atharveeee-netizen/beevil-knievel/LIMITATIONS.md

# ⚠️ BEEVIL KNIEVEL - Engineering Limitations & Scientific Disclosures
**Formal Scientific Constraints, Operational Boundaries, and Validity Scope**  
*Standard: IEEE-HART Peer Review Defense Standard*

---

## 1. DATASET LIMITATIONS & GENERALIZABILITY

### 1.1 Acoustic Training & Benchmark Datasets
- **Geographical & Subspecies Scope**: The real-world acoustic field validation in this repository uses annotated beehive recordings from Zenodo Record [1321278](https://doi.org/10.5281/zenodo.1321278) (NU-Hive and Open Source Beehive projects). These recordings represent European honeybee subspecies (*Apis mellifera carnica* and *Apis mellifera ligustica*) managed in temperate European climates (United Kingdom and Italy).
- **Subspecies Variance**: Subspecies indigenous to tropical or desert climates (e.g., *Apis cerana*, *Apis mellifera scutellata*, or *Apis dorsata*) exhibit differing baseline wingbeat frequencies and fanning dynamics that may require localized retuning of the 4 spectral sub-band filters.
- **Microphone Placement Sensitivity**: Spectral energy amplitudes depend on physical proximity to the active brood cluster. Placement of the INMP441 sensor outside the central comb gap results in acoustic attenuation of up to $6\text{ dB}$, which could delay queenless agitation detection if thresholds are not calibrated to the specific hive geometry.

---

## 2. SYNTHETIC DATA & MODEL PROVENANCE

### 2.1 Cloud Pathology Model (`CloudAdvisorModel`)
- **Parametric Empirical Distributions**: The 1500-sample training dataset (`Synthetic_Hive_Parametric_Dataset.csv`) used to train the Scikit-Learn Random Forest model is **synthetic data** generated from parametric Gaussian distributions.
- **Grounding in Literature**: Distribution parameters ($\mu, \sigma$) are derived directly from empirical ranges published in scientific apiculture literature:
  - Brood thermoregulation dynamics: Southwick & Heldmaier (1987).
  - Colony acoustic spectral shifts: Ferrari et al. (2008), Bencsik et al. (2011).
  - Respiration and metabolic $\text{CO}_2$ spikes: Sensirion Apiculture Application Notes.
- **Operational Reality**: While the model achieves 100% classification accuracy on holdout test splits drawn from these parametric distributions, real-world apiaries experience complex multi-variable interactions (e.g., simultaneous pesticide exposure and starvation) that require continued multi-season empirical calibration.

---

## 3. ON-NODE ALGORITHM BOUNDARIES

### 3.1 CUSUM Thermal Change-Point Detection
- **Progressive Cooling Lead Time**: The claim that CUSUM provides up to a **72-hour early warning** is validated against modeled progressive thermal degradation scenarios where colony thermoregulation fails gradually. In events involving catastrophic physical box destruction or sudden chemical poisoning, cluster collapse occurs faster than the 72-hour window.
- **Diurnal Sensitivity**: The slack parameter $K = 0.15^\circ\text{C}$ successfully rejects normal diurnal oscillations in standard double-walled Langstroth hives. However, single-walled hives deployed in extreme desert climates ($> 45^\circ\text{C}$ day, $< 10^\circ\text{C}$ night) may require dynamic temperature-dependent slack adjustments.

### 3.2 Environmental Acoustic Noise Rejection
- **Heavy Rain Clatter**: High-velocity raindrops striking thin metallic hive roofs produce acoustic energy in the $200 - 600\text{ Hz}$ band that closely mimics pre-swarm worker piping.
- **Cross-Modal Suppression**: To prevent false swarm alarms, the platform mandates cross-modal verification: acoustic swarm alerts are suppressed unless accompanied by a corresponding $\text{CO}_2$ respiration spike ($> 2000\text{ ppm}$) and diurnal solar lux ($> 10,000\text{ Lux}$).

---

## 4. HARDWARE & SENSOR CONSTRAINTS

### 4.1 BME688 MOX Gas Sensor Baseline Drift
- Metal-oxide (MOX) gas sensors undergo baseline resistance drift over 6 to 12 months due to humidity cycling and sensor poisoning by atmospheric siloxanes. A baseline calibration cycle must be executed at the beginning of each apiculture season.

### 4.2 LIS3DH Accelerometer Orientation
- The knockdown tamper alarm requires the node to be rigidly fastened to the hive brood box. Loose mounting introduces structural vibration artifacts from heavy wind gusts that could trip false tamper alerts.

### 4.3 Solar Energy Harvesting in Extended Winter Overcast
- The 3000 mAh LiPo battery provides 90 days of autonomous operation under standard 5-minute transmission duty cycles without any solar input. However, in high-latitude winter regions experiencing $> 100$ consecutive days of heavy cloud cover and temperatures $< -10^\circ\text{C}$, internal battery self-discharge and electrolyte freezing reduce effective capacity by up to 35%.

---

## 5. SIMULATION VS PHYSICAL MEASUREMENT BOUNDARIES

| Engineering Domain | Simulated Metric | Real-World Physical Measurement Boundary |
|---|---|---|
| **ANSYS HFSS RF** | $S_{11} = -24.75\text{ dB}$, Range $= 5.11\text{ km}$ | Range is an analytical Friis link budget derived from simulated far-field gain; field range is subject to non-line-of-sight foliage clutter and Fresnel zone obstruction ($3.2 - 4.5\text{ km}$ typical). |
| **ANSYS Icepak Thermal** | Junction $T_j = 64.45^\circ\text{C}$ @ $45^\circ\text{C}$ amb | Simulated under quiescent ambient air. Forced air convection from natural wind ($1 - 3\text{ m/s}$) reduces physical junction temperatures by $5 - 12^\circ\text{C}$. |
| **ANSYS Maxwell EMI** | Shielding $\text{SE} = 288.5\text{ dB}$ | 288.5 dB is a theoretical analytical result for an unbroken shield. Practical RF testing in an anechoic chamber is bounded by the $100 - 110\text{ dB}$ dynamic range of lab spectrum analyzers. |
