atharveeee-netizen/beevil-knievel/docs/resources/OPEN_SOURCE_REFERENCES.md

# Beevil Knievel - Public Datasets & Industry Standards Index

---

## 📊 Public Audio Datasets for AI Model Training

1. **Zenodo Public Bee Audio Dataset**
   * **Resource**: Public Audio Benchmark for Beehive Swarming & Health Classification
   * **Usage**: Benchmark dataset for training our 200 Hz - 400 Hz acoustic swarming and queenlessness detection models.

2. **Utah State University Bee Audio Dataset**
   * **Resource**: Public Hive Sound Audio Dataset
   * **Usage**: Multi-season continuous acoustic hive recordings used to train noise-suppression algorithms.

---

## ⚡ Open-Source Firmware & Protocol Libraries

1. **RadioLib Sub-GHz LoRa C++ Protocol Library**
   * **Usage**: Hardware abstraction driver for SX126x / nRF52840WL sub-GHz radios.

2. **DallasTemperature 1-Wire C++ Library**
   * **Usage**: Reading multi-drop digital temperature sensors on a single GPIO bus.
