atharveeee-netizen/beevil-knievel/simulations/Beehive_Monitoring_ANSYS_Simulations_Presentation.pptx

## Simulations on Ansys for Beehive Monitoring Device

## Simulation 1: 868 MHz Antenna & Wireless Link Simulation

We are testing Electromagnetics (EM) & Far-Field Wave Propagation. We want to check that our 868 MHz wire antenna connected to the STM32WLE5 (Wio-E5) transfers RF power cleanly through its trace without internal reflections and broadcasts a 3D signal capable of spanning 4km.
For this, we’ll require a Software Module: Ansys HFSS (High-Frequency Structure Simulator) inside Ansys Electronics Desktop (AEDT). We want to evaluate the radiation efficiency and impedance matching of our 868/915 MHz 86mm quarter-wave wire antenna connected to the STM32WLE5 (Wio-E5) microcontroller before manufacturing.
This directly addresses the IEEE HART Coverage Range and Temperature Accuracy KPI by proving that our node can successfully transmit telemetry through a wooden hive structure across long distances(specifically, pass the 4km Line-Of-Sight).

## STEPS of EXECUTION

To execute this, we will
1. Import our 2-layer PCB layout (.ODB++)
2. Construct the 86mm copper wire antenna geometry on the SMA pad and
3. Assign material properties for the FR4 substrate, copper traces, and surrounding wooden hive box.
We will then establish a 3D Air Box with a radiation boundary at λ/4 distance, assign a 50 Ω Lumped Port source at the RF output pin, and execute an interpolating frequency sweep from 700 MHz to 1 GHz. From this setup, we expect to generate an S11 Return Loss plot displaying a sharp resonance dip below -10 dB at 868 MHz, alongside a 3D Far-Field Radiation Pattern showing an omnidirectional gain distribution (> 2 dBi). The design significance of this outcome is that it proves RF energy actually radiates into space rather than reflecting back into the STM32 chip, preventing power loss and validating our long-range claim.

## Simulation 2: Power Integrity & Transient Voltage Droop

This simulation relies on Ansys SIwave and Ansys Electronics Desktop (Nexxim Circuit) to conduct transient Power Distribution Network (PDN) and AC/DC impedance testing.
Our goal is to verify that the 3.3V power rail remains stable during high-current radio transmission bursts, which directly addresses the Energy Consumption KPI and overall system reliability.
By confirming that our ultra-low-power TPS7A02 LDO regulator and decoupling capacitor network handle peak currents smoothly, we ensure the MCU will not experience brownout resets.

The execution steps involve importing the board layout stackup with defined 3.3V and GND planes into SIwave, assigning the regulator VRM output, and modeling the 100 nF and 10 µF decoupling capacitors with their equivalent series resistance. We then apply a transient current load at the STM32 power pin that jumps from a 0.3 µA sleep state to a 120 mA transmit burst for 60 ms, running a time-domain co-simulation over 100 ms. We expect to extract a transient voltage waveform showing that the 3.3V rail droops no lower than ~3.22V during transmission, as well as a PDN impedance curve confirming resistance stays below 1.375 Ω across frequencies up to 100 MHz. The significance of this simulation is that it mathematically guarantees node runtime stability under battery power, proving optimal energy efficiency.

## Simulation 3: Battery & Enclosure Thermal Isolation

This simulation uses Ansys Icepak to evaluate conjugate heat transfer, covering both thermal conduction and natural air convection.
We are performing this analysis to ensure that internal heat generated by the 1000mAh LiPo battery during solar charging or by the MCU during active computing does not conduct into our ambient temperature sensor.
This supports the Temperature Accuracy KPI of IEEE HART by confirming that device self-heating will not introduce artificial offsets into our ambient sensor readings.

## STEPS OF EXECUTION

To set up the simulation, we will import the 3D CAD assembly of our 60 × 50 mm enclosure (.STEP) and PCB into Icepak, assigning a heat dissipation load of 0.15 W to the LiPo battery and 0.05 W to the MCU. We will then set the surrounding air domain to 35°C to match internal hive conditions and run the fluid-thermal solver to compute copper plane conduction and natural airflow.
The expected outcomes are a 3D thermal heat map showing localized heat at the battery (~38°C) while the surrounding board remains cool, along with a thermal cross-section cut plane verifying that the ambient DS18B20 sensor footprint maintains an elevation of <0.1°C relative to internal hive air. The significance of this result is that it proves our board layout thermally isolates critical sensing components, preserving the ±0.5°C temperature accuracy required to evaluate bee colony health accurately.
