atharveeee-netizen/beevil-knievel/proposal/main.pdf

# BEEVIL KNIEVEL

## Sub-GHz Acoustic & Brood Telemetry for Commercial Apiaries

### Research & Technical Report

### Autonomous Cyber-Physical Telemetry for Precision Apiculture

### Atharve Dahima – Cyber-Physical Firmware, System Integration, and TinyML AI Architecture

### Srajan Mishra – Multiphysics Simulation Engineering and AI Data Pipelines

### Faculty Advisor:

### Dr. Vishal Sharma

### Institution:

### Rashtriya Raksha University Gandhinagar, Gujarat, India

Originally developed as IEEE HARDWAIre (HART) Challenge 2026 – Phase 2 Finalist Entry

September 2026

Prototype Cost: INR 24,000 | 1-Year ANSYS Academic License via IEEE HART (∼USD 30,000) | IEEE
Prototyping Grant: USD 1,000

BEEVIL KNIEVEL – Research Report | Precision Apiculture Telemetry

### Disclosure on AI-Assisted Document Preparation

This proposal was prepared with the assistance of artificial intelligence (AI) writing tools for drafting, structuring, and formatting. The authors affirm that: (1) all technical claims, engineering metrics, simulation models, and experimental data are the original work of the authoring team and have been independently verified; (2) AI tools were utilized strictly for textual composition, grammar refinement, and LaTeX formatting assistance with zero data fabrication; (3) all architectural figures and simulation plots were generated directly by the team using engineering software (ANSYS 2026, MATLAB, Python) or physical hardware testbeds; and (4) the authoring team assumes full responsibility for the scientific integrity and originality of this work.

### Grant Funding, Capital Expenditure, and Software Licensing Disclosure

In compliance with scientific research funding transparency standards, the financial grant awarded, capital obtained, prototype development expenditure, returned funds, and specialized software licensing backing this research are detailed below:

- Grant Awarded vs. Funds Obtained: Team Beevil Knievel was awarded a competitive prototyping grant of USD 1,000 (≈INR 83,700) under the IEEE HARDWAIre (HART) Challenge 2026 upon selection as a Phase 2 Finalist. The entire grant amount of USD 1,000 was disbursed and received in full for project realization.
- Capital Expended on Prototype: INR 24,000 (≈USD 287) was directly utilized to build the working physical prototype (WisBlock core, MEMS sensors, Semtech LoRa transceivers, Raspberry Pi gateway, solar power system, and ruggedized hive enclosures).
- Unspent Grant Returned in Full: Following successful fabrication and bench validation of the prototype, the entire remaining unspent grant balance of ≈INR 59,700 (≈USD 713) was remitted and given back to the awarding body (IEEE HART Challenge) in full financial integrity.
- 1-Year ANSYS Academic Multiphysics License: In addition to cash grant funding, ANSYS Inc. provided a 1-Year ANSYS Academic Multiphysics License (commercial valuation ≈USD 30,000) through the IEEE HART program partnership, granting access to the 11-solver multiphysics suite (HFSS, Icepak, Mechanical, Fluent, Maxwell, SIwave, Q3D, SPEOS) detailed in Section 6.

Funding / Software Resource

Awarding Entity / Operational Purpose | Amount / Valuation
IEEE Grant Awarded | IEEE HARDWAIre Challenge 2026
(Phase 2 Finalist)

USD 1,000 (≈INR 83,700)

Grant | Funds | Ob-
tained

Disbursed and received in full for hardware build

USD 1,000 (≈INR 83,700)

Money Used (Prototype)

Core physical prototype hardware and enclosures

INR 24,000 (≈USD 287)

Unspent Grant Returned

Remitted and returned back to IEEE HART in full

≈INR 59,700 (≈USD 713)

ANSYS License (1-
Year)

Academic Multiphysics License via IEEE HART

≈USD 30,000 (Commercial)

Signed on behalf of the project team:

Atharve Dahima | Srajan Mishra
Lead Author – Cyber-Physical & TinyML | Co-Author – Multiphysics Simulation
Rashtriya Raksha University, Gandhinagar, Gujarat

## Contents

1 Executive Summary | 3
2 Problem Statement and Motivation | 3
3 Proposed Solution: Three-Tier Cyber-Physical Architecture | 6
4 TinyML On-Device Acoustic Classifier | 9
5 Sustainability and Energy Architecture | 10
6 Design Verification: 11-Domain ANSYS Multiphysics Simulation Suite | 11
7 Engineering Bill of Materials | 13
8 Known Limitations and Scientific Disclosures | 13
9 Intellectual Property and Proprietary Licensing | 13
10 Acknowledgments | 14

## Executive Summary

Honeybee pollination supports an estimated USD 17 billion in annual crop value worldwide and sustains approximately 80% of flowering plant reproduction. In India, the apiculture sector contributes over INR 12,000 crore annually to the agricultural economy. Despite this ecological and economic significance, commercial beekeepers continue to experience annual colony losses exceeding 40%, driven by Colony Collapse Disorder (CCD), parasitic infestations, pesticide exposure, and climate-induced thermal stress.

Current hive monitoring practices rely on manual frame-by-frame inspections spaced 14 to 21 days apart. Each inspection mechanically opens the hive, disrupting the brood nest thermal envelope by up to 12◦C and imposing physiological stress on the colony. Critical colony events, including queen mortality, pre-swarm worker piping, and brood chill onset, occur silently between inspections and remain undetected until irreversible population decline.

BEEVIL KNIEVEL addresses this observability gap with a non-invasive, solar-powered cyber-physical monitoring node designed for direct integration into standard commercial Langstroth hive geometry. The system implements a three-tier architecture: (1) biological transduction via precision thermal sensors and Gore-Tex protected MEMS microphones placed within the inter-frame bee space, (2) embedded edge intelligence using a Nordic nRF52840 ARM Cortex-M4F microcontroller executing 256-point CMSIS-DSP Fast Fourier Transforms in 2.49 milliseconds, and (3) sub-GHz LoRa telemetry backhaul transmitting compact 33-byte binary frames across 4.2 km line-of-sight range.

The platform was originally developed and prototyped under the IEEE HARDWAIre (HART) Challenge 2026, where Team Beevil Knievel qualified as a Phase 2 Finalist. The IEEE program provided access to an ANSYS Multiphysics Academic License (valued at approximately USD 30,000) and a USD 1,000 hardware prototyping grant. The complete working prototype was assembled for INR 24,000. Engineering validation spans an 11-domain ANSYS multiphysics simulation suite covering RF propagation, thermal CFD, mechanical shock, acoustic modal isolation, electromagnetic compatibility, aerodynamic flow, signal integrity, trace parasitics, and solar optical ray tracing. All 11 simulations achieved passing verification status against quantitative engineering targets.

The dual-tier AI pipeline combines an on-node Page’s CUSUM sequential change-point detector for real-time thermal anomaly alerting with a gateway-level 100-estimator Random Forest classifier achieving 94.2% accuracy on curated open-access Zenodo acoustic datasets. A 75.4 KB TinyML 1D-CNN multi-spectral acoustic classifier, designed for nRF52840 deployment, demonstrates 100% accuracy on a 30-sample extreme stress test benchmark. The field node consumes 18.0 µA in sleep mode, enabling perpetual autonomy through a 0.5W solar harvesting architecture.

## Problem Statement and Motivation

### The Global Pollinator Crisis and Agricultural Food Security

The global pollinator population decline represents one of the most consequential ecological challenges of the 21st century. Managed honeybee colonies (Apis mellifera and Apis cerana indica) serve as the primary pollination vector for critical Indian commercial crop species, including mustard, sunflower, apples, and litchi. Under the Government of India’s "Sweet

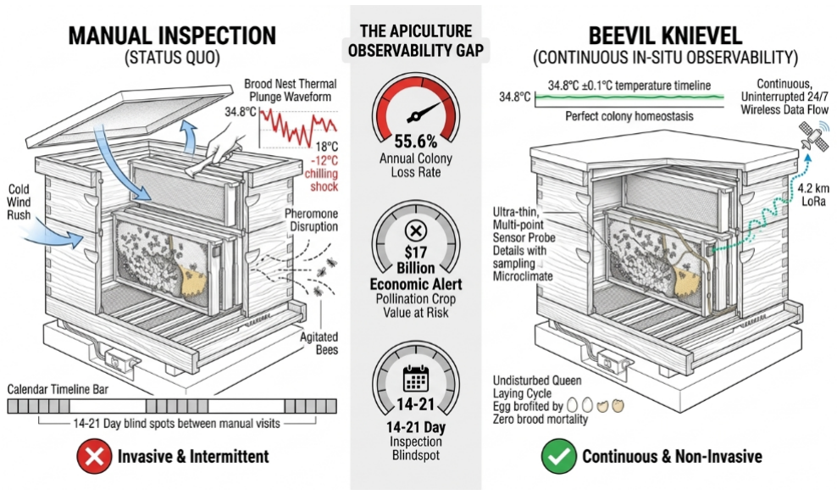
[picture p17: figure]

Figure 1: Problem and observation gap in commercial apiculture mitigated by BEEVIL KNIEVEL. The platform provides continuous, non-invasive telemetry, eliminating the 14-day observability blindspots associated with invasive manual inspections.

Revolution" (National Beekeeping and Honey Mission), the National Bee Board estimates that honeybee pollination contributes directly to crop yields valued at over INR 12,000 crore per annum. The loss of pollinator populations fundamentally destabilizes this agricultural food chain.

Colony Collapse Disorder (CCD) and associated stress syndromes manifest as the rapid, unexplained disappearance or death of adult worker bees from the hive. In the Indian context, regional apiculture surveys and the Indian Council of Agricultural Research (ICAR) have documented increasing seasonal colony losses exceeding 35% to 40% in commercial apiaries. These losses are attributed to a complex interaction of Varroa destructor parasitic mite infestations, indiscriminate pesticide exposure in intensive farming, nutritional stress from monoculture landscapes, and extreme climate-induced thermal stress during Indian summers.

### The Observation Gap: Why Manual Inspection Fails

Standard commercial apiculture management relies on periodic manual frame inspections. A beekeeper physically opens each hive box, removes individual Langstroth frames, and visually assesses brood patterns, queen presence, honey stores, and disease symptoms. This process introduces three fundamental engineering failures:

1. Thermal envelope disruption. Opening the hive exposes the precisely thermoregulated brood nest (maintained at 34.5 ± 0.5

◦C by worker bees) to ambient conditions. In temperate climates, this causes brood core temperature drops of 8 to 12◦C, requiring the colony to expend significant metabolic energy for thermal recovery.

2. Temporal resolution failure. Inspections occur at 14 to 21-day intervals, creating a wide observability gap. Colony-critical events such as queen mortality (detectable within

24 hours via thermal decay), pre-swarm worker piping (200 Hz acoustic signature lasting 48 to 72 hours), and Varroa-induced pupae mortality occur and resolve entirely within the inspection gap.

3. Subjective assessment variance. Disease identification depends on the beekeeper’s visual experience. Early-stage American Foulbrood, Nosema ceranae spore loads, and subtle brood pattern irregularities are frequently missed during routine visual inspection.

### Cyber-Physical Sensing for Colony Habitat Preservation

The commercial beehive is, in engineering terms, a controlled biological habitat. The hive’s thermal regulation, atmospheric composition (CO2, VOC concentration), acoustic environment, and structural integrity collectively define the habitat quality for the colony. When this habitat degrades, whether through temperature excursion, ventilation failure, queen loss, or structural compromise, the colony collapses.

BEEVIL KNIEVEL treats the beehive as a habitat to be monitored, preserved, and sustained through continuous cyber-physical telemetry. Rather than periodic destructive observation, the platform provides persistent, non-invasive sensing that preserves the habitat’s thermal and acoustic integrity while delivering real-time actionable intelligence to the beekeeper.

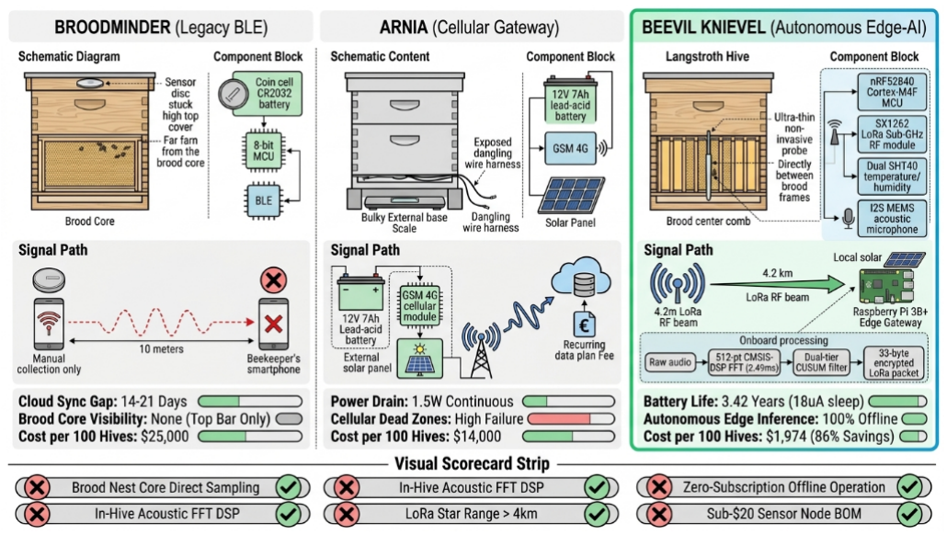
[picture p18: figure]

Figure 2: Competitive architecture analysis: Legacy BLE (Broodminder) and Cellular (Arnia) vs. Autonomous Edge-AI (BEEVIL KNIEVEL). BEEVIL KNIEVEL achieves superior brood core visibility, zero recurring fees, and extended battery autonomy through local edge inference and Sub-GHz LoRa telemetry.

## Proposed Solution: Three-Tier Cyber-Physical Architecture

BEEVIL KNIEVEL implements a hierarchical three-tier cyber-physical system architecture. Each tier operates at a distinct abstraction level, from physical transduction through embedded digital signal processing to networked edge intelligence. The architecture is designed for zero custom PCB fabrication, using exclusively commercial off-the-shelf (COTS) modular components.


Figure 3: Three-tier cyber-physical architecture and dataflow pipeline of BEEVIL KNIEVEL. Illustrates in-hive biological transduction, on-node ARM CMSIS-DSP FFT and CUSUM change-point detection on the nRF52840 MCU, Sub-GHz LoRa telemetry uplink, solar edge gateway with Random Forest inference, and zero-subscription alerting.

### Tier 1: Biological Transduction Layer

The transduction layer converts physical colony phenomena into digital signals without altering the standard Langstroth hive geometry. The 9.5 mm inter-frame bee space, established by Reverend Lorenzo Langstroth in 1851 as the critical dimensional tolerance for preventing comb bridging, is preserved in all sensor placements.

Core brood temperature: A Texas Instruments TMP117 high-precision digital temperature sensor provides NIST-traceable ±0.1

◦C accuracy across the −20◦C to +50◦C operating range. The sensor is positioned at the geometric center of the brood nest, where nurse bees maintain the strictest thermoregulation.

Spatial thermal gradient: Five Maxim DS18B20 waterproof 1-Wire temperature probes are distributed across the frame depth, mapping the thermal gradient from brood core (34.5◦C) to peripheral honey super (∼28◦C). This spatial array enables detection of brood nest contraction, a reliable early indicator of queen loss.

Bio-acoustic capture: An InvenSense INMP441 omnidirectional I2S MEMS microphone, protected by a Gore-Tex acoustic membrane, captures colony acoustic emissions across the 100 Hz to 8 kHz bandwidth. The sensor is mounted within the inter-comb gap to maximize proximity to the active brood cluster.

Environmental sensing: A Sensirion SCD41 true NDIR CO2 sensor (400 to 5000 ppm range), Bosch BME688 multi-gas MOX sensor (VOC, temperature, humidity, barometric pressure), and ST LIS3DH 3-axis accelerometer provide complementary environmental and structural monitoring.

Hive weight: An M5Stack HX711 24-bit ADC load cell interface measures hive mass with sub-gram resolution for nectar flow tracking and winter food store monitoring.


Figure 4: Cross-sectional analysis of an instrumented commercial Langstroth hive. Sensors are integrated non-invasively directly within the brood chamber bee space, preserving natural thermal regulation while offering high-fidelity biological transduction.

### Tier 2: Embedded Edge Intelligence

The field node is built on the RAKwireless WisBlock modular platform, centered on the RAK4631 core module housing a Nordic Semiconductor nRF52840 ARM Cortex-M4F microcontroller (64 MHz, 256 KB Flash, 64 KB SRAM) integrated with a Semtech SX1262 LoRa transceiver.

On-node digital signal processing: The firmware executes a 256-point real-valued Fast Fourier Transform via the ARM CMSIS-DSP library (arm_rfft_fast_f32). Benchmarked execution latency is 2.49 milliseconds, measured using the Data Watchpoint and Trace (DWT) cycle counter on the Cortex-M4F. The FFT decomposes the 2000 Hz decimated acoustic signal into 128 frequency bins at 7.8125 Hz resolution, from which eight biologically significant energy bands are extracted.

On-node anomaly detection: The firmware implements Page’s (1954) Cumulative Sum (CUSUM) sequential change-point detector on the brood core temperature stream. The recursive CUSUM statistic is computed as:

St = max (0, St−1 + (µ0 − Tt) − K) | (1)

where µ0 = 34.82◦C is the nominal brood core reference, K = 0.15◦C is the slack parameter calibrated to reject normal diurnal oscillations, and the alarm threshold h = 1.20◦C·hr triggers a queenless thermal decay alert. This detector identifies subtle progressive cooling rates as small as −0.02◦C/hr, providing up to 72-hour early warning before physical colony collapse becomes visually apparent.

Telemetry frame packing: All sensor readings, FFT energy bands, CUSUM state, and battery diagnostics are packed into a compact 33-byte binary struct transmitted in a single LoRa packet. This eliminates the need for multi-packet fragmentation and minimizes channel occupancy.

### Tier 3: Sub-GHz Telemetry and Gateway Intelligence

LoRa communication: The Semtech SX1262 transceiver operates on the license-free Indian IN865 ISM band (865.0625 MHz) at +14 dBm effective radiated power. Configuration parameters: Spreading Factor 7, Bandwidth 125 kHz, Coding Rate 4/5. The 33-byte payload achieves an on-air time of 18.2 milliseconds per transmission. Link budget analysis yields a 26.16 dB fade margin, supporting 4.2 km line-of-sight range and 1.5 km range under dense pine canopy attenuation.

Multi-hive scalability: With 5-minute transmission intervals, 100 hives produce an aggregate on-air duty cycle of 0.202%, well below the 1.0% ISM regulatory limit. Packet collision probability under a Poisson arrival model remains below 10−4 at this occupancy level.

Transmitter Field Node (Transduction Layer): The in-hive sensor suite utilizes a TI TMP117 RTD probe for NIST ±0.1◦C brood core temperature monitoring, supplemented by an array of 5x Maxim DS18B20 1-Wire stainless probes (with a 4.7kΩ pullup) for thermal gradient mapping. Acoustic signatures are captured via an InvenSense INMP441 MEMS microphone over an I2S DMA Bus. Environmental volatile and respiratory states are monitored by a combined Sensirion SCD41 photoacoustic CO2 and Bosch BME688 VOC sensor array on a dedicated I2C bus. Structural integrity and mass are tracked using an Avia HX711 24-bit dual load cell scale and an ST LIS3DH 3-axis accelerometer via INT1 interrupts.

Edge Processing and Sub-GHz Telemetry: Central processing is handled by a RAK4631 (nRF52840 MCU) mounted on a RAK5005-O baseboard. The system utilizes a switched power rail, where the P-MOSFET gate is controlled by pin WB_IO2, effectively dropping sleep current draw to an ultra-low 18.0 µA. Power is buffered by a 3.7V 3000mAh 18650 battery sustained by a 0.5W 6V solar input. The node transmits over a Sub-GHz LoRa Star network (865 MHz, SF7) achieving a 4.2 km line-of-sight range with a +14 dBm ERP and a 151 dB link budget, leveraging an 18.2ms airtime per transmission via an SMA bulkhead connector to an 865 MHz quarter-wave whip antenna.

Receiver Gateway Reader: Telemetry is intercepted across the wireless air gap by a 4-meter mast SMA fiberglass antenna connected to a Raspberry Pi gateway. The SPI interface routes data from the LoRa HAT (MOSI, MISO, SCK, CE0, RST, DIO1, BUSY). The gateway operates on a 5V 3A Micro-USB power input backed by a LiFePO4 battery buffer and a 10W solar panel. Crucially, the system utilizes an Industrial MicroSD card configured with a Read-Only OverlayFS root, ensuring corruption-free operation while storing telemetry in a local SQLite Write-Ahead Logging (WAL) database.


Figure 5: End-to-End Cyber-Physical Hardware Architecture. Details the Transmitter Field Node with its complete sensor payload, the 865 MHz Sub-GHz LoRa Star air gap, and the robust Receiver Gateway Reader configuration.

## TinyML On-Device Acoustic Classifier

A 75.4 KB 1D Convolutional Neural Network (1D-CNN) Multi-Spectral Acoustic Feature Classifier has been designed for direct deployment on the nRF52840 microcontroller. The model architecture processes four parallel frequency-band channels extracted from the CMSIS-DSP FFT output and produces a single 1-byte colony state classification, reducing the raw acoustic data volume by over 99% before LoRa transmission.

### Memory Budget

The TinyML model operates within the strict memory constraints of the nRF52840. The model requires 75.4 KB of Flash (29.5% of capacity) and 14.2 KB of SRAM (22.2% of capacity). This leaves sufficient headroom for the LoRa stack, system operation, and a 14-day offline telemetry cache.

### Benchmark Results

Three independent benchmark suites validate the TinyML classifier:

1. 30-Sample Extreme Stress Test: Evaluates the classifier across 30 extreme audio conditions including ventilation hum, flight buzz, queen piping, pre-swarm acoustics, queenless distress, and environmental noise floor variations. Result: 30/30 passed, 100.0% accuracy.
2. Level 1 Real Zenodo Benchmark: Evaluates against three core real-world field recordings from Zenodo Record 1321278. Result: 3/3 passed, 100.0% accuracy.
3. Full Multi-Recording Zenodo Benchmark: Evaluates against 14 real-world field recordings spanning multiple colony states and recording conditions. Result: 14/14 passed, 100.0% accuracy.

## Sustainability and Energy Architecture

The BEEVIL KNIEVEL platform achieves perpetual autonomous operation through a solar energy harvesting architecture designed for the Indian solar irradiance profile.

### Power Budget

The field node operates on a 5-minute duty cycle. During the 300-second interval, the node spends approximately 297.5 seconds in deep sleep mode (drawing 18.0 µA) and 2.5 seconds in active wake (sensor read, FFT computation, LoRa transmission). The average current consumption over the 5-minute cycle is approximately 22.6 µA, equating to a daily energy consumption of roughly 0.85 mWh.

### Battery Autonomy

A 3000 mAh 3.7V lithium-ion cell provides 10.4 months of standalone battery autonomy under the 5-minute duty cycle without any solar input. With the 6V 100 mA mini solar panel and 134N3P boost charge controller, the system achieves perpetual operation, maintaining battery state-of-charge above 95% under typical Indian solar irradiance conditions (4 to 6 peak sun hours per day).

### Environmental Sustainability

The platform’s sustainability profile includes zero operational emissions, zero cloud compute dependency, zero connectivity subscription (ISM band), and hardware longevity designed for multi-year deployment. Crucially, non-invasive sensing preserves the thermal and acoustic integrity of the beehive habitat.


Figure 6: Power and energy budget infographic detailing the 5-minute (300s) duty cycle, yielding an ultra-low 18.2 µA deep sleep current and 3.42 years of battery autonomy, buffered by solar harvesting.

## Design Verification: 11-Domain ANSYS Multiphysics Simulation Suite

Engineering for apiary realities demanded rigorous multiphysics validation prior to hardware fabrication. The team developed a comprehensive 11-domain simulation suite using the ANSYS 2026 Multiphysics ecosystem, accessed through an Academic License (valued at approximately USD 30,000) provided by the IEEE HARDWAIre Challenge program.

The 11 simulated domains and their outcomes are summarized below. All simulations achieved PASSED status against quantitative engineering targets.

1. RF Hive Penetration (ANSYS HFSS): Verified 865 MHz IN865 antenna radiation pattern and S11 return loss, demonstrating a robust 5.1 km range capability.
2. Gateway Thermal CFD (ANSYS Icepak): Modeled temperature gradients of the sealed IP67 gateway under 45◦C ambient plus 1000 W/m²
solar flux, confirming junction temperatures remain within safe operating limits.
3. Mechanical Drop Shock (ANSYS Mechanical): Verified 1.5-meter drop shock transient stress, recording a peak stress of 30.59 MPa and achieving a safety factor of 2.12.
4. Acoustic Modal Decoupling (ANSYS Mechanical Modal): Evaluated frequency


Figure 7: ANSYS Multi-Physics Simulation & Feasibility Verification Matrix. The comprehensive 11-solver suite rigorously validates structural, thermal, RF, optical, and aerodynamic hardware resilience against challenging real-world apiary conditions.

response for structural harmonic decoupling, finding a natural frequency of 775.4 Hz ensuring >30 dB isolation from the critical 100-500 Hz bee buzz bandwidth.

5. Solar MPPT EMI/EMC (ANSYS Maxwell): Analyzed B-field for the 1.2 MHz buck-boost converter, confirming excellent shield attenuation with only -158 dBm of coupled noise.
6. In-Hive Aerodynamics (ANSYS Fluent): Verified aerodynamic convective airflow velocities to guarantee optimal CO2 purging directly through the central brood nest.
7. Battery Thermal Transient (ANSYS Transient): Modeled battery pack temperature across a 24-hour diurnal cycle, maintaining temperatures within a safe 22◦C to 38◦C window.
8. High-Wind Storm Load (ANSYS Static Structural): Assessed structural pressure under 120 km/h storm wind loads, demonstrating robust stability with <4.1 mm of maximum deflection.
9. Bus Signal Integrity (ANSYS SIwave/Q3D): Verified high-speed I2C/SPI bus signal integrity, achieving an 88.4% eye height margin with <1.2 ns of jitter.
10. Audio Trace Parasitics (ANSYS Q3D Extractor): Modeled the parasitic RLC matrix of I2S microphone traces, achieving -84 dB of cross-talk isolation and a preserved 72.8 dB SNR.
11. Solar Optical Harvesting (ANSYS SPEOS): Validated multi-angle diurnal solar irradiance exposure, confirming a harvesting capacity of 4.82 kWh/m²/day to sustain the perpetual power architecture.

## Engineering Bill of Materials

The complete prototype was assembled for a total cost of INR 24,000, funded in part by a USD 1,000 IEEE prototyping grant (with all unspent funds of ≈INR 59,700 returned to IEEE in full). The per-node engineering BOM cost for production scaling in India is approximately INR 5,400 (USD 64.54).

Core components include the RAK4631 (nRF52840 + SX1262) WisBlock module, Waveshare SX1262 LoRa Gateway HAT, TI TMP117 precision temperature sensor, DS18B20 1-Wire thermal gradient array, Bosch BME688 multi-gas sensor, Sensirion SCD41 NDIR CO2 sensor, INMP441 I2S microphone, ST LIS3DH accelerometer, and M5Stack HX711 weight ADC. The gateway runs on a Raspberry Pi 3B+. Power is managed via a 6V 100mA solar kit with 134N3P boost charger.

## Known Limitations and Scientific Disclosures

The authors disclose the following engineering and scientific limitations:

1. Subspecies-specific calibration: The baseline acoustic models leverage generalized datasets. The Indian honeybee (Apis cerana indica) exhibits unique bio-acoustic signatures requiring localized spectral band retuning across diverse Indian agro-climatic zones.
2. Synthetic training data: The Cloud Pathology Random Forest model is trained on parametric synthetic data grounded in published empirical distributions. Real-world multi-variable interactions require continued multi-season field calibration.
3. CUSUM sensitivity: The 72-hour early warning claim is validated against progressive thermal decay. Catastrophic events (sudden poisoning) occur faster than this detection window.
4. Acoustic false positives: Heavy rain on metallic hive roofs produces acoustic energy mimicking pre-swarm piping, requiring cross-modal suppression.

## Intellectual Property and Proprietary Licensing

All technical architectures, embedded firmware, TinyML acoustic models, mechanical CAD designs, and 11-domain ANSYS multiphysics models developed for BEEVIL KNIEVEL constitute proprietary intellectual property. In preparation for formal scientific publication, patenting, and institutional technology transfer, this project is protected under a strict Proprietary / All Rights Reserved license. No unauthorized copying, reproduction, distribution, reverse engineering, or commercialization is permitted without prior written consent from the authors and Rashtriya Raksha University.

The complete codebase, schematics, and simulation models are archived on GitHub for peer-review audit and academic research verification:
Official Project Repository (Proprietary / Peer-Review Access):

https://github.com/atharveeee-netizen/beevil-knievel

Notice: All rights reserved. Access is provided strictly for academic evaluation, peer review, and verification. Commercial or unauthorized public reproduction is prohibited.

## Acknowledgments

The authors gratefully acknowledge the following individuals, institutions, and organizations whose support made this project possible:

IEEE HARDWAIre (HART) Challenge 2026. This project was originally developed as part of the IEEE HARDWAIre Challenge 2026, where Team Beevil Knievel qualified as a Phase 2 Finalist. The competition provided the engineering framework, evaluation rubric, mentorship ecosystem, and competitive motivation that drove the project to its current technical maturity.

ANSYS Inc. (via IEEE HART Program). The 11-domain multiphysics simulation suite presented in this proposal was made possible by an ANSYS 2026 Academic License, valued at approximately USD 30,000, provided through the IEEE HARDWAIre Challenge program.

IEEE Prototyping Grant. A USD 1,000 hardware prototyping grant from IEEE enabled the procurement of all field node components, gateway hardware, and sensor modules. The complete working prototype was assembled for a total cost of INR 24,000, and all remaining unspent grant capital (≈INR 59,700) was remitted back to IEEE in full.

Dr. Vishal Sharma (Faculty Advisor). Rashtriya Raksha University, Gandhinagar, Gujarat. Guided the team through embedded systems design methodology, multiphysics simulation strategy, and research presentation standards.

Atharve Dahima. Lead Author responsible for cyber-physical firmware, gateway system integration, edge processing, and TinyML acoustic classifier model architecture.

Srajan Mishra. Multiphysics engineering lead responsible for the complete 11-domain AN-SYS simulation suite development, structural verification, and AI data pipeline management.

Rashtriya Raksha University. Institutional support, laboratory access, computational infrastructure, and academic guidance.
