atharveeee-netizen/beevil-knievel/assets/video_sources/SHOT_CONTACT_SHEET.pdf

# BEEVIL KNIEVEL — VIDEO SHOT CONTACT SHEET

Master Source Extraction & Ethical Provenance Audit | Scene 01: Real-World Problem Context
Thumbnail | Shot Identifier & Purpose | Source & Legal Provenance | Timing & Codec Verification

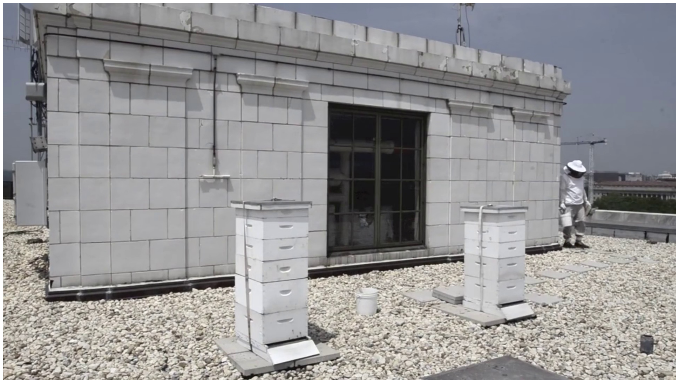
[picture p23: figure]

| SHOT-001: SHOT-001_apiary_establishing.mp4 Purpose: apiary wide shot Description: Establishing wide panoramic view of dual Langstroth multi-super beehives situated on gravel rooftop apiary at USDA headq... Story Role: Establishes commercial apiary physical setting and outdoor operational environment prior to hive int... | Source: People's Garden Apiary and Pollinator Ga... Creator: USDA Natural Resources Conservation Service / Wayne Bogovich & Lance Cheung License: Public Domain (17 U.S.C. § 105) Status: APPROVED BEEVIL Truth: External Context Only | Start: 00:01:23.000 | End: 00:01:26.500 Duration: 3.5s (83 frames) Format: 1920x1080 @ 24.0 fps (H.264 / AAC) SHA256: 7488ff0ca1dc5716a56a2b1ca5b6...

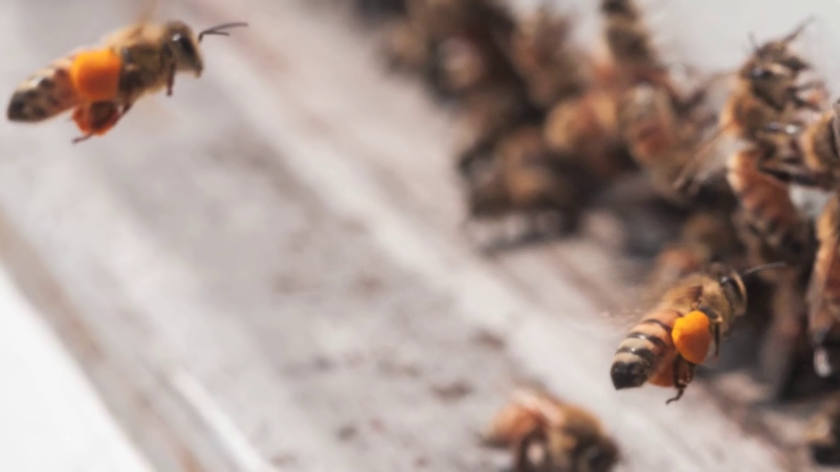
[picture p24: figure]

| SHOT-002: SHOT-002_beekeeper_approach.mp4 Purpose: beekeeper approaching hive Description: Beekeeper in full white protective bee suit, helmet veil, and leather gloves carries smoker and hive tool across the gra... Story Role: Demonstrates human physical presence and the manual overhead involved in conventional apiary monitor... | Source: People's Garden Apiary and Pollinator Ga... Creator: USDA Natural Resources Conservation Service / Wayne Bogovich & Lance Cheung License: Public Domain (17 U.S.C. § 105) Status: APPROVED BEEVIL Truth: External Context Only | Start: 00:01:26.500 | End: 00:01:30.500 Duration: 4.0s (95 frames) Format: 1920x1080 @ 24.0 fps (H.264 / AAC) SHA256: 09651dd369fda0314a68eeeed718...

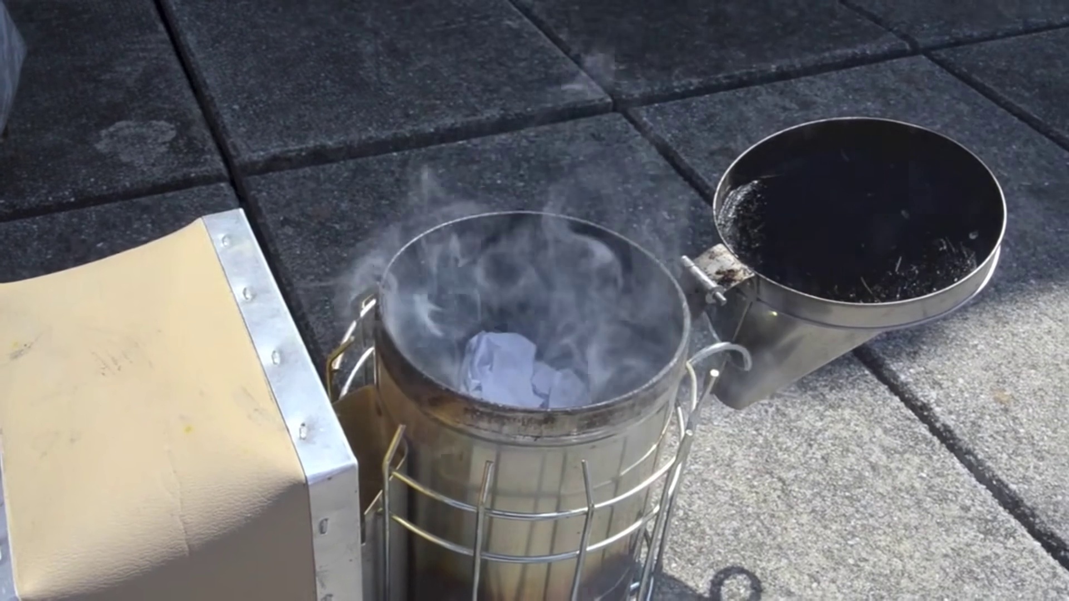
[picture p25: figure]

| SHOT-003: SHOT-003_smoker.mp4 Purpose: smoker / hive preparation Description: Close-up macro of beekeeper loading dry pine needles into the combustion chamber of the stainless-steel bee smoker, pump... Story Role: Illustrates traditional smoke pacification procedure used by apiarists to suppress alarm pheromones ... | Source: People's Garden Apiary and Pollinator Ga... Creator: USDA Natural Resources Conservation Service / Wayne Bogovich & Lance Cheung License: Public Domain (17 U.S.C. § 105) Status: APPROVED BEEVIL Truth: External Context Only | Start: 00:01:10.500 | End: 00:01:14.000 Duration: 3.5s (83 frames) Format: 1920x1080 @ 24.0 fps (H.264 / AAC) SHA256: 21a4a78e823ca413c8db03b45bcc...

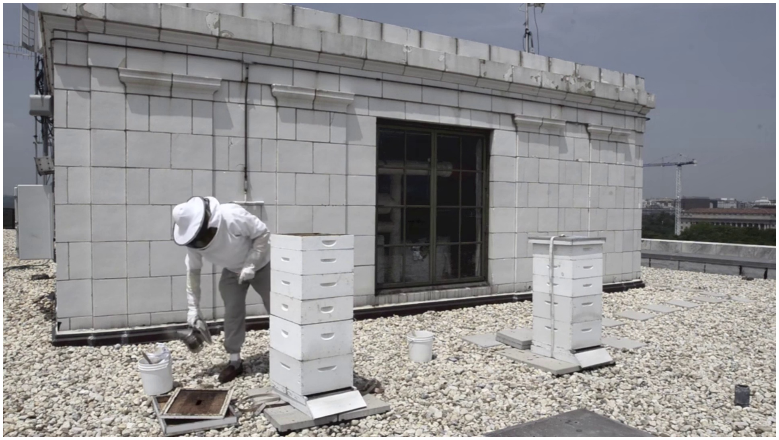
[picture p26: figure]

| SHOT-004: SHOT-004_hive_opening.mp4 Purpose: opening hive Description: Beekeeper unseals inner cover of the upper Langstroth box with a hive tool, puffing tranquilizing smoke into the seam to... Story Role: Documents the physical disturbance caused to hive microclimate and colony stress during manual inspe... | Source: People's Garden Apiary and Pollinator Ga... Creator: USDA Natural Resources Conservation Service / Wayne Bogovich & Lance Cheung License: Public Domain (17 U.S.C. § 105) Status: APPROVED BEEVIL Truth: External Context Only | Start: 00:01:44.000 | End: 00:01:47.500 Duration: 3.5s (83 frames) Format: 1920x1080 @ 24.0 fps (H.264 / AAC) SHA256: 09864365fc941db6f35be723b174...

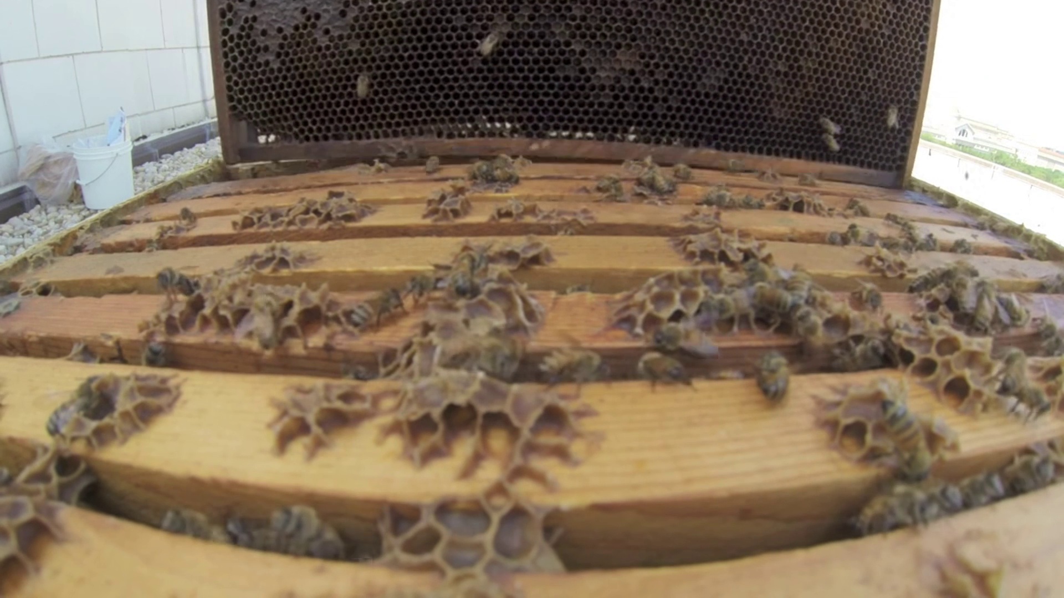
[picture p27: figure]

SHOT-005: SHOT-005_frame_removal.mp4 Purpose: removing frame Description: Direct overhead POV into the open Langstroth hive body as beekeeper pries propolis seal and lifts deep wooden brood fram... Story Role: Visually communicates manual frame extraction required to evaluate internal colony health under stat... | Source: People's Garden Apiary and Pollinator Ga... Creator: USDA Natural Resources Conservation Service / Wayne Bogovich & Lance Cheung License: Public Domain (17 U.S.C. § 105) Status: APPROVED BEEVIL Truth: External Context Only | Start: 00:02:04.500 | End: 00:02:08.500 Duration: 4.0s (95 frames) Format: 1920x1080 @ 24.0 fps (H.264 / AAC) SHA256: e41bb5938748b9e74ca7bc164079...

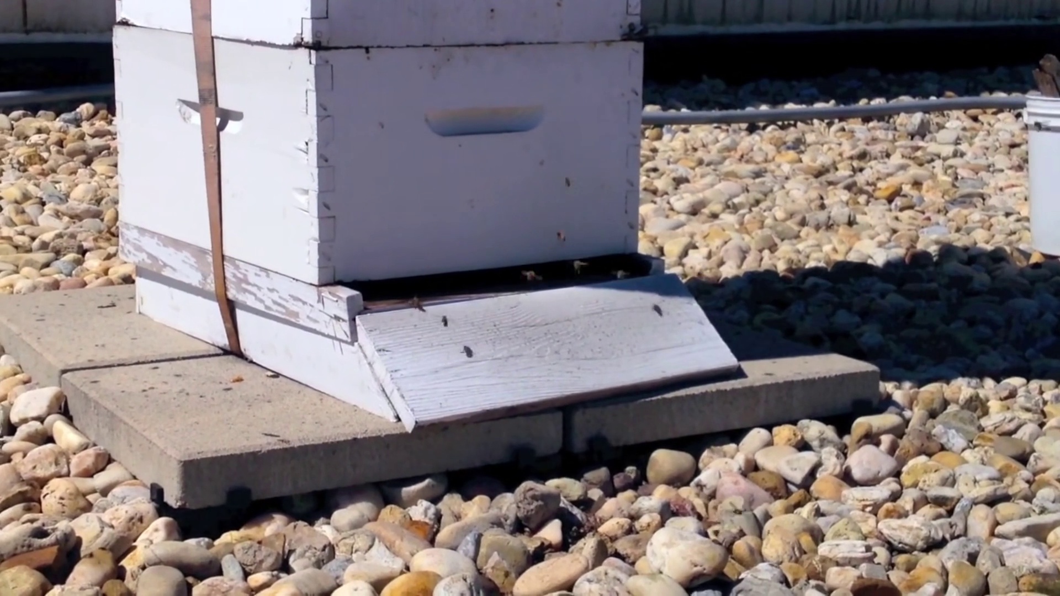
[picture p28: figure]

SHOT-006: SHOT-006_frame_inspection.mp4 Purpose: close-up inspection Description: 1080p close-up of active Italian honeybees arriving at the hive bottom entrance board, exhibiting heavy traffic and poll... Story Role: Contrasts external activity observation against the hidden internal state of brood health and colony... | Source: People's Garden Apiary and Pollinator Ga... Creator: USDA Natural Resources Conservation Service / Lance Cheung License: Public Domain (17 U.S.C. § 105) Status: APPROVED BEEVIL Truth: External Context Only | Start: 00:00:08.000 | End: 00:00:12.000 Duration: 4.0s (95 frames) Format: 1920x1080 @ 24.0 fps (H.264 / AAC) SHA256: cad92b94ee2116e87bb7135dc20f...

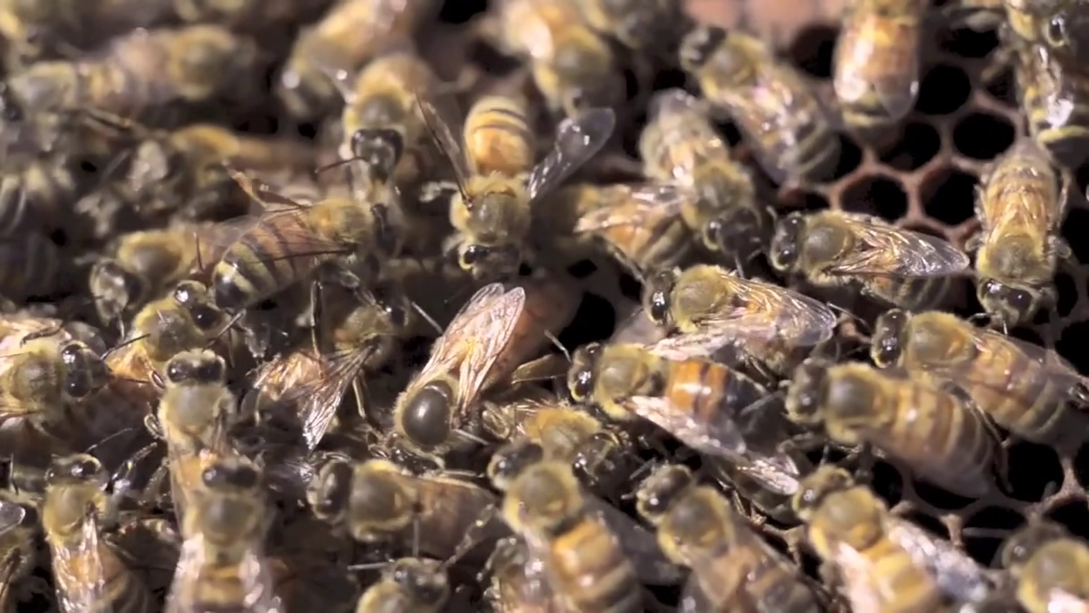
[picture p29: figure]

SHOT-007: SHOT-007_brood_closeup.mp4 Purpose: brood / bees / frame Description: High-definition macro video of nurse and worker honeybees crawling over capped brood cells, actively fanning wings and a... Story Role: Provides visual proof of the biological target: the brood nest cluster whose acoustic signals and 35... | Source: People's Garden Apiary and Pollinator Ga... Creator: USDA Natural Resources Conservation Service / Wayne Bogovich & Lance Cheung License: Public Domain (17 U.S.C. § 105) Status: APPROVED BEEVIL Truth: External Context Only | Start: 00:02:35.000 | End: 00:02:39.000 Duration: 4.0s (95 frames) Format: 1920x1080 @ 24.0 fps (H.264 / AAC) SHA256: 60f32d57b796d272b2967dd2c759...
