atharveeee-netizen/beevil-knievel/assets/video_sources/proxy/SHOT-001_first.jpg

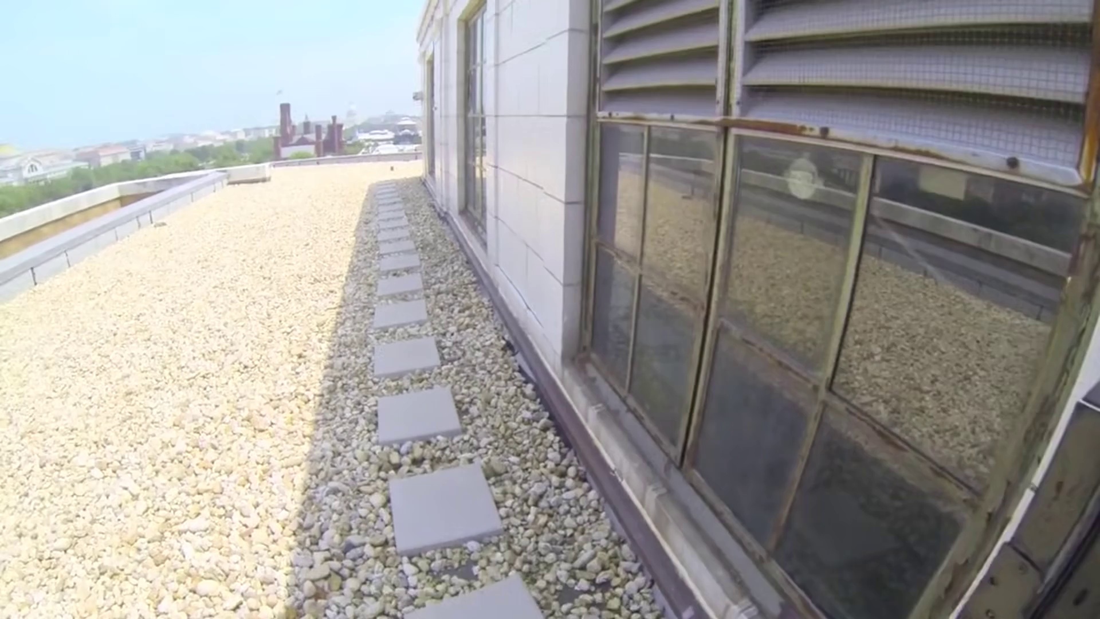
assets/video_sources/proxy/SHOT-001_first.jpg
