atharveeee-netizen/beevil-knievel/assets/video_sources/proxy/SHOT-001_last.jpg

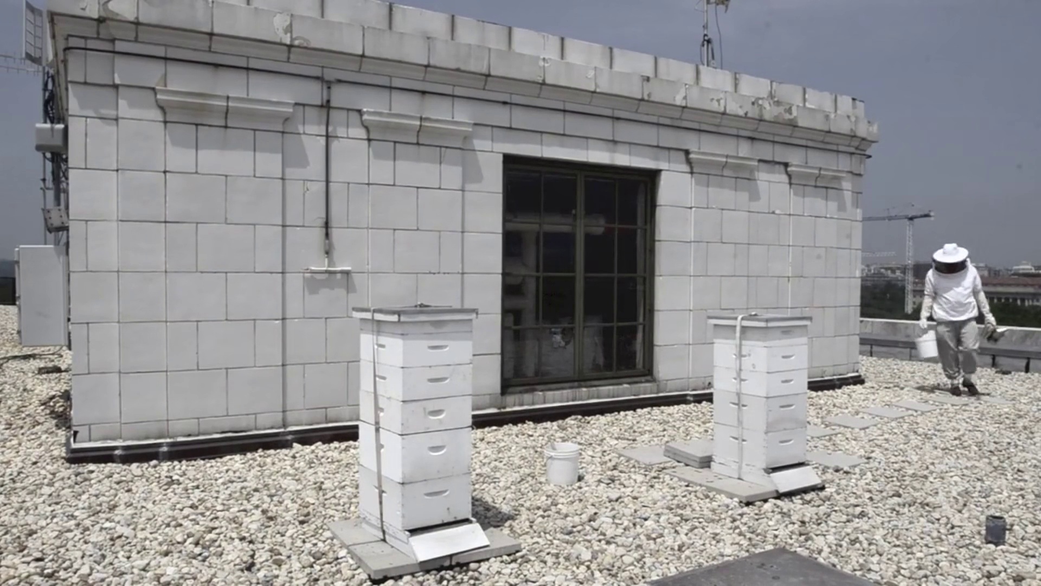
assets/video_sources/proxy/SHOT-001_last.jpg
