atharveeee-netizen/beevil-knievel/assets/video_sources/proxy/SHOT-002_last.jpg

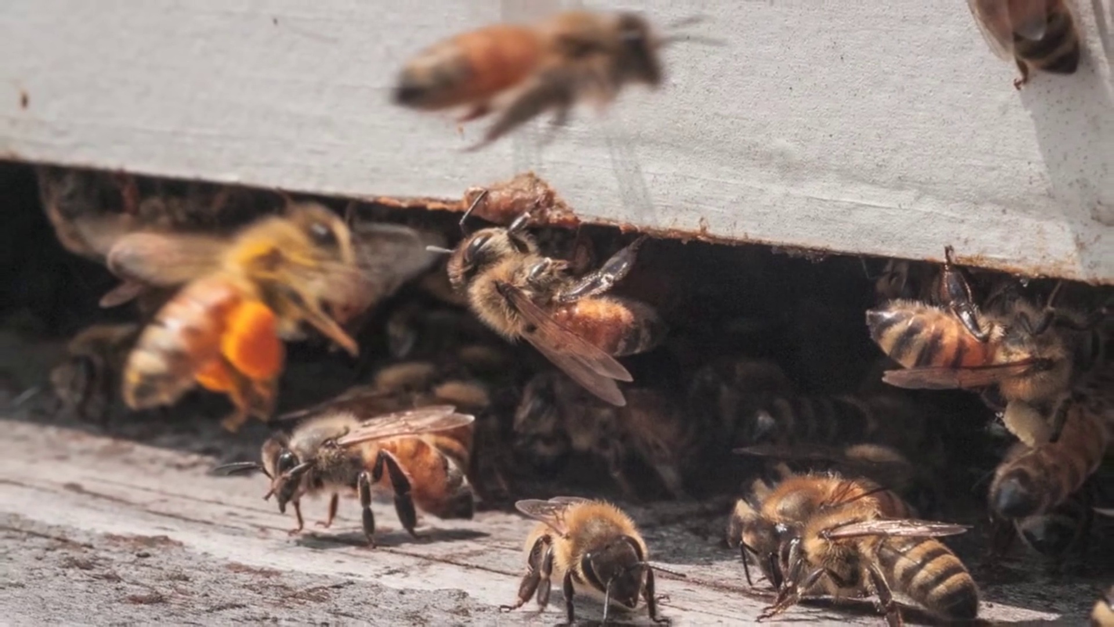
assets/video_sources/proxy/SHOT-002_last.jpg
