atharveeee-netizen/beevil-knievel/assets/video_sources/proxy/SHOT-003_first.jpg

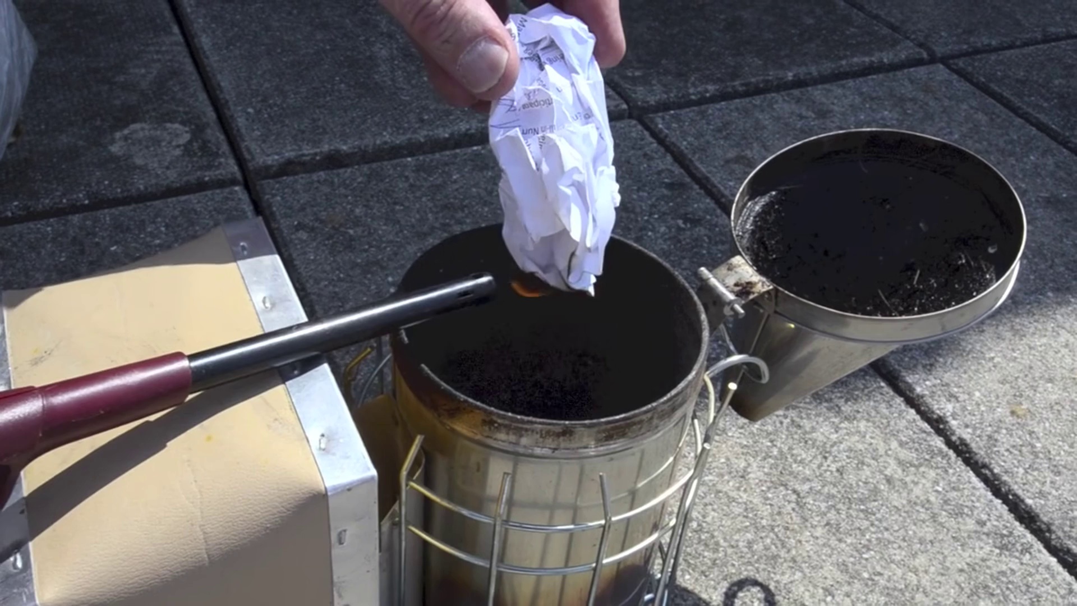
assets/video_sources/proxy/SHOT-003_first.jpg
