atharveeee-netizen/beevil-knievel/assets/video_sources/proxy/SHOT-003_last.jpg

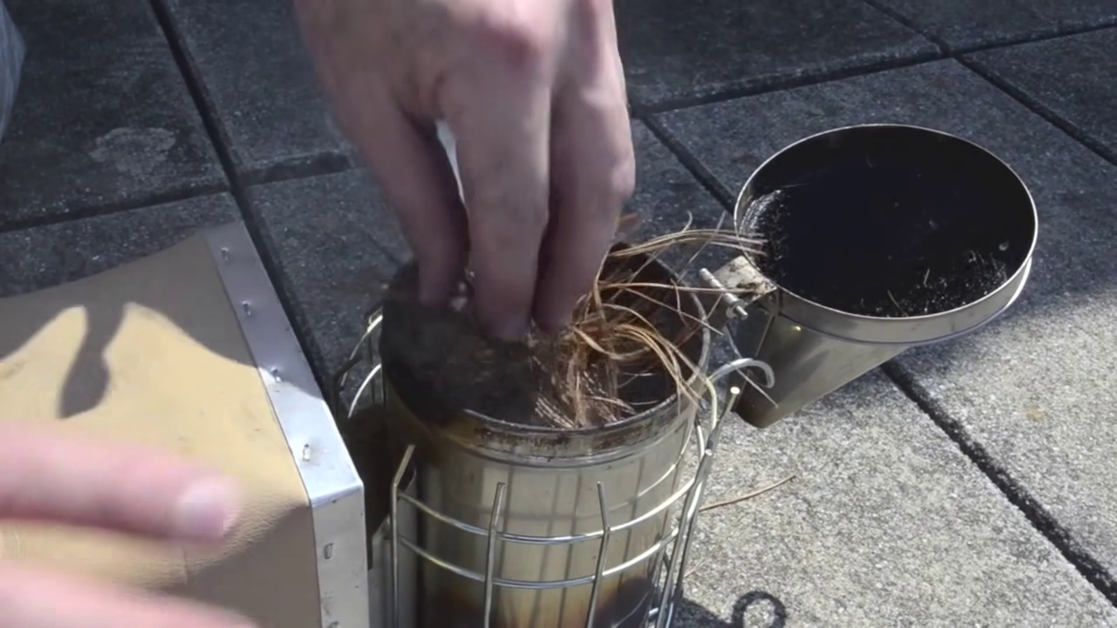
assets/video_sources/proxy/SHOT-003_last.jpg
