atharveeee-netizen/beevil-knievel/assets/video_sources/proxy/SHOT-004_first.jpg

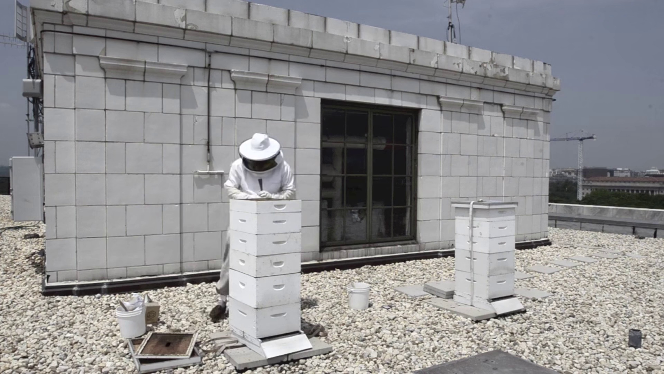
assets/video_sources/proxy/SHOT-004_first.jpg
