atharveeee-netizen/beevil-knievel/assets/video_sources/proxy/SHOT-004_last.jpg

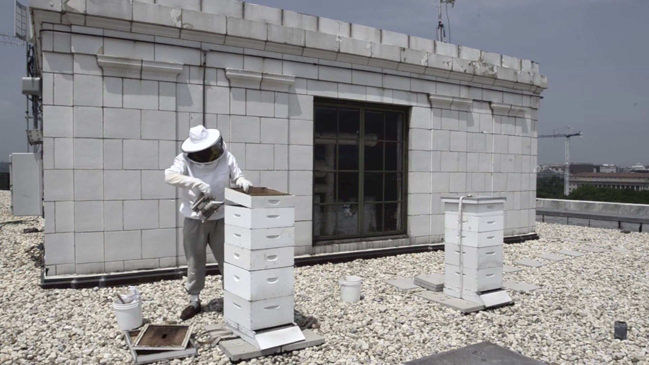
assets/video_sources/proxy/SHOT-004_last.jpg
