atharveeee-netizen/beevil-knievel/assets/video_sources/proxy/SHOT-005_first.jpg

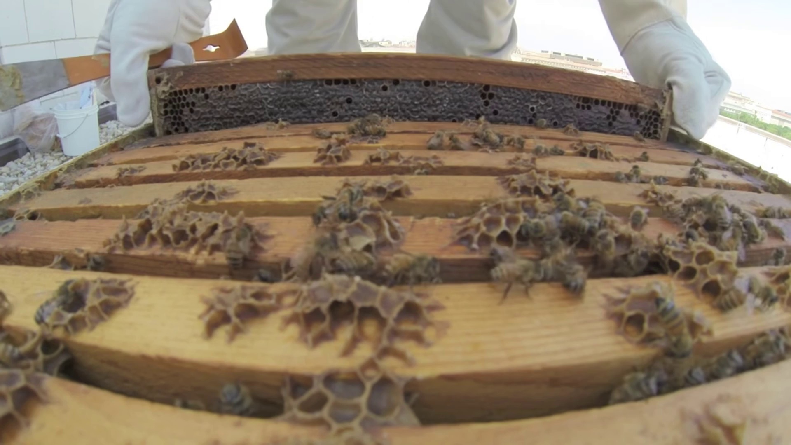
assets/video_sources/proxy/SHOT-005_first.jpg
