atharveeee-netizen/beevil-knievel/assets/video_sources/proxy/SHOT-005_last.jpg

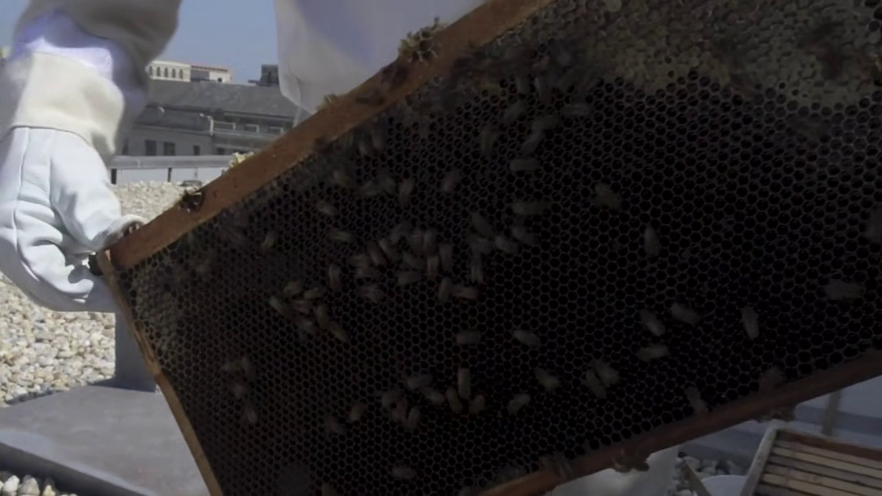
assets/video_sources/proxy/SHOT-005_last.jpg
