atharveeee-netizen/beevil-knievel/assets/video_sources/proxy/SHOT-006_first.jpg

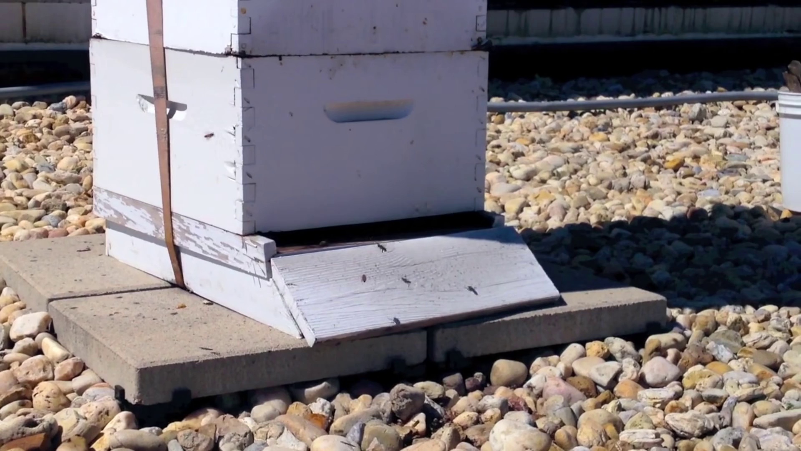
assets/video_sources/proxy/SHOT-006_first.jpg
