atharveeee-netizen/beevil-knievel/assets/video_sources/proxy/SHOT-006_last.jpg

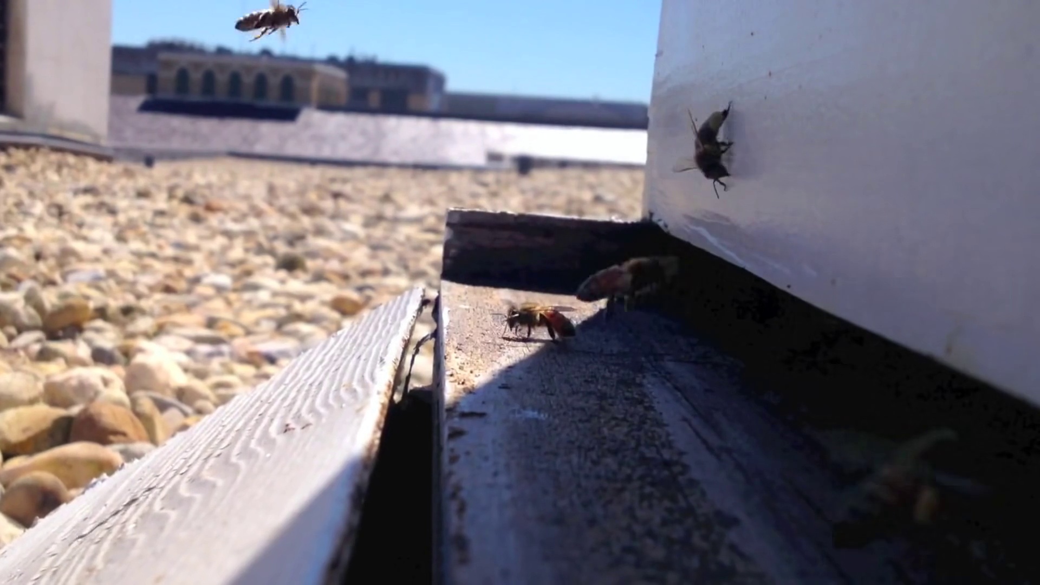
assets/video_sources/proxy/SHOT-006_last.jpg
