atharveeee-netizen/beevil-knievel/assets/video_sources/proxy/SHOT-007_first.jpg

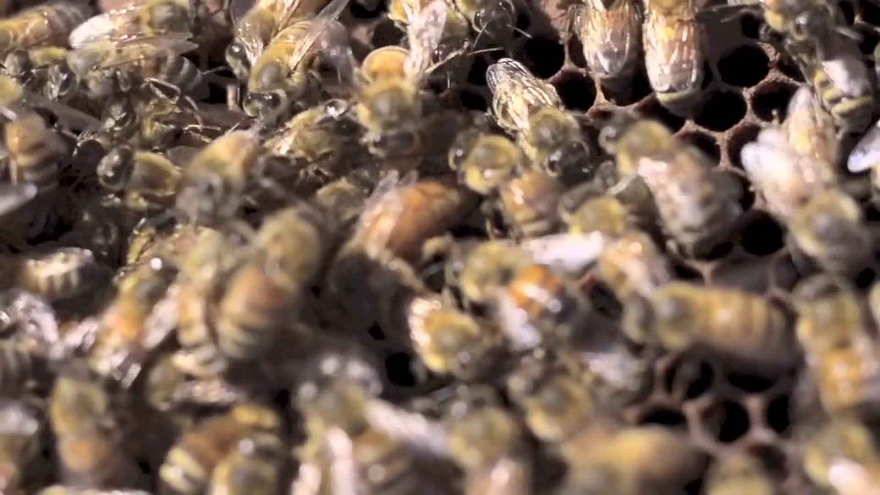
assets/video_sources/proxy/SHOT-007_first.jpg
