atharveeee-netizen/beevil-knievel/assets/video_sources/proxy/SHOT-007_last.jpg

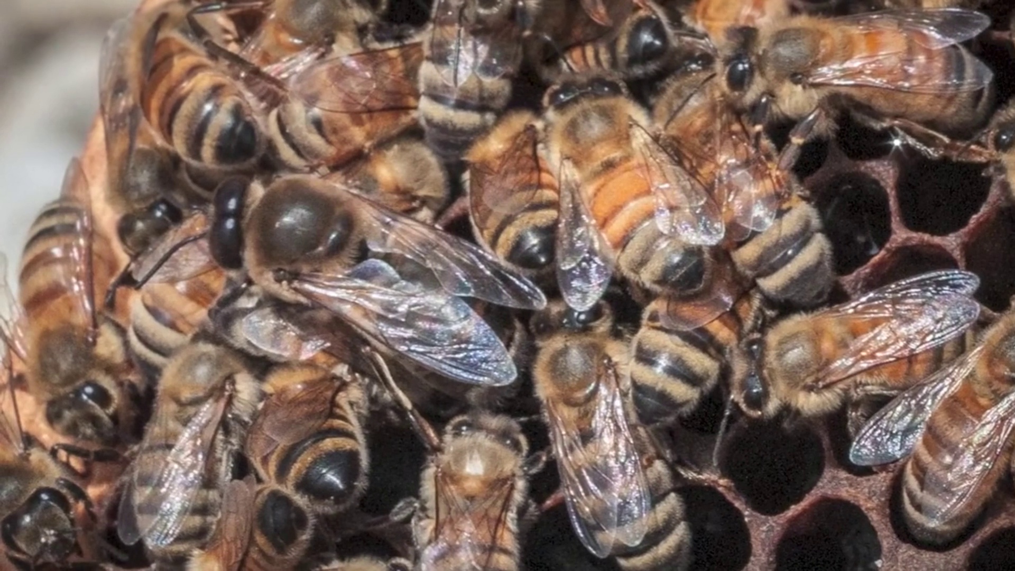
assets/video_sources/proxy/SHOT-007_last.jpg
