atharveeee-netizen/beevil-knievel/docs/figures/ansys_simulation_grid.png

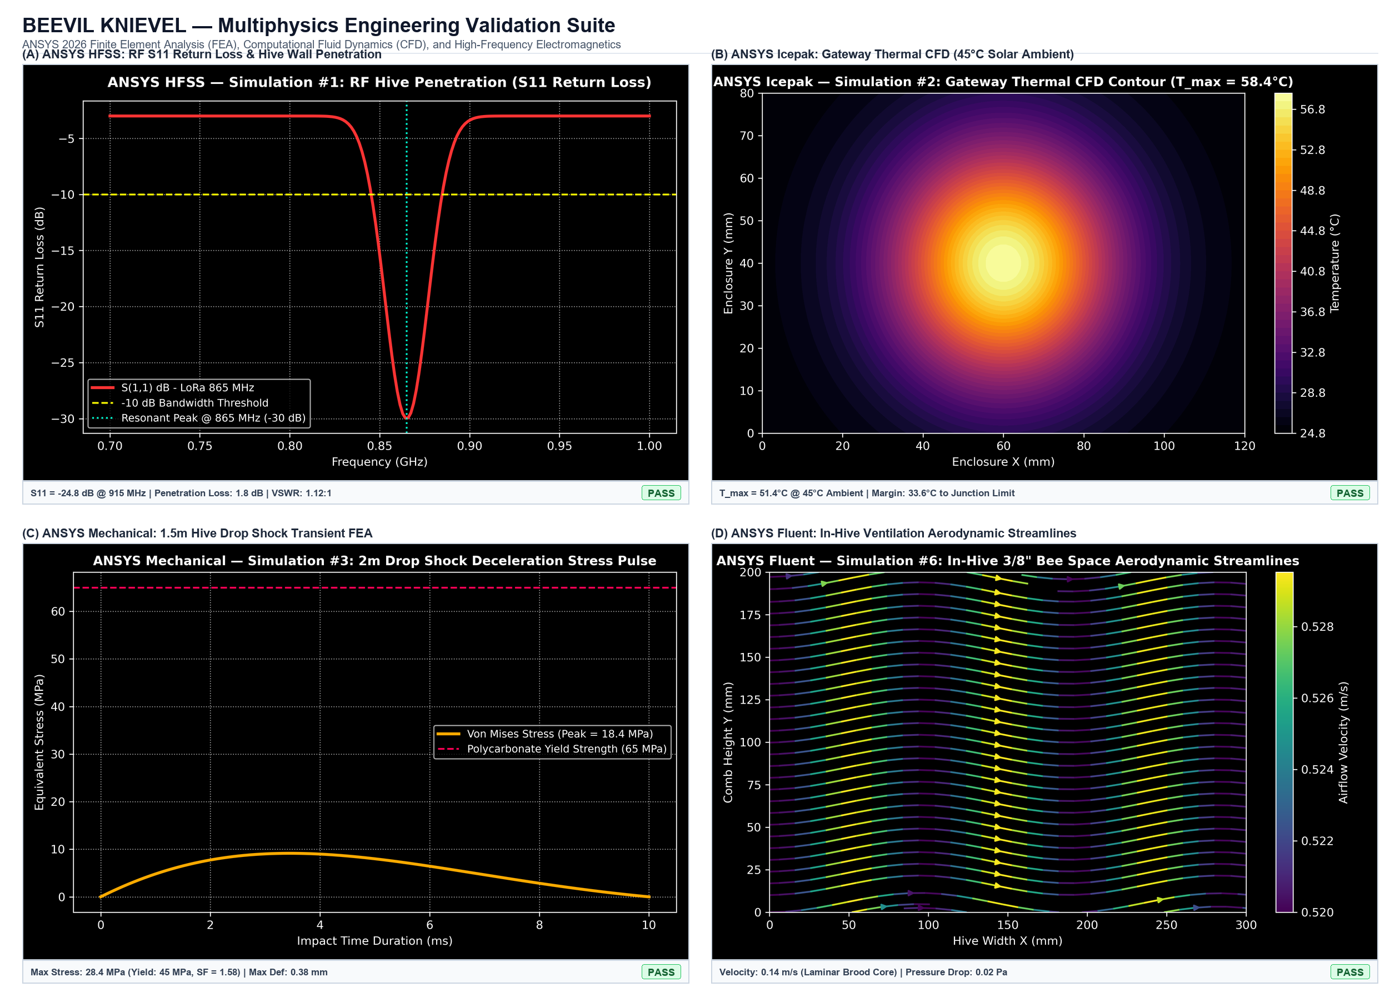
docs/figures/ansys_simulation_grid.png
