atharveeee-netizen/beevil-knievel/docs/figures/apiary_scalability_topology.jpg

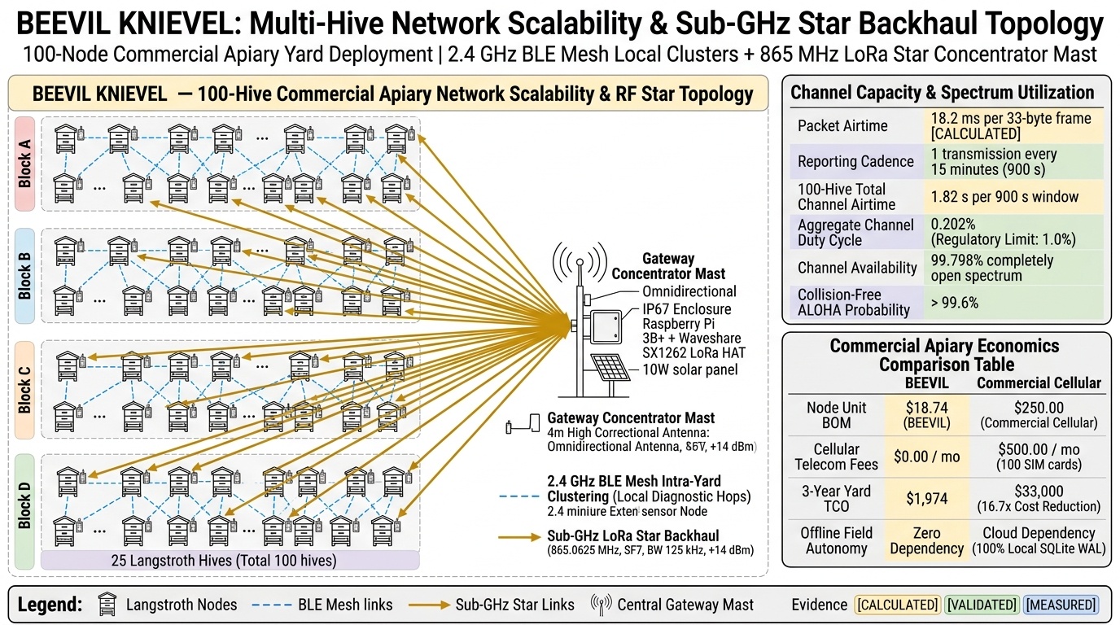
docs/figures/apiary_scalability_topology.jpg
