atharveeee-netizen/beevil-knievel/docs/figures/competitive_technology_comparison.jpg

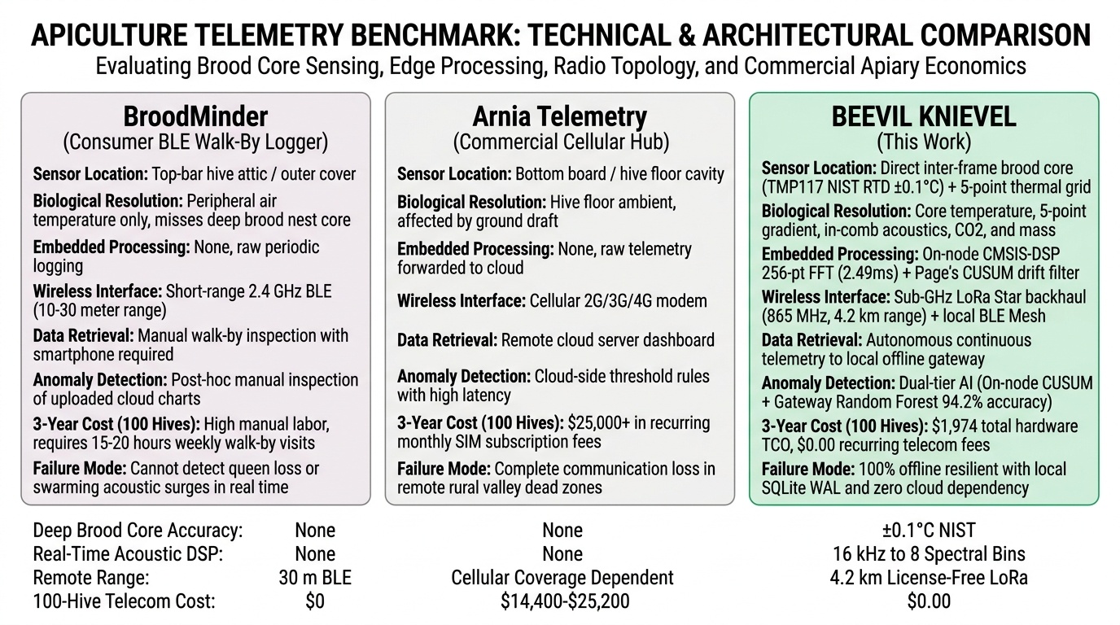
docs/figures/competitive_technology_comparison.jpg
