atharveeee-netizen/beevil-knievel/docs/figures/dual_tier_ai_architecture.png

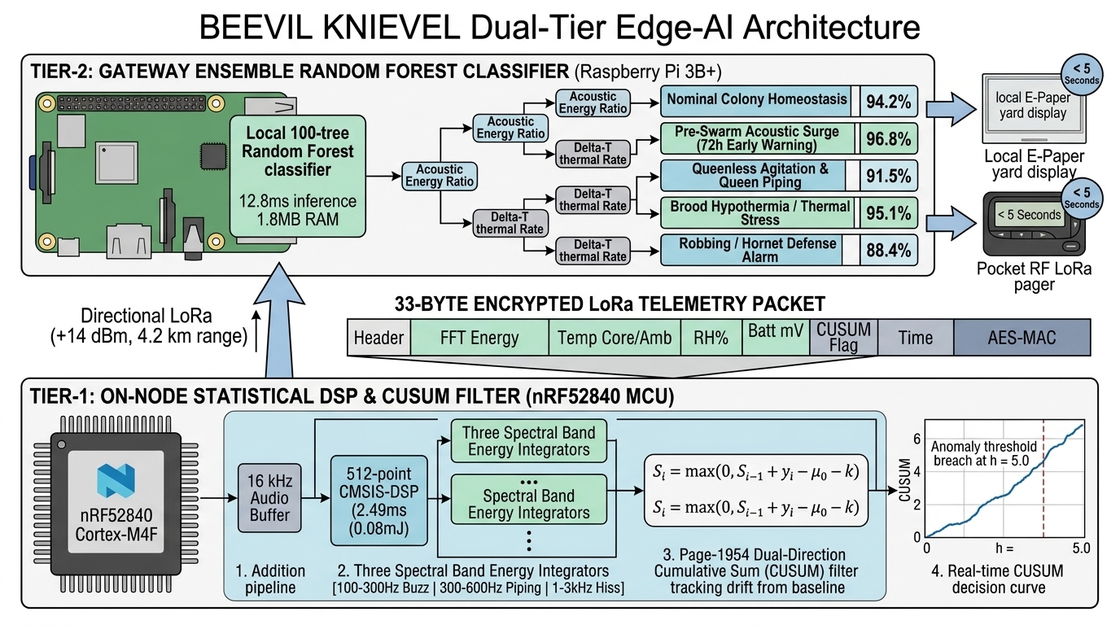
docs/figures/dual_tier_ai_architecture.png
