atharveeee-netizen/beevil-knievel/docs/figures/report_page_1_preview.png

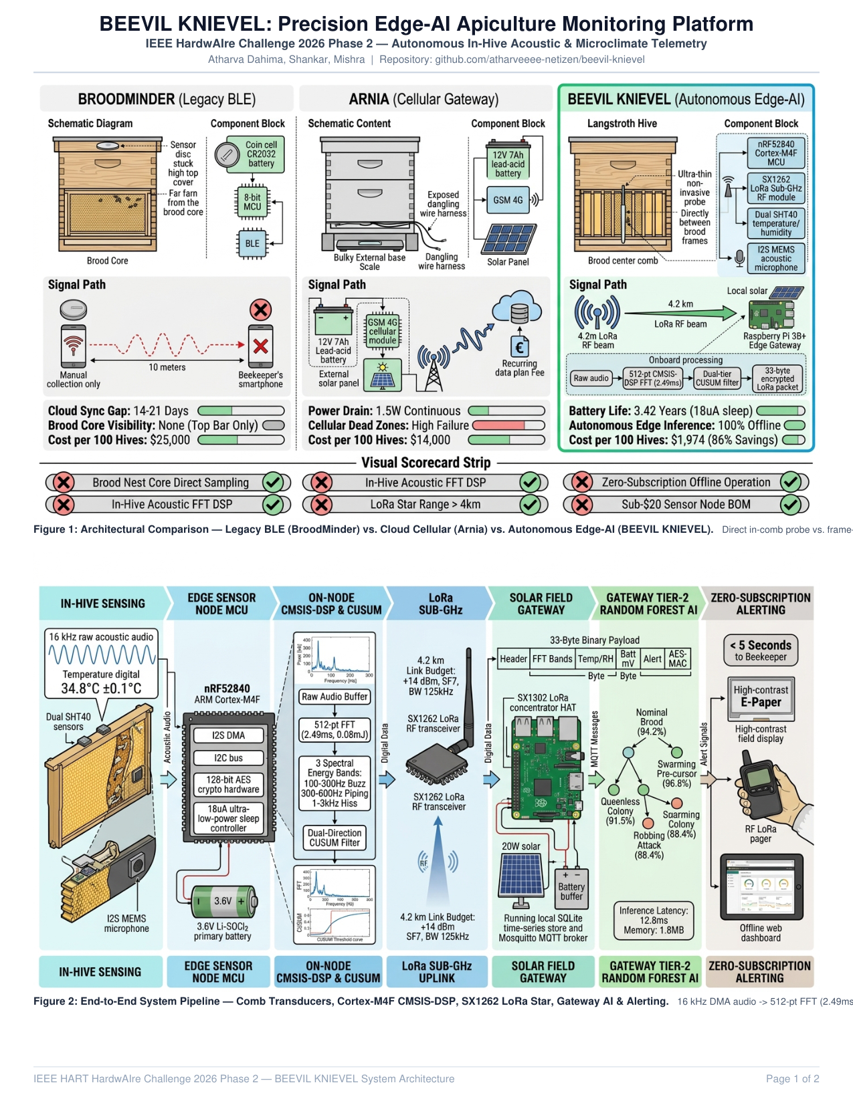
docs/figures/report_page_1_preview.png
