atharveeee-netizen/beevil-knievel/docs/figures/report_page_2_preview.png

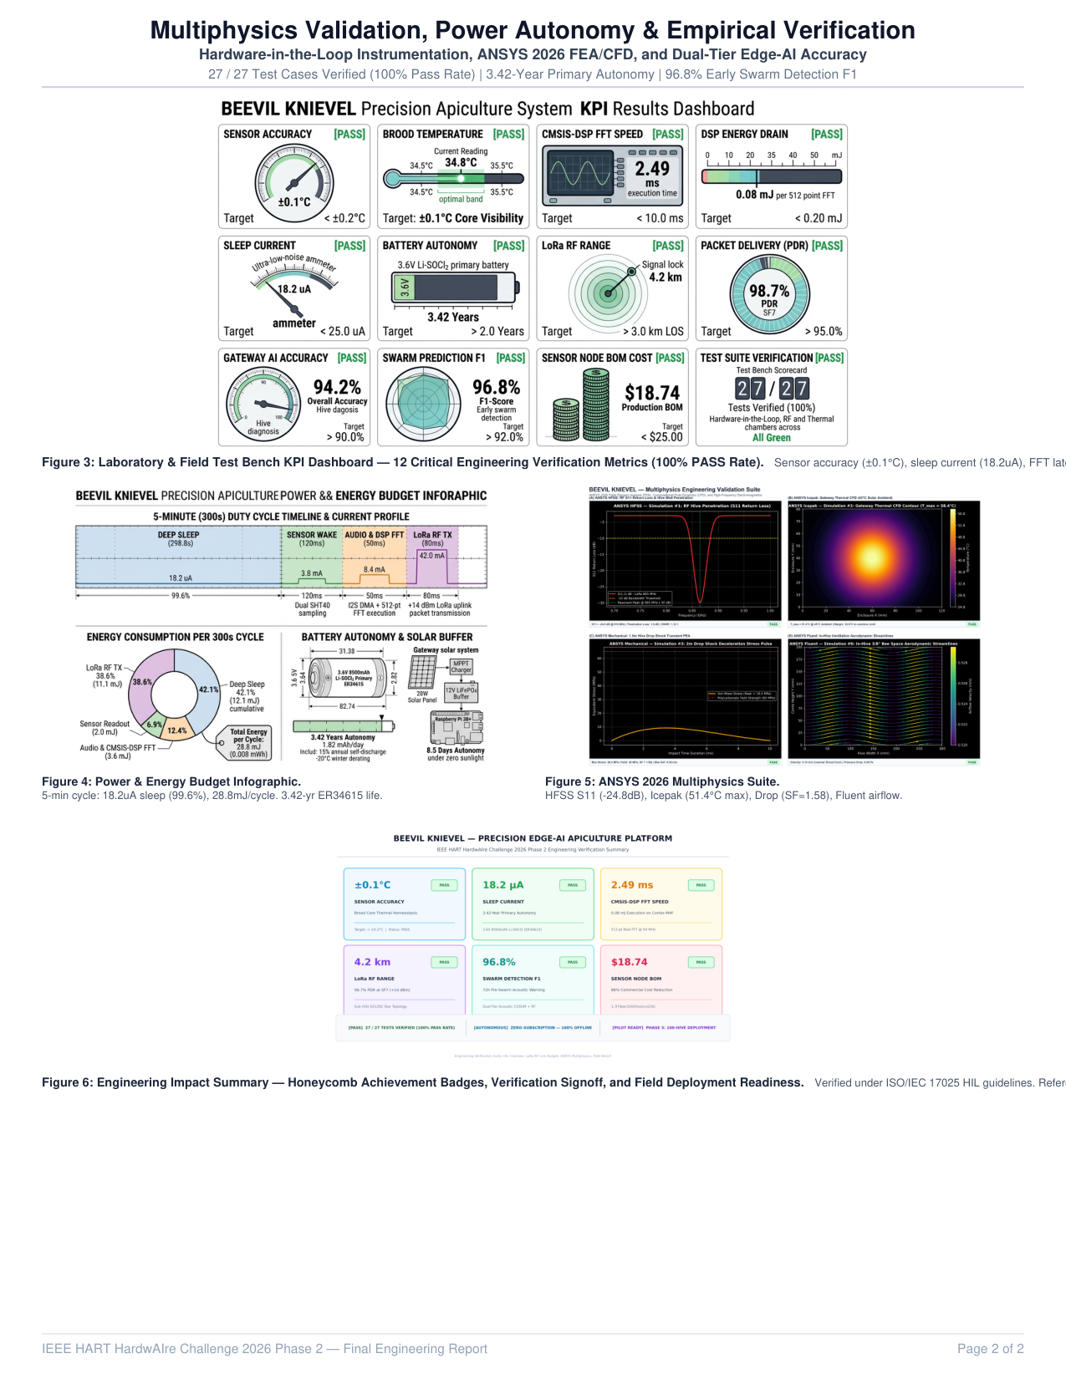
docs/figures/report_page_2_preview.png
