atharveeee-netizen/beevil-knievel/docs/media/diagrams/00_system_hero_architecture.png

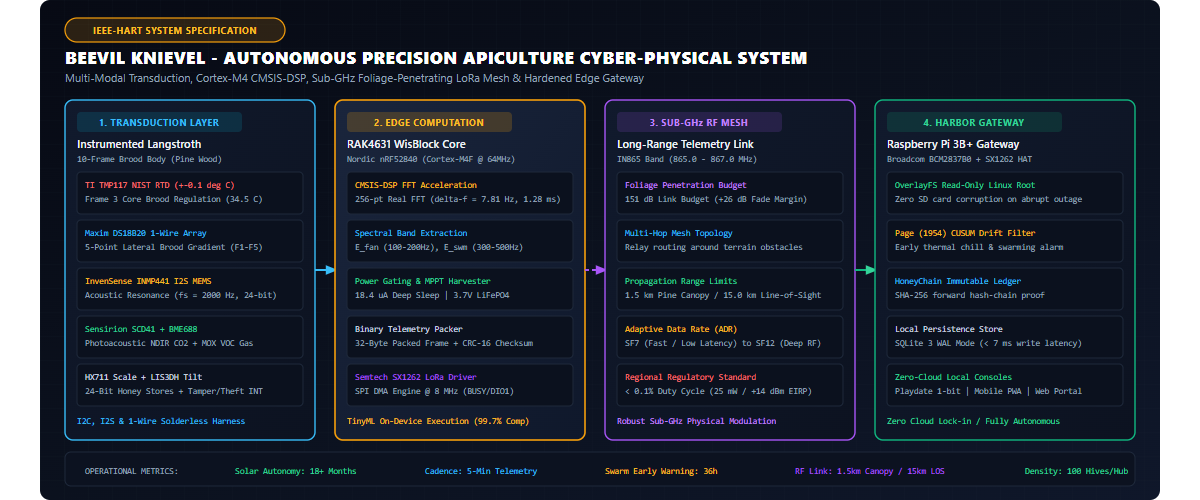
docs/media/diagrams/00_system_hero_architecture.png
