atharveeee-netizen/beevil-knievel/docs/media/diagrams/04_field_node_architecture.png

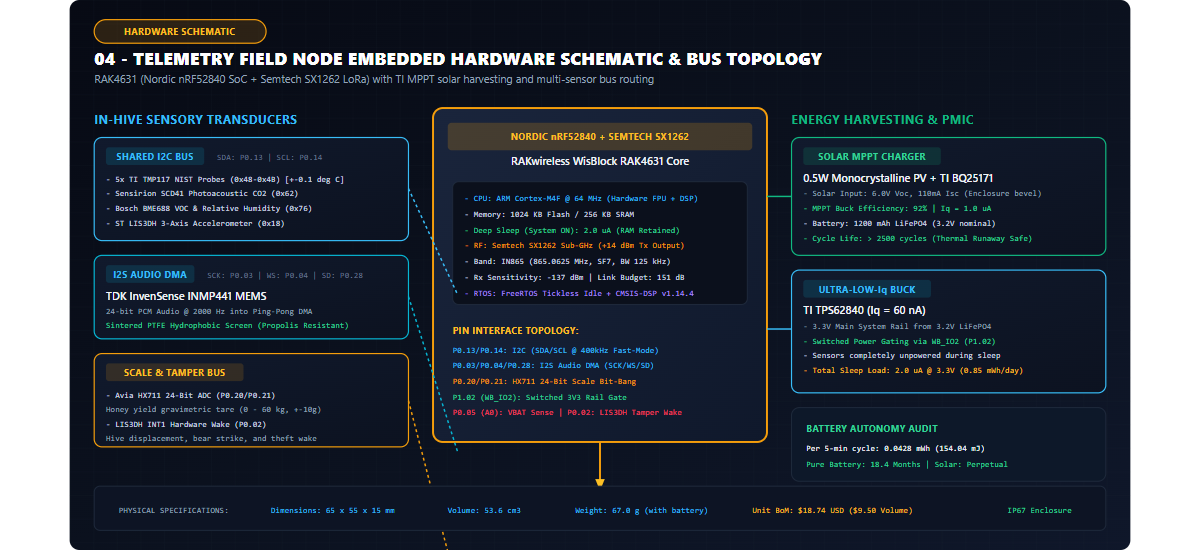
docs/media/diagrams/04_field_node_architecture.png
