atharveeee-netizen/beevil-knievel/docs/media/research/brood/real_capped_worker_brood.jpg

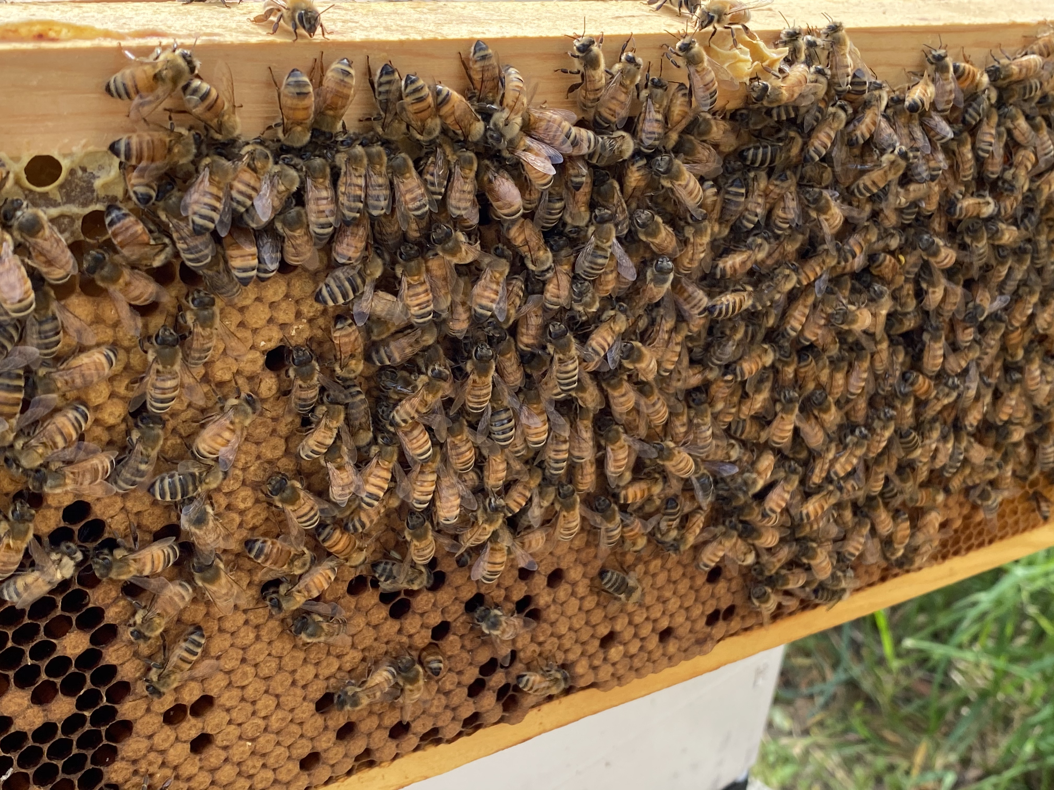
docs/media/research/brood/real_capped_worker_brood.jpg
