atharveeee-netizen/beevil-knievel/docs/media/research/hive/real_langstroth_hive_inspection.jpg

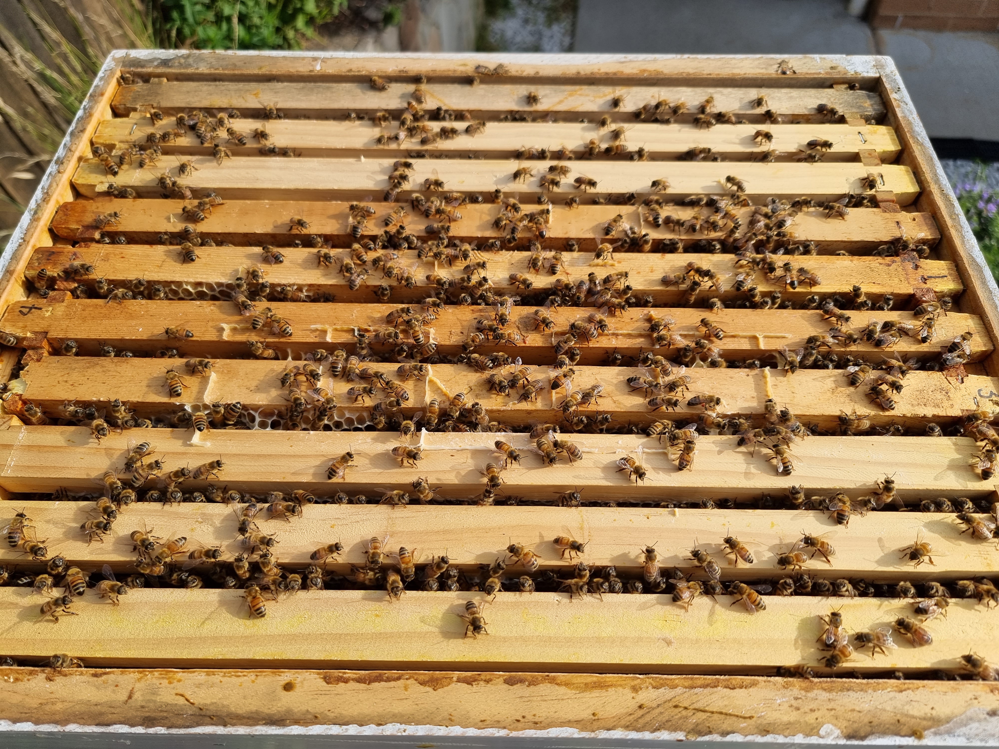
docs/media/research/hive/real_langstroth_hive_inspection.jpg
