atharveeee-netizen/beevil-knievel/docs/media/research/screenshots/nordic_nrf52840_datasheet_reference.png

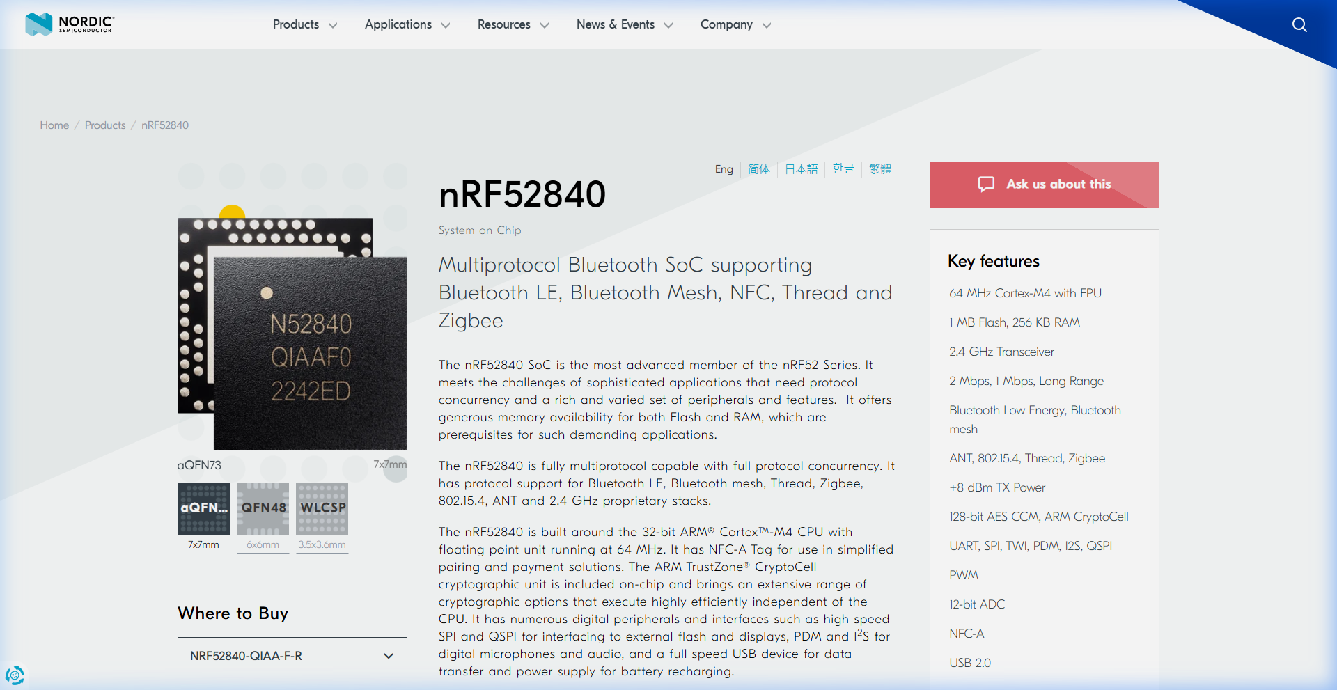
docs/media/research/screenshots/nordic_nrf52840_datasheet_reference.png
