atharveeee-netizen/beevil-knievel/docs/media/research/screenshots/zenodo_dataset_reference.png

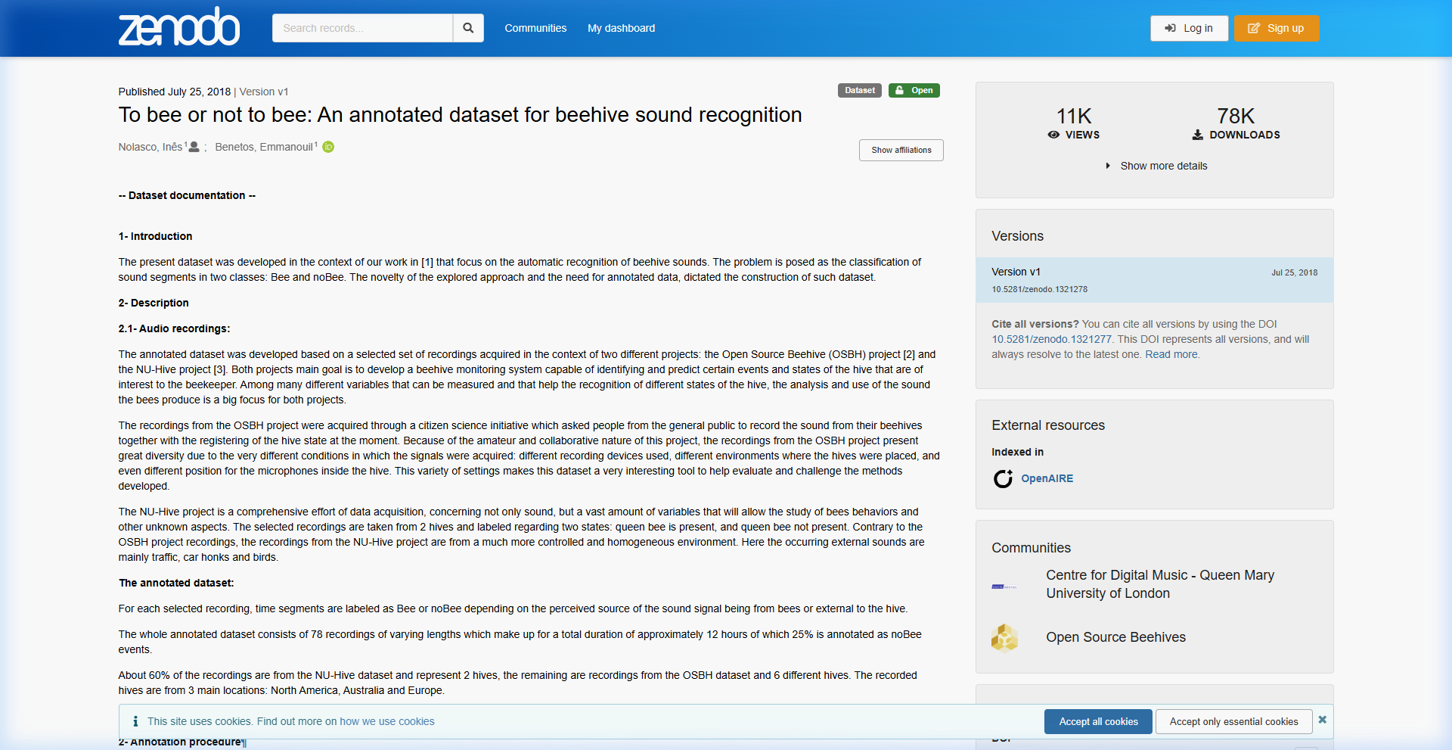
docs/media/research/screenshots/zenodo_dataset_reference.png
