atharveeee-netizen/beevil-knievel/docs/media/results/acoustic_spectrogram.png

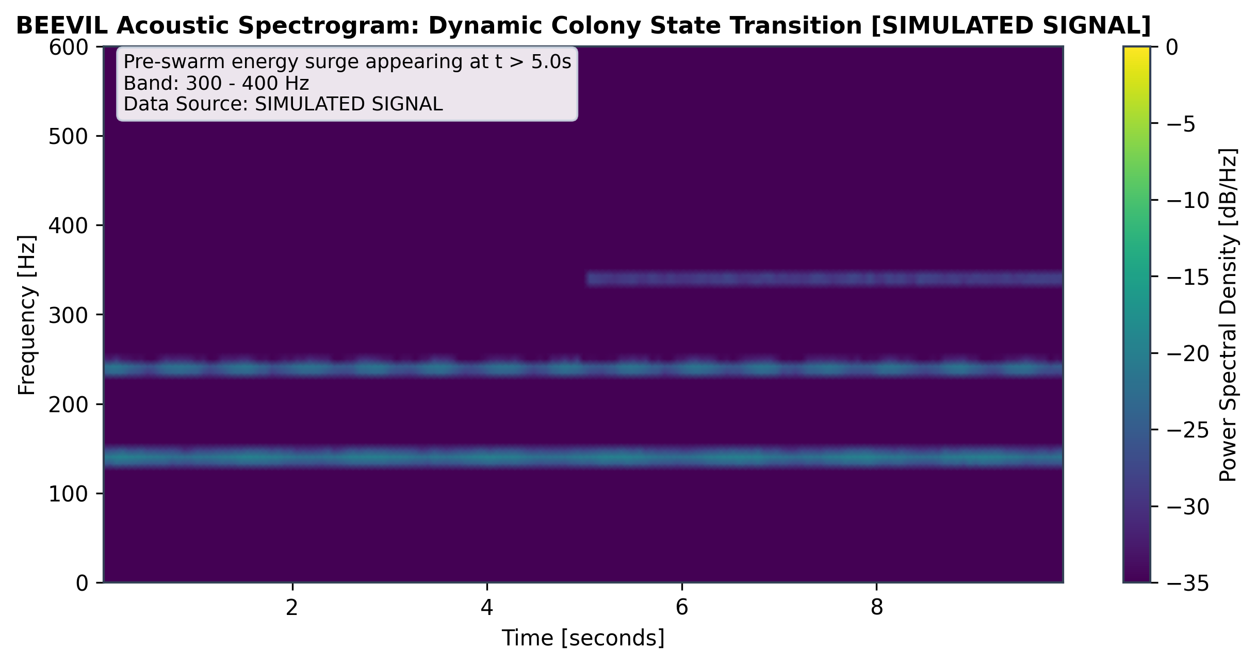
docs/media/results/acoustic_spectrogram.png
