atharveeee-netizen/beevil-knievel/docs/media/sensing/acoustic_transduction_concept.jpg

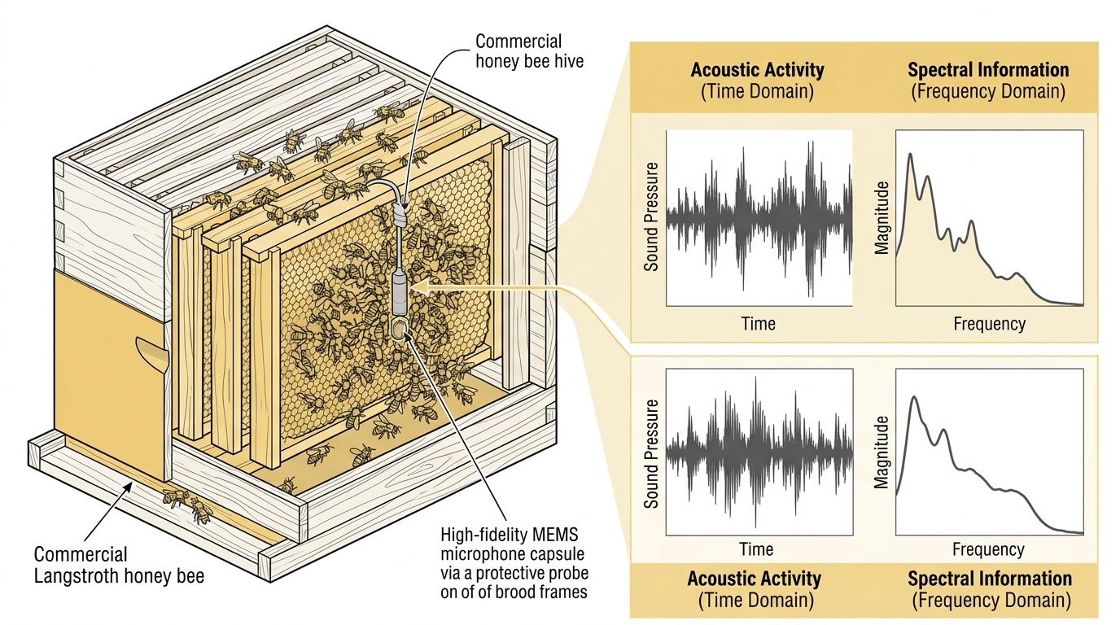
docs/media/sensing/acoustic_transduction_concept.jpg
