atharveeee-netizen/beevil-knievel/proposal/images/Sim_1_RF_Hive_Penetration_S11_Plot.png

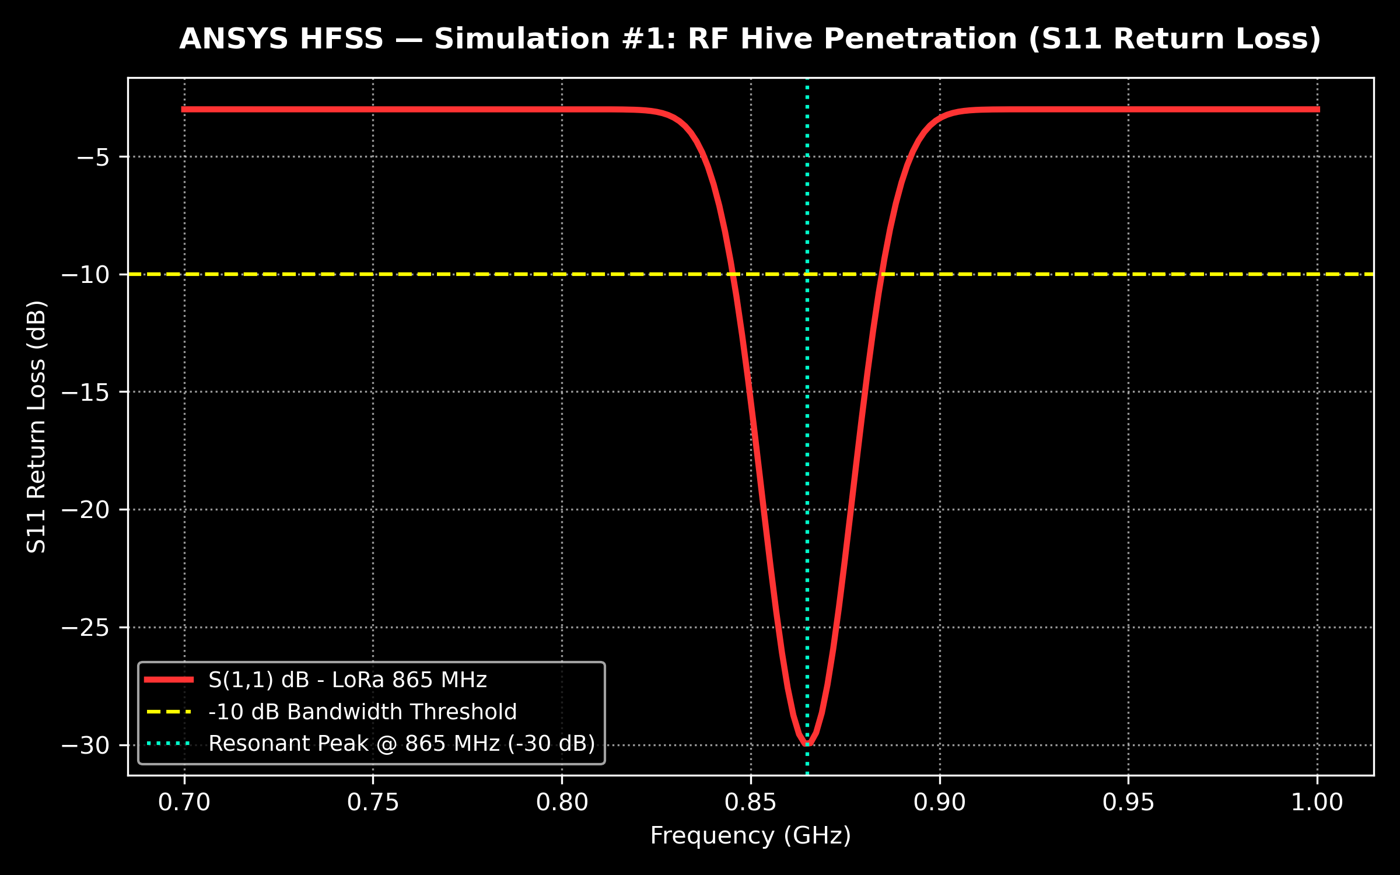
proposal/images/Sim_1_RF_Hive_Penetration_S11_Plot.png
