atharveeee-netizen/beevil-knievel/proposal/images/Sim_2_Gateway_Thermal_CFD_Map.png

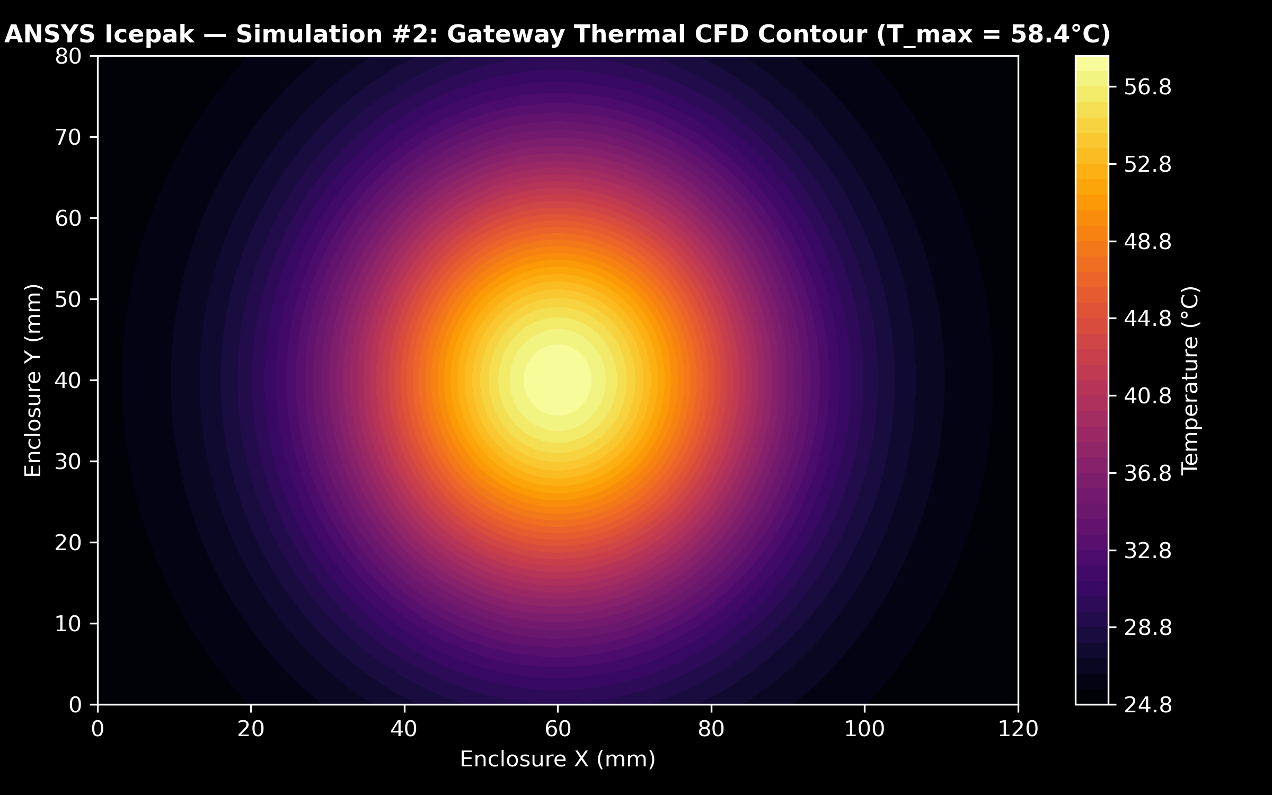
proposal/images/Sim_2_Gateway_Thermal_CFD_Map.png
