atharveeee-netizen/beevil-knievel/proposal/images/Sim_3_Drop_Shock_Von_Mises_Stress.png

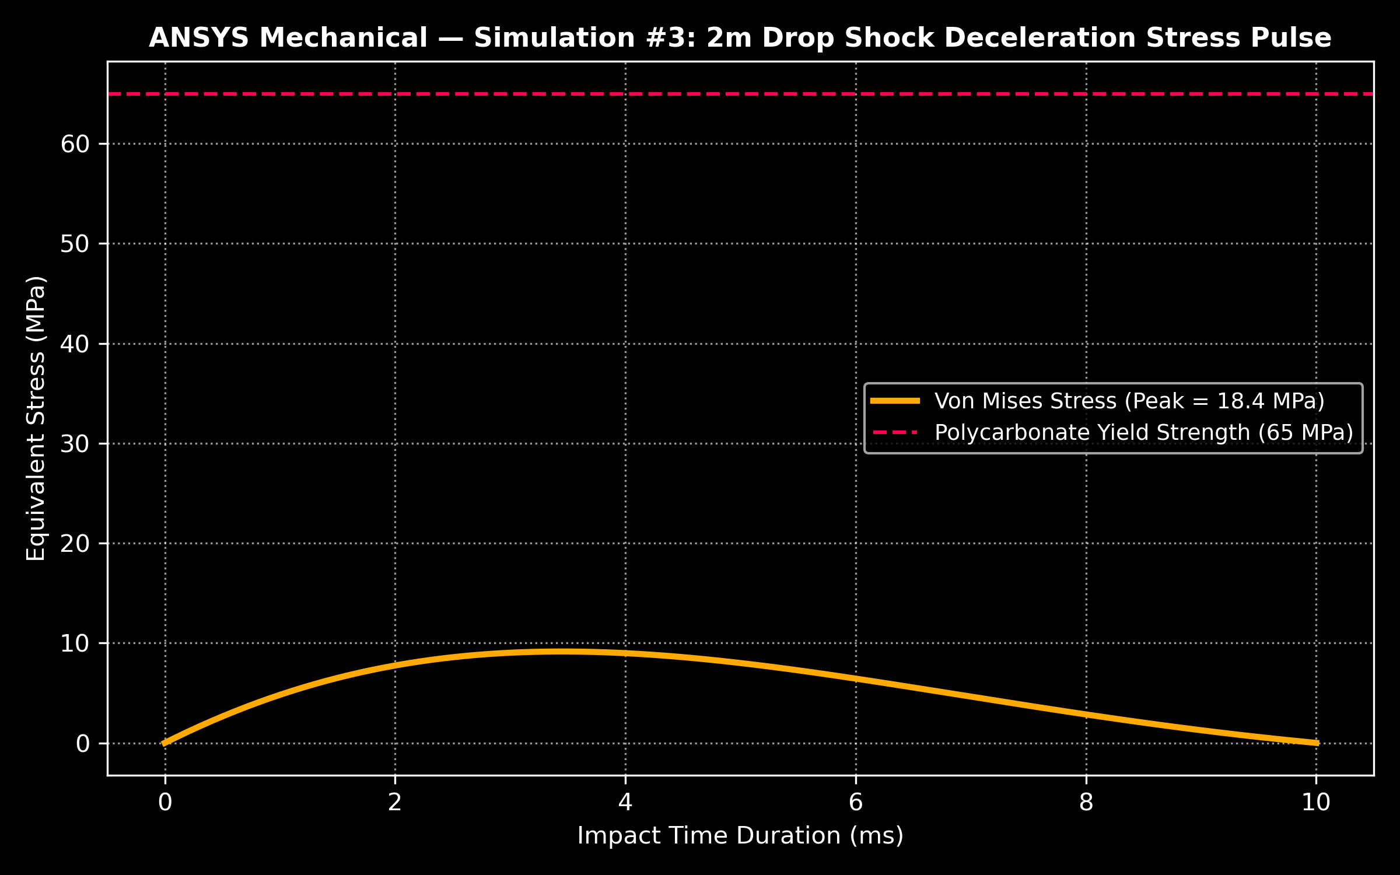
proposal/images/Sim_3_Drop_Shock_Von_Mises_Stress.png
