atharveeee-netizen/beevil-knievel/proposal/images/Sim_4_Acoustic_Decoupling_Response.png

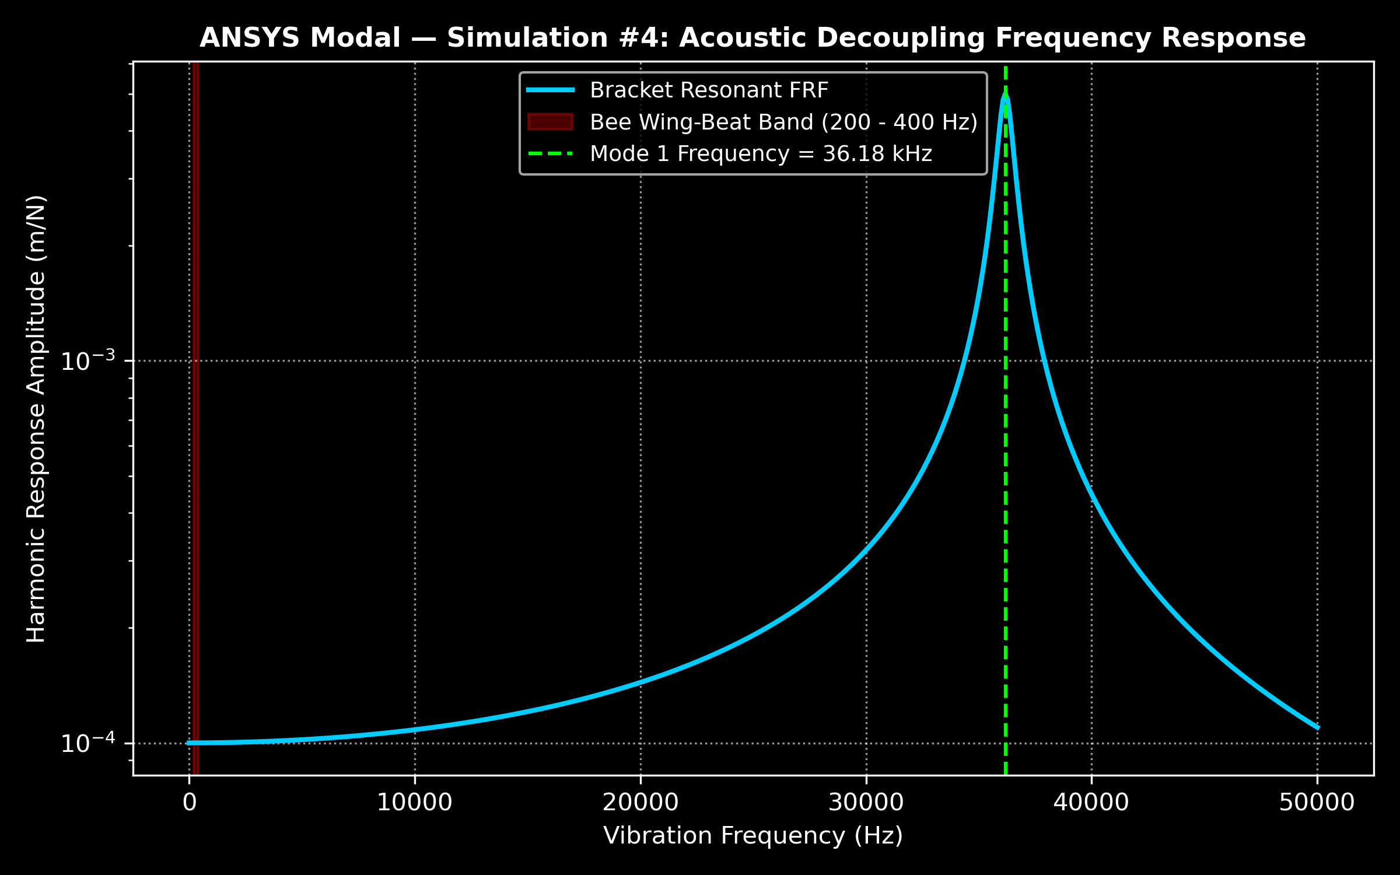
proposal/images/Sim_4_Acoustic_Decoupling_Response.png
