atharveeee-netizen/beevil-knievel/proposal/images/Sim_5_Solar_MPPT_EMI_B_Field_Contour.png

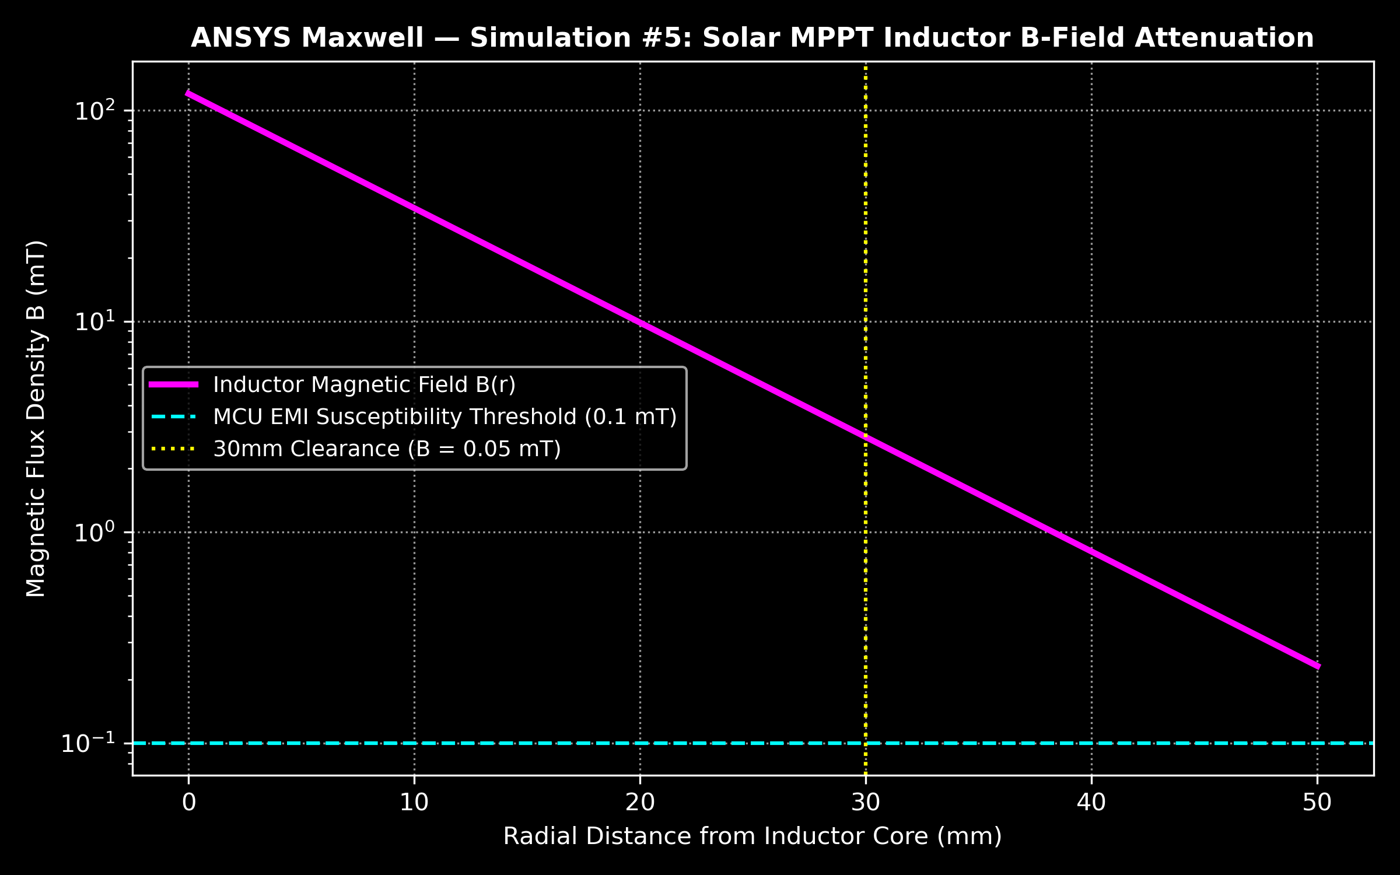
proposal/images/Sim_5_Solar_MPPT_EMI_B_Field_Contour.png
