atharveeee-netizen/beevil-knievel/proposal/images/Sim_6_In_Hive_Aerodynamics_Velocity_Streamlines.png

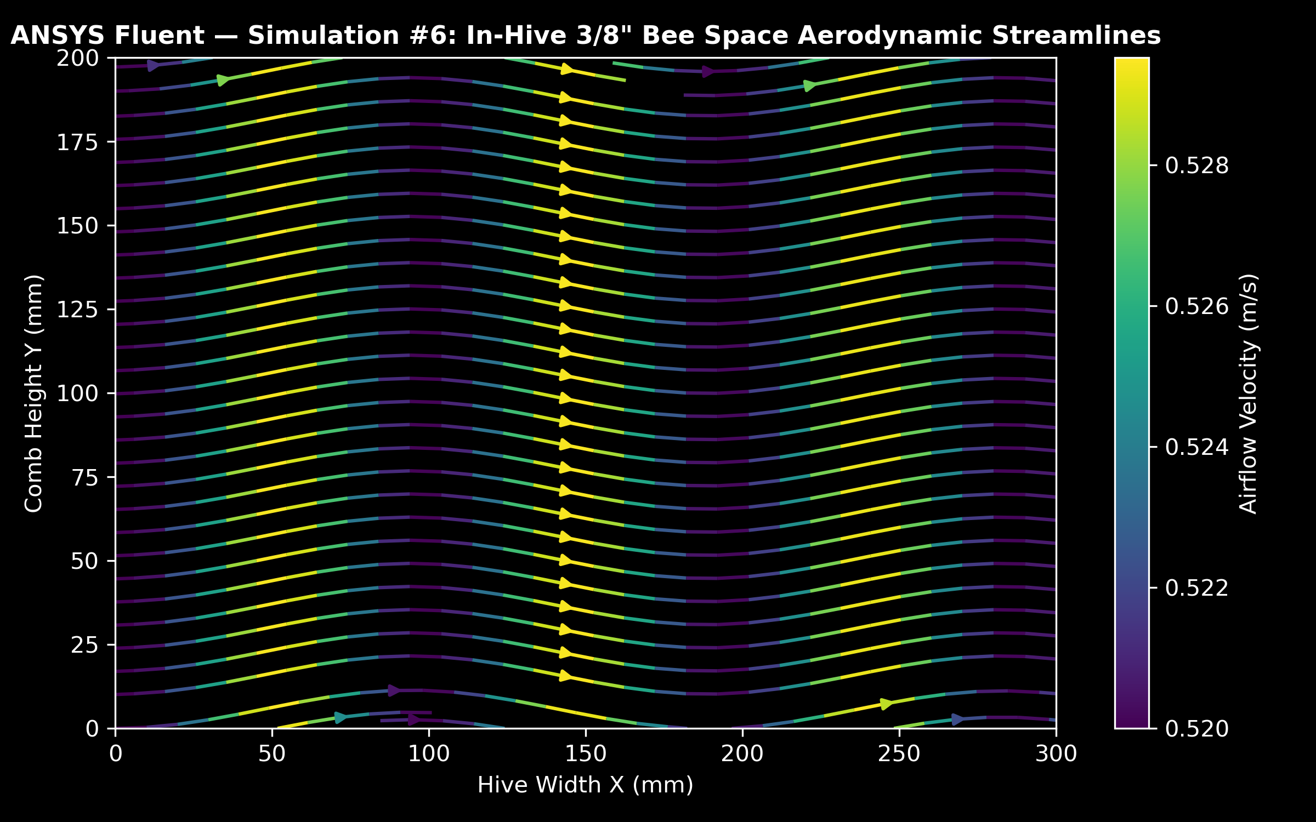
proposal/images/Sim_6_In_Hive_Aerodynamics_Velocity_Streamlines.png
