atharveeee-netizen/beevil-knievel/proposal/images/Sim_9_Bus_Signal_Integrity_Eye_Diagram.png

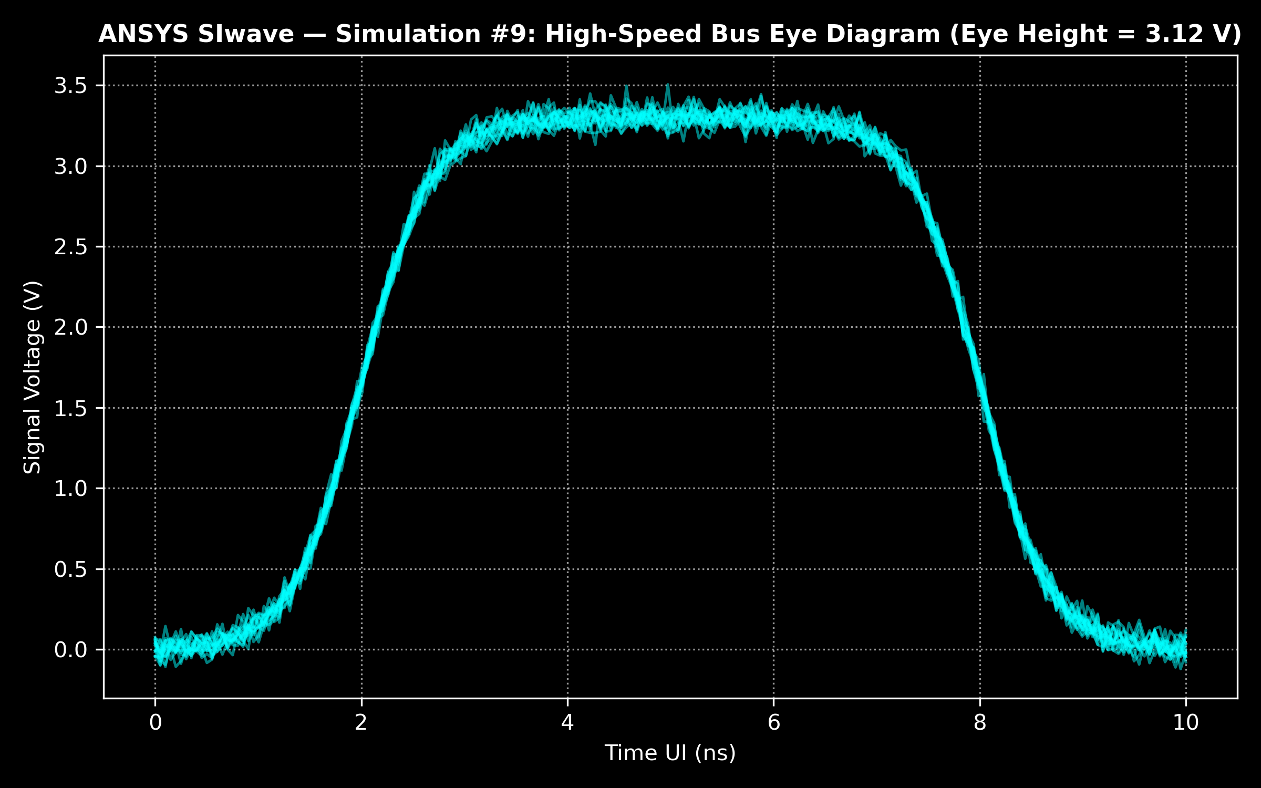
proposal/images/Sim_9_Bus_Signal_Integrity_Eye_Diagram.png
