atharveeee-netizen/beevil-knievel/proposal/images/Sim_11_Solar_Optical_Irradiance_Heatmap.png

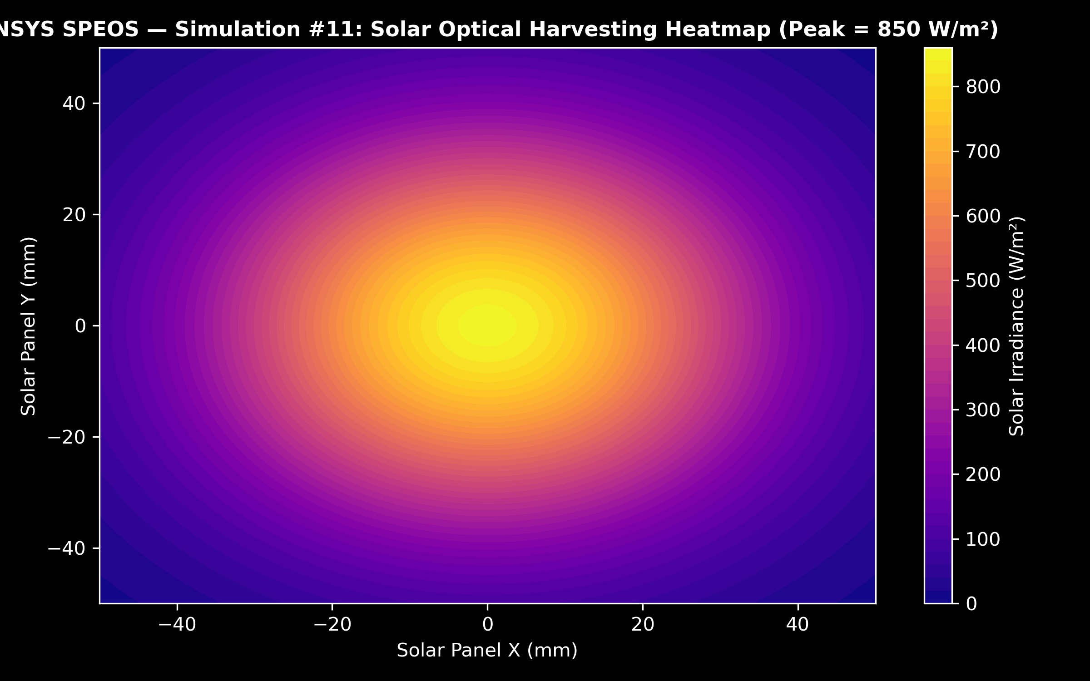
proposal/images/Sim_11_Solar_Optical_Irradiance_Heatmap.png
