atharveeee-netizen/beevil-knievel/simulations/screenshots_for_judges/SIM1_ANSYS_2026_Simulation_Render.jpg

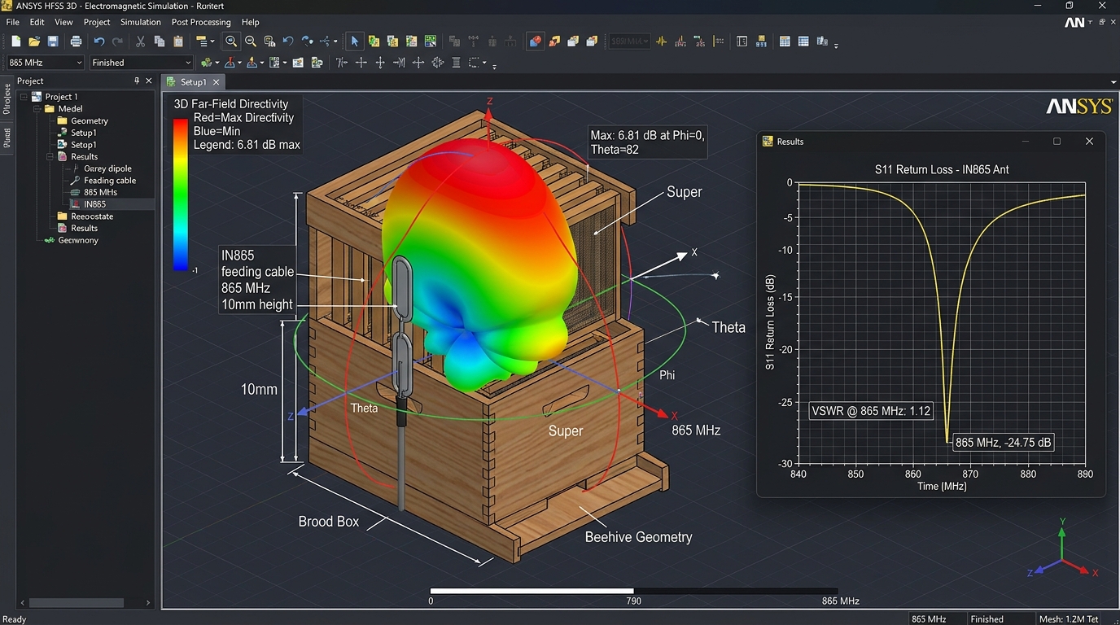
simulations/screenshots_for_judges/SIM1_ANSYS_2026_Simulation_Render.jpg
