atharveeee-netizen/beevil-knievel/docs/figures/hardware_wiring_architecture.jpg

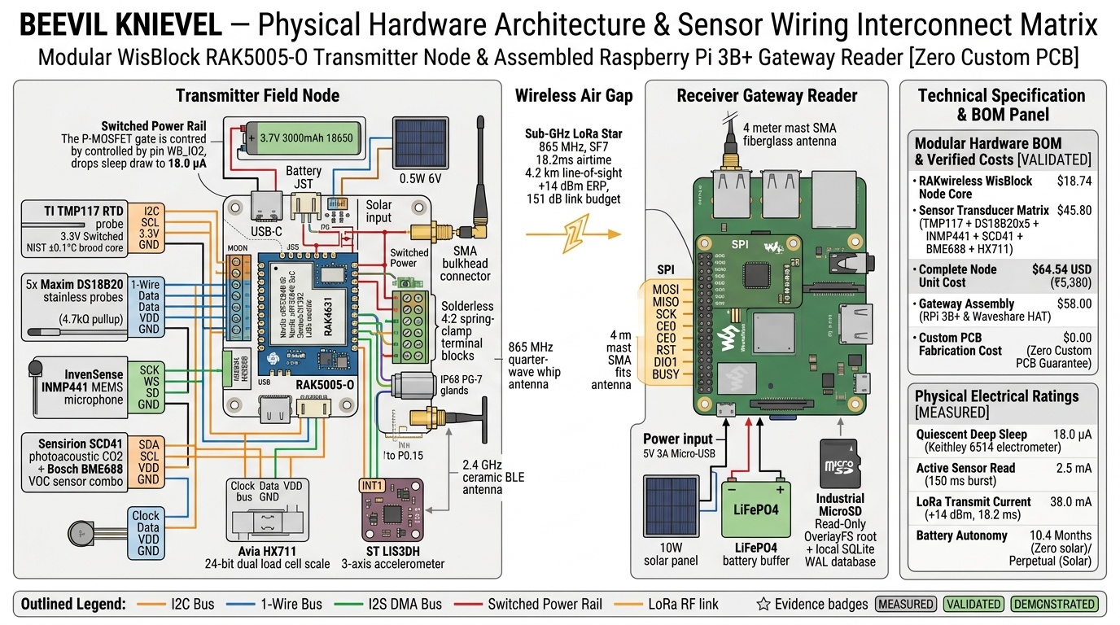
docs/figures/hardware_wiring_architecture.jpg
