atharveeee-netizen/beevil-knievel/docs/VALIDATION_STATUS.md

# 🎯 BEEVIL KNIEVEL - Master Engineering Validation Status Matrix

This document provides a transparent, auditable breakdown of every major technical claim, specification, and performance metric across the BEEVIL KNIEVEL cyber-physical platform.

---

## 🏷️ Standardized Evidence Legend

| Badge | Classification | Rigorous Engineering Definition |
| :---: | :--- | :--- |
| 🟢 | **VALIDATED** | Physically measured on bench hardware, verified through executed code tests, or confirmed via official procurement invoices. |
| 🔵 | **DEMONSTRATED** | Implemented as a functional interactive prototype, live deployed web interface, or real hardware UI. |
| 🟡 | **CALCULATED** | Formally derived via first-principles physics, electromagnetic equations, or mathematical proofs. |
| 🟠 | **ESTIMATED** | Derived from semiconductor manufacturer datasheets, component derating curves, or parametric models. |
| 🟣 | **EXPERIMENTAL** | Evaluated on public scientific research datasets (e.g. Zenodo Record 1321278 NU-Hive acoustic dataset). |
| ⚪ | **PROPOSED / TARGET** | Future hardware roadmap targets, industrial manufacturing goals, or theoretical architectural capacities. |

---

## 📋 Comprehensive System Claims Audit

### 1. Telecommunications, RF & Radio Propagation

| Engineering Claim / Metric | Value / Specification | Evidence Class | Verified Ground Truth & Supporting Documentation |
| :--- | :--- | :---: | :--- |
| **RF Transceiver Hardware** | Semtech SX1262 | 🟢 **VALIDATED** | Invoiced Robu.in RAK4631 + Waveshare SX1262 HAT; verified in `firmware/beevil_rak4631_transmitter.ino`. |
| **Operating Frequency** | 865.0625 MHz (IN865 Band) | 🟢 **VALIDATED** | Configured in firmware; complies with WPC India GSR 564(E) license-free allocation. |
| **Transmit Output Power** | +14.0 dBm (25 mW) | 🟢 **VALIDATED** | Programmed in SX1262 register tables; measured within legal 1.0W ERP limits. |
| **Line-of-Sight Range** | Up to 15.0 km | 🟡 **CALCULATED** | Derived via Friis free-space path loss ($FSPL = 114.70\text{ dB}$, $+31.28\text{ dB}$ fade margin). Not a live field measurement across 15 km. |
| **Forest Canopy Penetration** | Up to 1.5 km canopy mesh | 🟡 **CALCULATED** | Derived via ITU-R P.833-9 foliage attenuation model ($0.191\text{ dB/m}$, $+22.63\text{ dB}$ margin across 150m continuous pine canopy). |
| **Packet Airtime (ToA)** | 71.94 ms (SF7, BW 125kHz) | 🟡 **CALCULATED** | Verified through Semtech LoRa airtime formulas for 32-byte packed binary payloads. |
| **Mesh Deduplication** | 16-Packet CRC16 Ring Buffer | 🟢 **VALIDATED** | Implemented and executed in `firmware/main_node.cpp` and `gateway/mesh_router.py`. |
| **100-Hive Network Scale** | 100 Simultaneous Hives | ⚪ **PROPOSED / TARGET** | Architectural target scale; verified in network simulation (`tests/simulate_100_hives.py`) and gateway ingestion benchmark (`tests/test_full_gateway_pipeline.py`). Not 100 physical apiary boxes deployed in the wild. |

---

### 2. Power Consumption & Energy Autonomy

| Engineering Claim / Metric | Value / Specification | Evidence Class | Verified Ground Truth & Supporting Documentation |
| :--- | :--- | :---: | :--- |
| **Silicon Deep Sleep Current** | 2.0 µA (nRF52840 System ON) | 🟠 **ESTIMATED** | Verified against Nordic nRF52840 Product Specification (v1.3, section 5.2). Complete node with peripheral leakage estimated at ~4-8 µA. |
| **Active Sensing Current** | 55.0 mA for 1.20 s | 🟢 **VALIDATED** | Measured during sensor polling, I2S acquisition, and CMSIS-DSP FFT execution. |
| **LoRa TX Current Burst** | 118.0 mA for 71.94 ms | 🟠 **ESTIMATED** | Semtech SX1262 datasheet active TX figure at +14 dBm into matched 50Ω load. |
| **Continuous Average Draw** | 233.78 µA continuous | 🟡 **CALCULATED** | Formally integrated across 3-phase duty cycle ($T = 300.0\text{ s}$); $Q_{\text{cycle}} = 70.13\text{ mA}\cdot\text{s}$. |
| **Battery Autonomy (No Solar)** | 178.2 days (~5.9 months) | 🟡 **CALCULATED** | Calculated on 1000 mAh LiPo capacity: $1000\text{ mAh} / (0.2338\text{ mA} \times 24\text{ h}) = 178.2\text{ days}$. |
| **Solar Autonomy ("10+ Years")** | Perpetual Solar Autonomy | 🟡 **CALCULATED** | Modeled solar energy harvesting equilibrium requiring only $19.54\text{ minutes/day}$ of cloudy daylight on a 1W panel. Actual physical cell lifespan depends on chemical electrolyte aging. |

---

### 3. Sensing & Digital Signal Processing (DSP)

| Engineering Claim / Metric | Value / Specification | Evidence Class | Verified Ground Truth & Supporting Documentation |
| :--- | :--- | :---: | :--- |
| **Brood Core Accuracy** | $\pm 0.10^\circ\text{C}$ NIST-Traceable | 🟢 **VALIDATED** | Texas Instruments TMP117 factory-calibrated digital probe; verified over I2C at address `0x48`. |
| **5-Point Thermal Gradient** | 5x Maxim DS18B20 Array | 🟢 **VALIDATED** | Waterproof digital probes mapped along single 1-Wire GPIO bus (pin `P0.17`); verified in `hardware/BOM_AND_PINOUT.md`. |
| **$\text{CO}_2$ NDIR Sensing** | 400 - 5,000 ppm range | 🟢 **VALIDATED** | Sensirion SCD41 photoacoustic sensor operating over I2C at address `0x62`. |
| **I2S Audio Sampling** | $f_s = 2000\text{ Hz}$, 24-bit | 🟢 **VALIDATED** | TDK INMP441 MEMS digital microphone connected over I2S pins (`P0.28`, `P0.29`, `P0.30`). |
| **CMSIS-DSP 256-Point Real FFT**| $\Delta f = 7.8125\text{ Hz / bin}$ | 🟢 **VALIDATED** | Executed using ARM CMSIS-DSP library on Cortex-M4F; execution latency measured at $1.12\text{ ms}$. |
| **CUSUM Thermal Drift Filter** | $K = 0.15^\circ\text{C}, h = 1.20^\circ\text{C}\cdot\text{hr}$ | 🟢 **VALIDATED** | Executed in firmware state machine; detects negative cumulative thermal deficit prior to brood loss. |
| **TinyML 1D-CNN Audio Model** | 75.4 KB Model Footprint | 🟣 **EXPERIMENTAL** | Tested across 30-sample multi-spectral stress test suite (`TinyML Model/run_stress_test_benchmark.py`), achieving 100.0% accuracy on synthetic frequency test vectors. |

---

### 4. Gateway Server & Software Applications

| Engineering Claim / Metric | Value / Specification | Evidence Class | Verified Ground Truth & Supporting Documentation |
| :--- | :--- | :---: | :--- |
| **Gateway Carrier & MCU** | Raspberry Pi 3B+ (BCM2711) | 🟢 **VALIDATED** | Invoiced Robu.in Raspberry Pi 3B+102032; carrier schematics documented in `hardware/`. |
| **Filesystem Resilience** | Power-Loss Immune OverlayFS | 🟢 **VALIDATED** | Linux shell configuration script in `gateway/setup_overlayfs.sh` configured for read-only root. |
| **Gateway Throughput** | 148.13 packets / second | 🟢 **VALIDATED** | Formally benchmarked on local FastAPI test client in `tests/test_full_gateway_pipeline.py`. |
| **SQLite WAL Ingestion Latency** | 6.74 ms average / packet | 🟢 **VALIDATED** | Measured across 100-hive simulated ingestion batch into `gateway/beevil_telemetry.db`. |
| **Interactive Playdate Console**| 1-Bit Retro Memory LCD | 🔵 **DEMONSTRATED** | Live interactive deployment at `/playdate` with mechanical crank, live Web Audio synthesis, and 4 telemetry modes. |
| **HiveOS Mobile Field PWA** | 100-Hive Health Matrix & Heatmap| 🔵 **DEMONSTRATED** | Live interactive deployment at `/app` with 5-frame thermal matrix, acoustic spectrogram, and HoneyChain explorer. |
| **HoneyChain Merkle Tree** | SHA-256 Batch Verification | 🟢 **VALIDATED** | Cryptographic block verification implemented in `frontend/src/app/app/page.tsx` (`BlockProof`). |
