atharveeee-netizen/beevil-knievel/Cloud Model/data/IEEE_Verified_Hive_Dataset.csv

label | temp_celcius | audio_peak_hz | co2_ppm | weight_kg
0 | 33.25029714256321 | 114.73216183125444 | 801.9242965315527 | 24.726108198305873
3 | 36.290942572590744 | 505.24650788616975 | 747.9827035366833 | 20.387935075780234
1 | 32.610427533236404 | 373.8891287301354 | 2419.406274007077 | 25.036813407117837
0 | 33.67730062652156 | 121.54955987327398 | 524.5460324344403 | 17.607265315006003
0 | 35.01128521600482 | 163.89618876297368 | 735.0839174617417 | 22.561832895225187
0 | 35.71987620316963 | 108.98586580619263 | 919.0727700715723 | 17.81873067535941
0 | 35.19213640925526 | 175.44522638000004 | 755.3935881135341 | 28.46961616595629
2 | 26.691727360157078 | 113.02430055694472 | 675.3616597485452 | 6.074884009639478
0 | 34.79737717083264 | 166.5689981303857 | 947.9564758858905 | 16.348686347578273
1 | 34.853415558780306 | 375.02523734584 | 2286.408031822323 | 31.669428727502865
0 | 34.87946429489338 | 129.09684544711274 | 568.5795172635651 | 37.48707563209927
3 | 34.281191423969375 | 579.1013283542363 | 683.9368880474506 | 25.230031933681705
2 | 25.31260331185563 | 157.81326790000668 | 651.5826048751263 | 4.038328609663033
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
