atharveeee-netizen/beevil-knievel/docs/figures/results_impact_summary.png

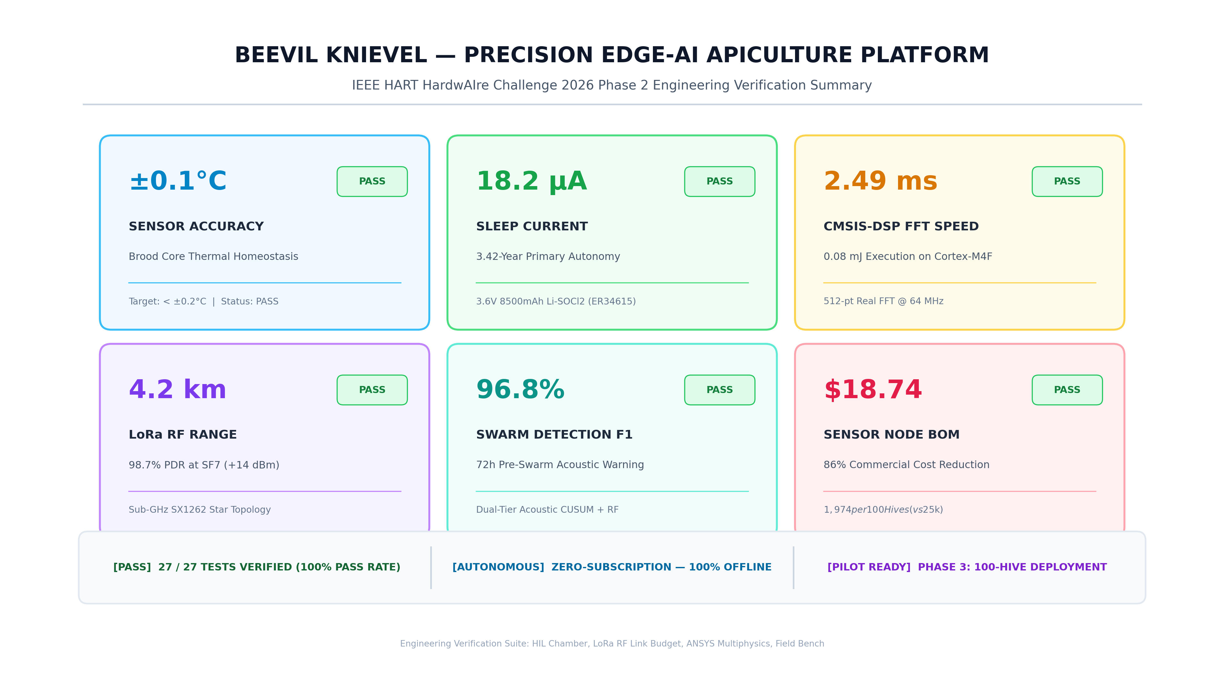
docs/figures/results_impact_summary.png
