atharveeee-netizen/beevil-knievel/docs/media/results/acoustic_event_simulation.png

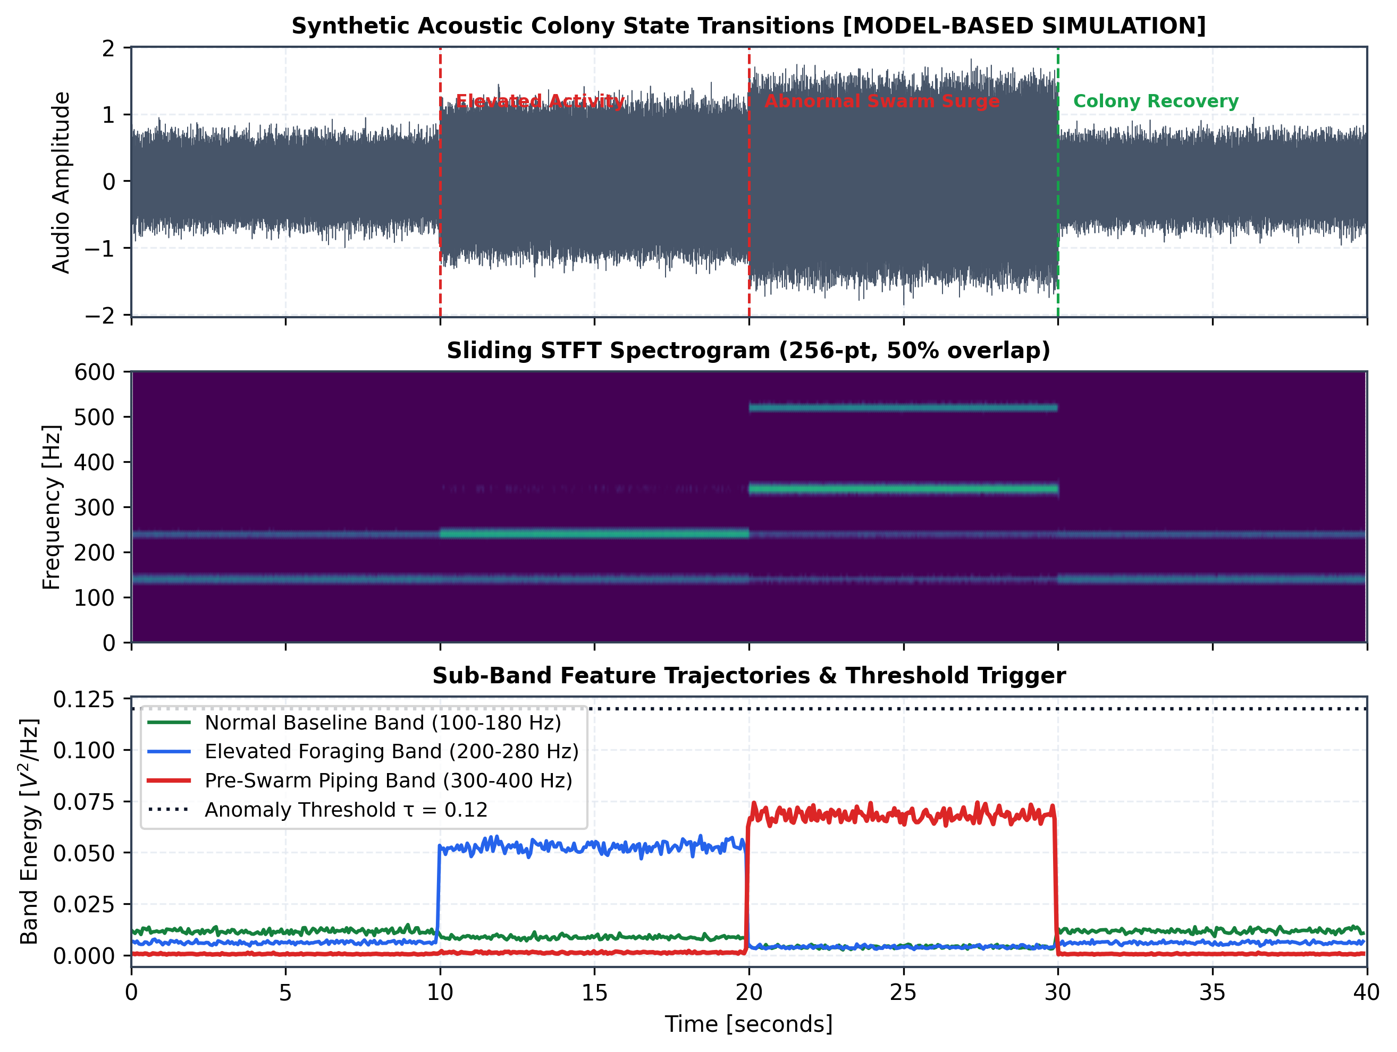
docs/media/results/acoustic_event_simulation.png
