atharveeee-netizen/beevil-knievel/docs/media/results/acoustic_features.png

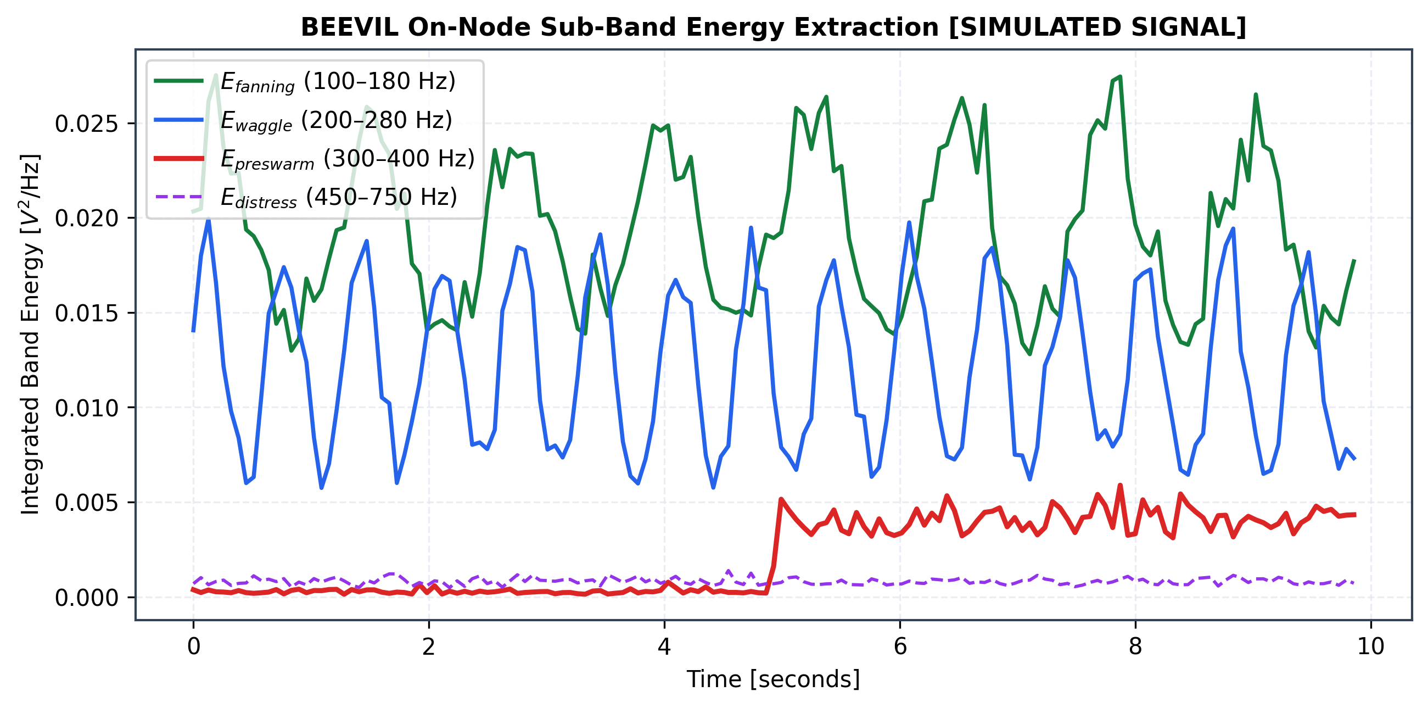
docs/media/results/acoustic_features.png
