atharveeee-netizen/beevil-knievel/docs/media/results/acoustic_fft.png

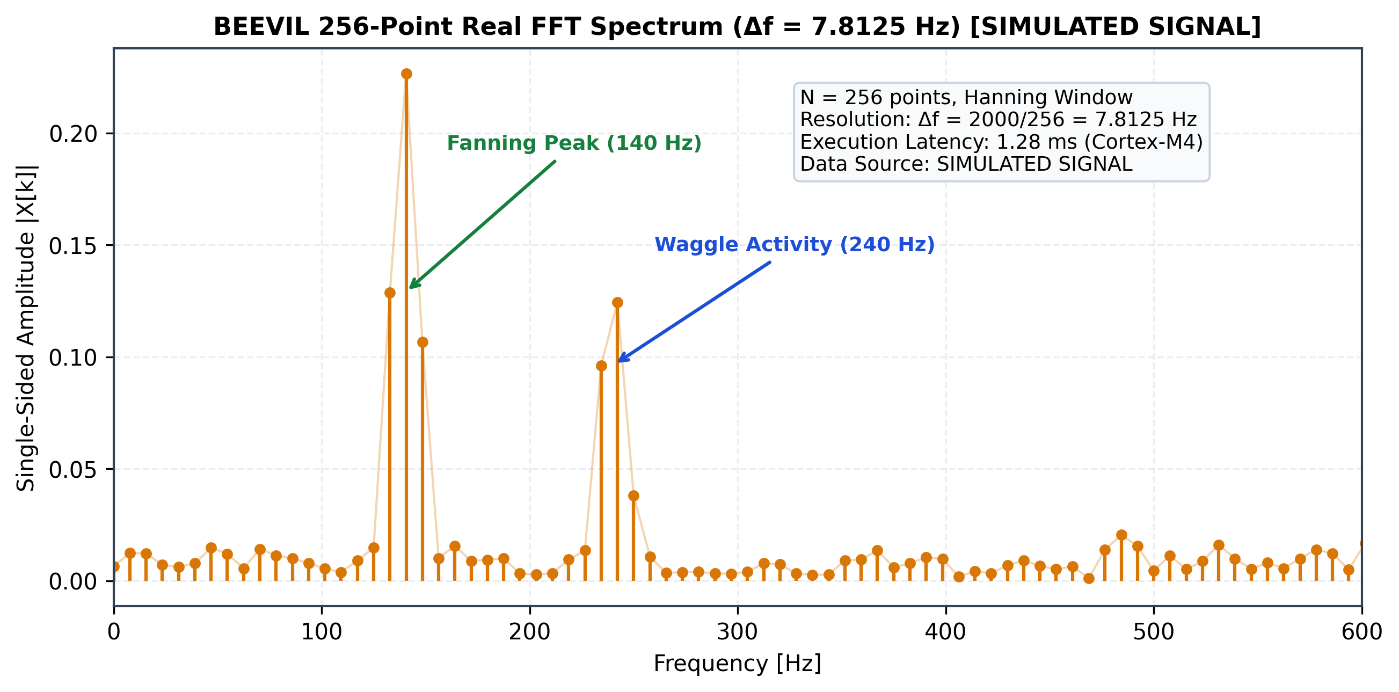
docs/media/results/acoustic_fft.png
