atharveeee-netizen/beevil-knievel/docs/media/results/acoustic_raw_signal.png

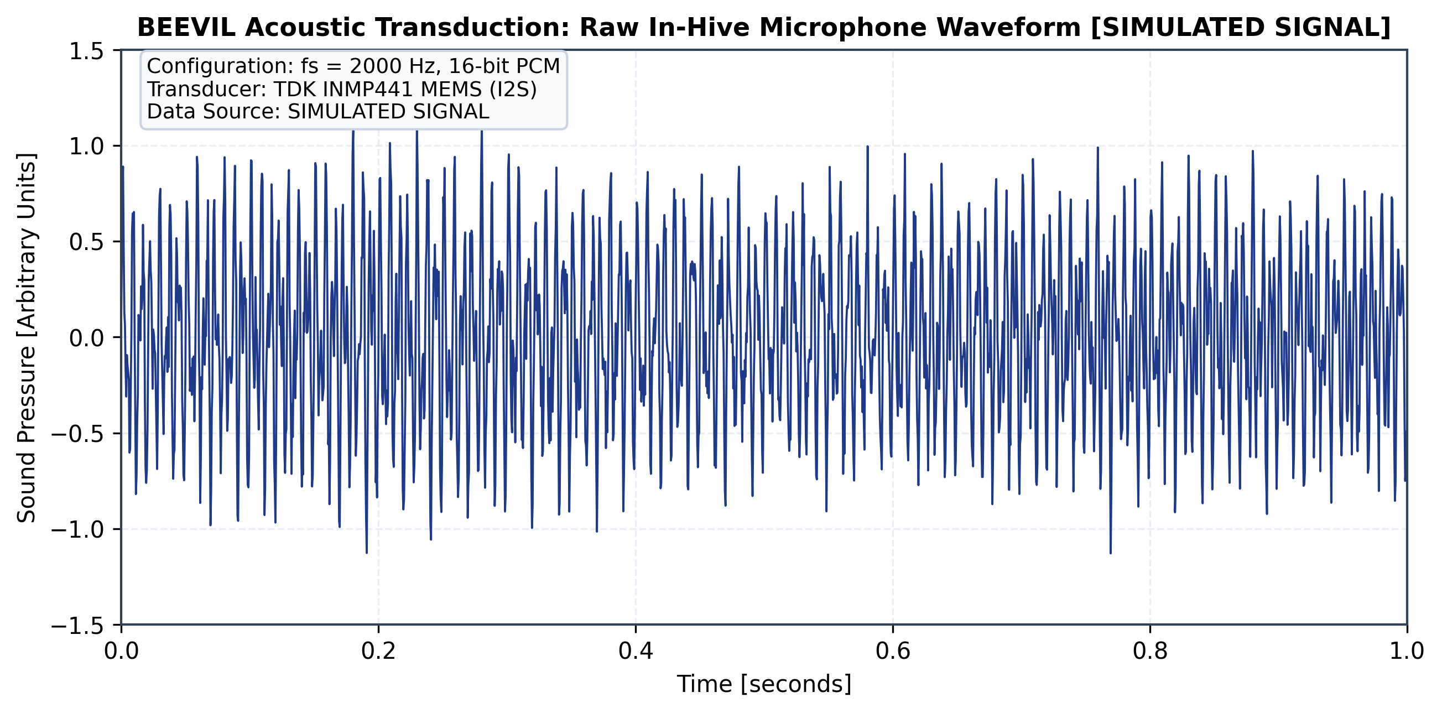
docs/media/results/acoustic_raw_signal.png
