atharveeee-netizen/beevil-knievel/docs/media/results/battery_soc_simulation.png

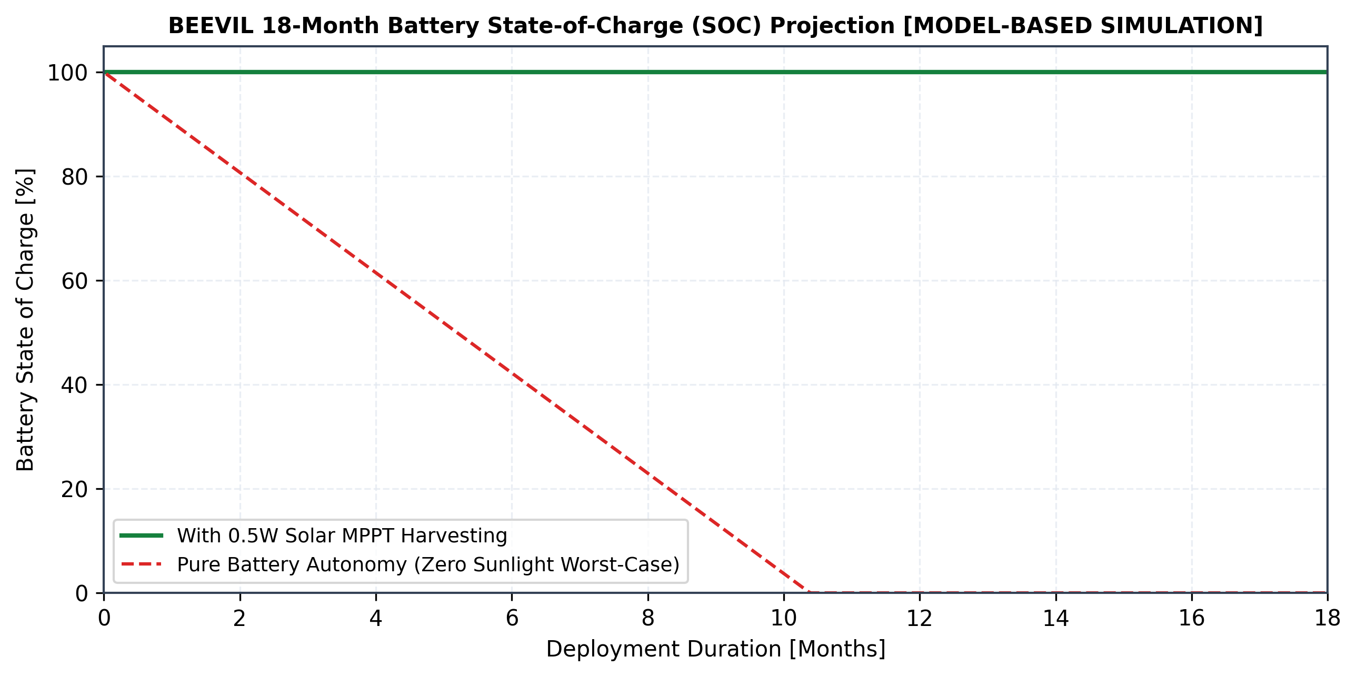
docs/media/results/battery_soc_simulation.png
