atharveeee-netizen/beevil-knievel/docs/media/results/cusum_detection.png

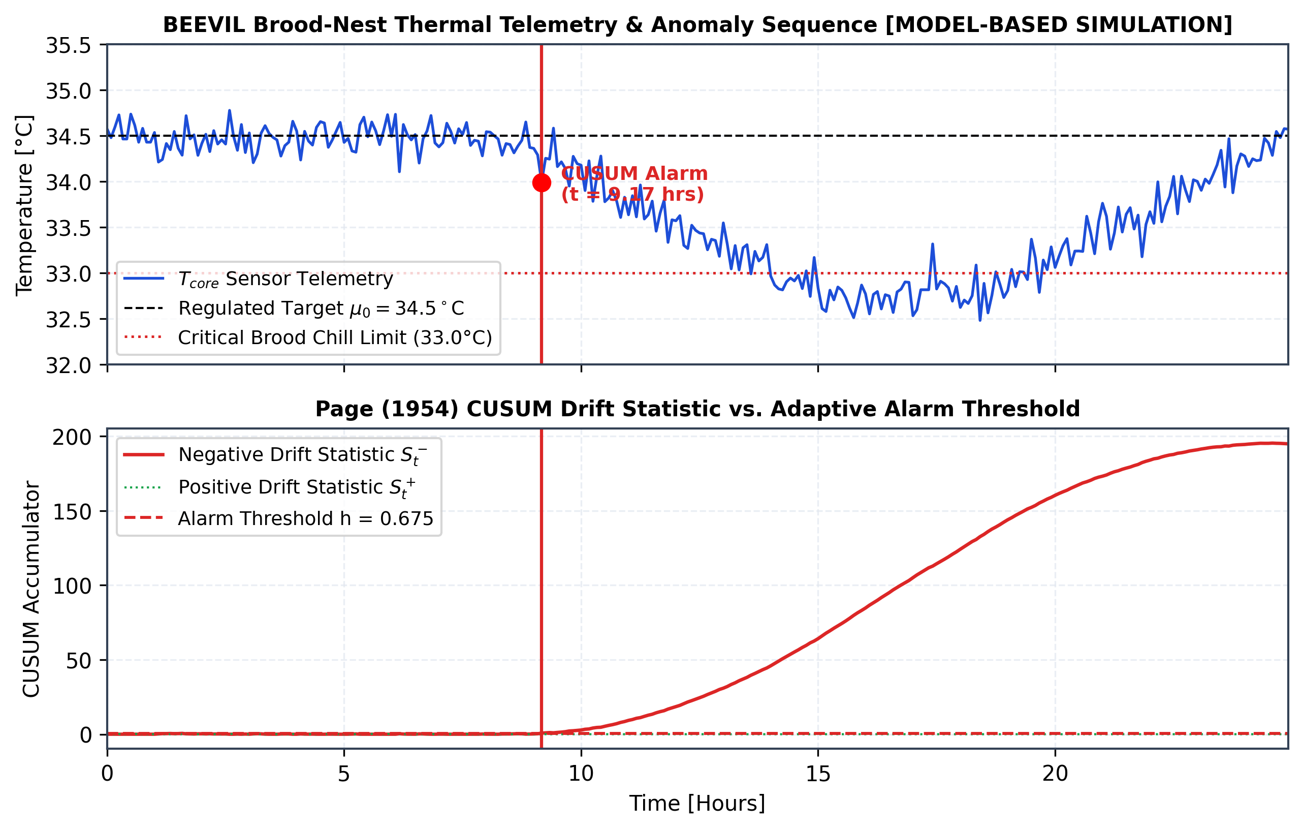
docs/media/results/cusum_detection.png
