atharveeee-netizen/beevil-knievel/docs/media/results/duty_cycle_simulation.png

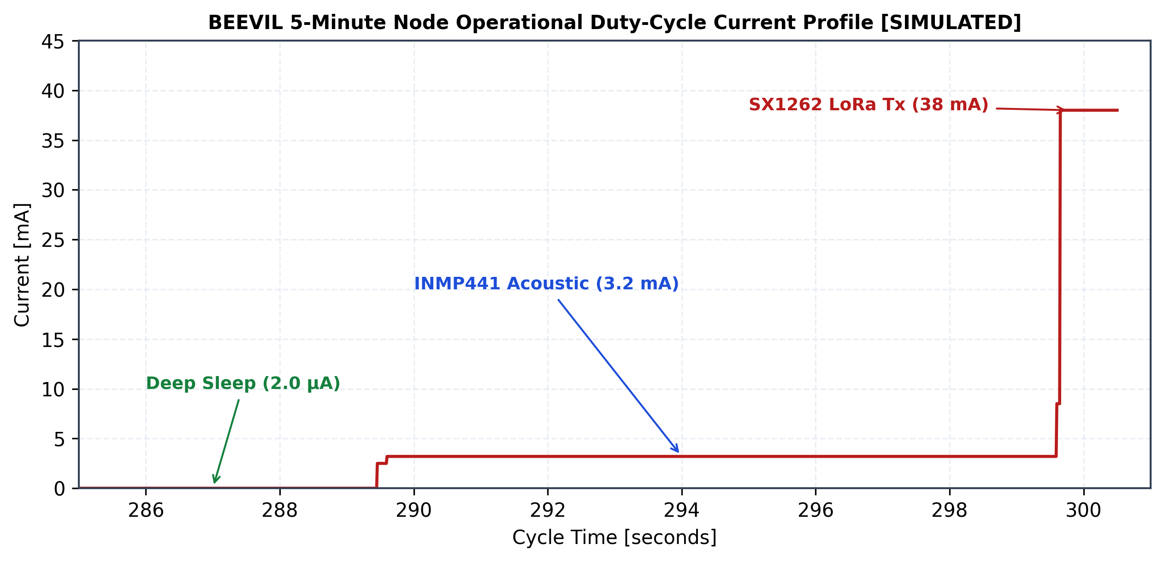
docs/media/results/duty_cycle_simulation.png
