atharveeee-netizen/beevil-knievel/docs/media/results/energy_budget.png

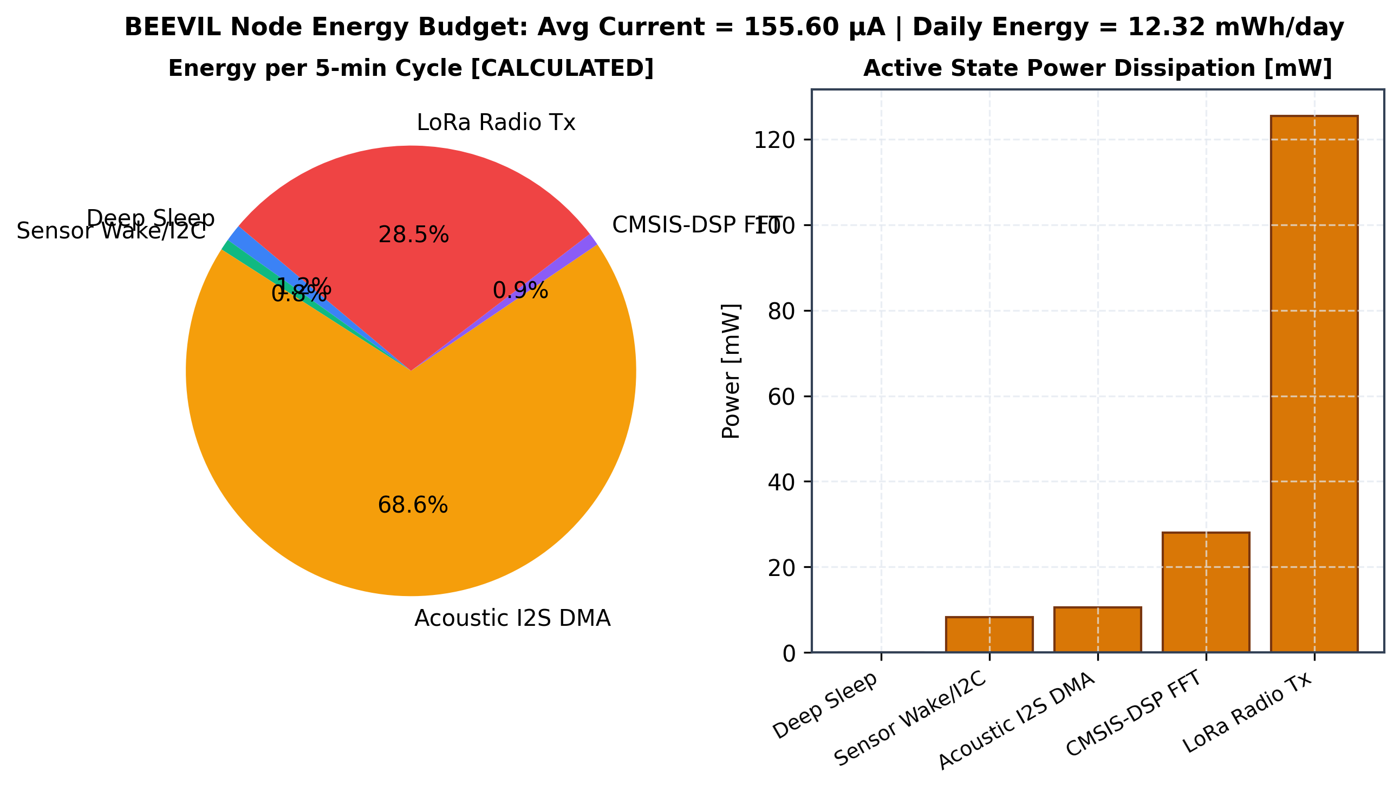
docs/media/results/energy_budget.png
