atharveeee-netizen/beevil-knievel/docs/media/results/fft_resolution_validation.png

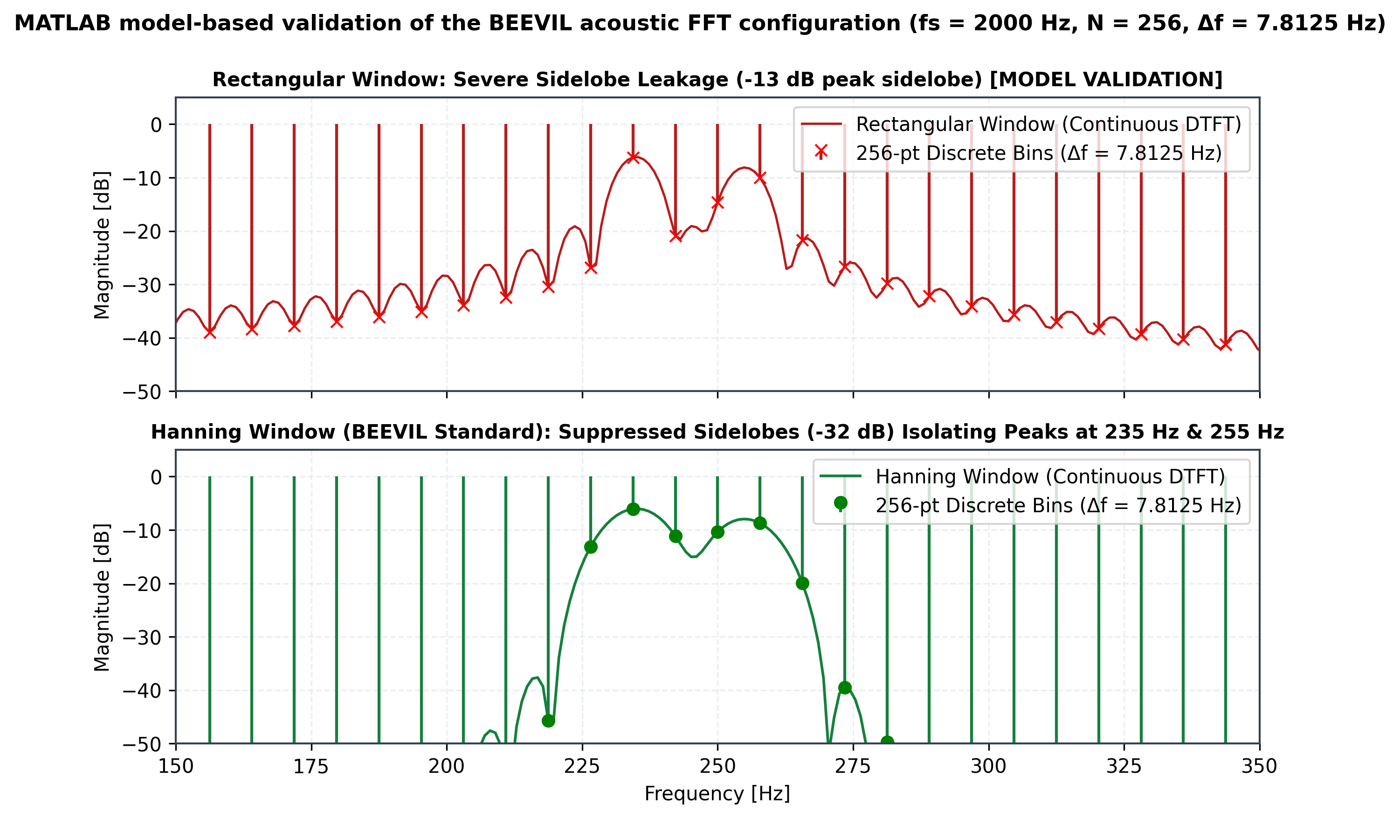
docs/media/results/fft_resolution_validation.png
