atharveeee-netizen/beevil-knievel/docs/media/results/hive_thermal_model.png

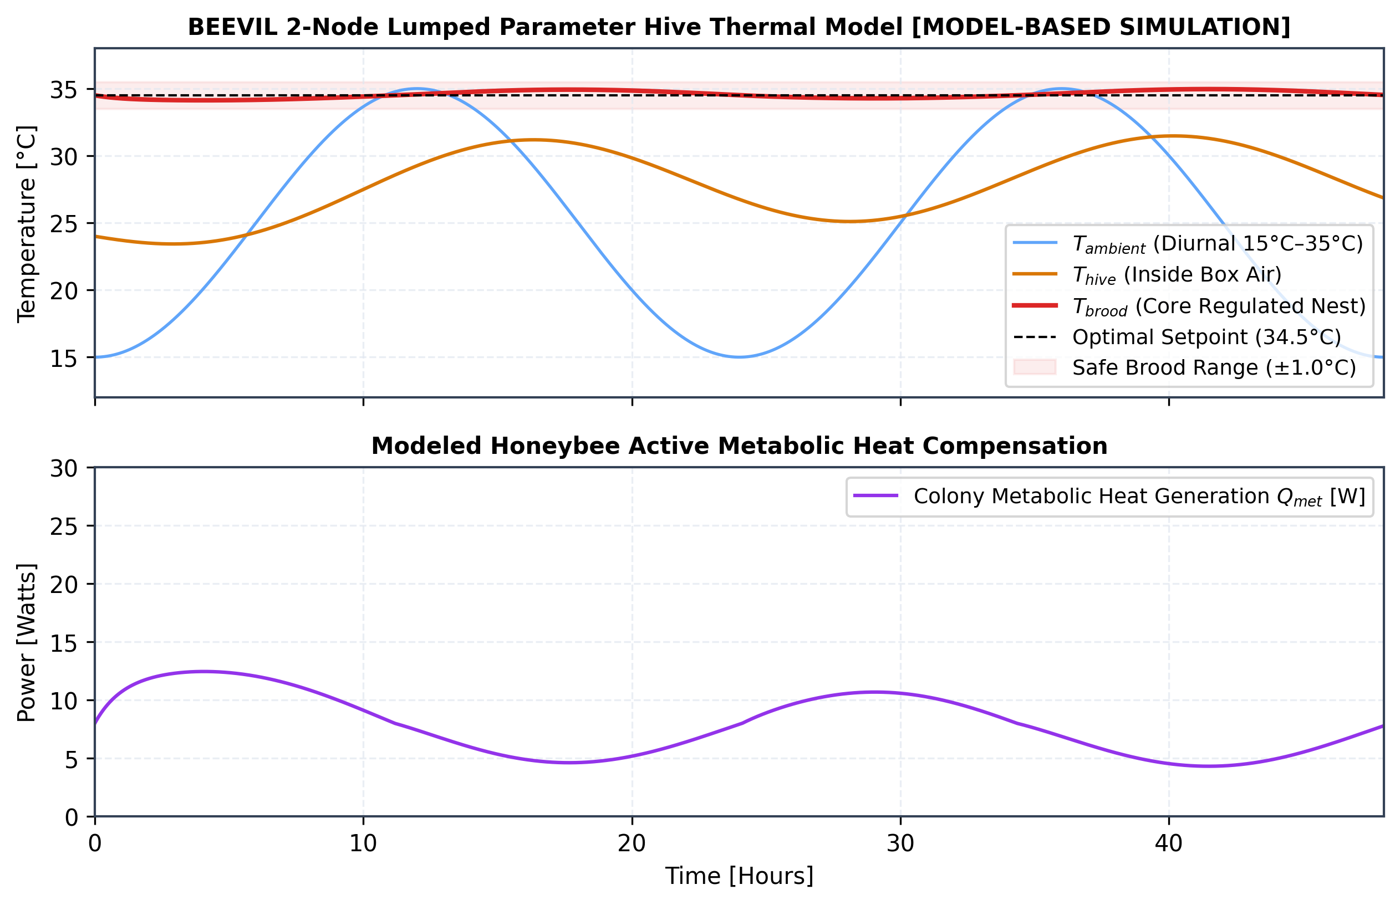
docs/media/results/hive_thermal_model.png
