atharveeee-netizen/beevil-knievel/docs/media/results/rf_link_budget.png

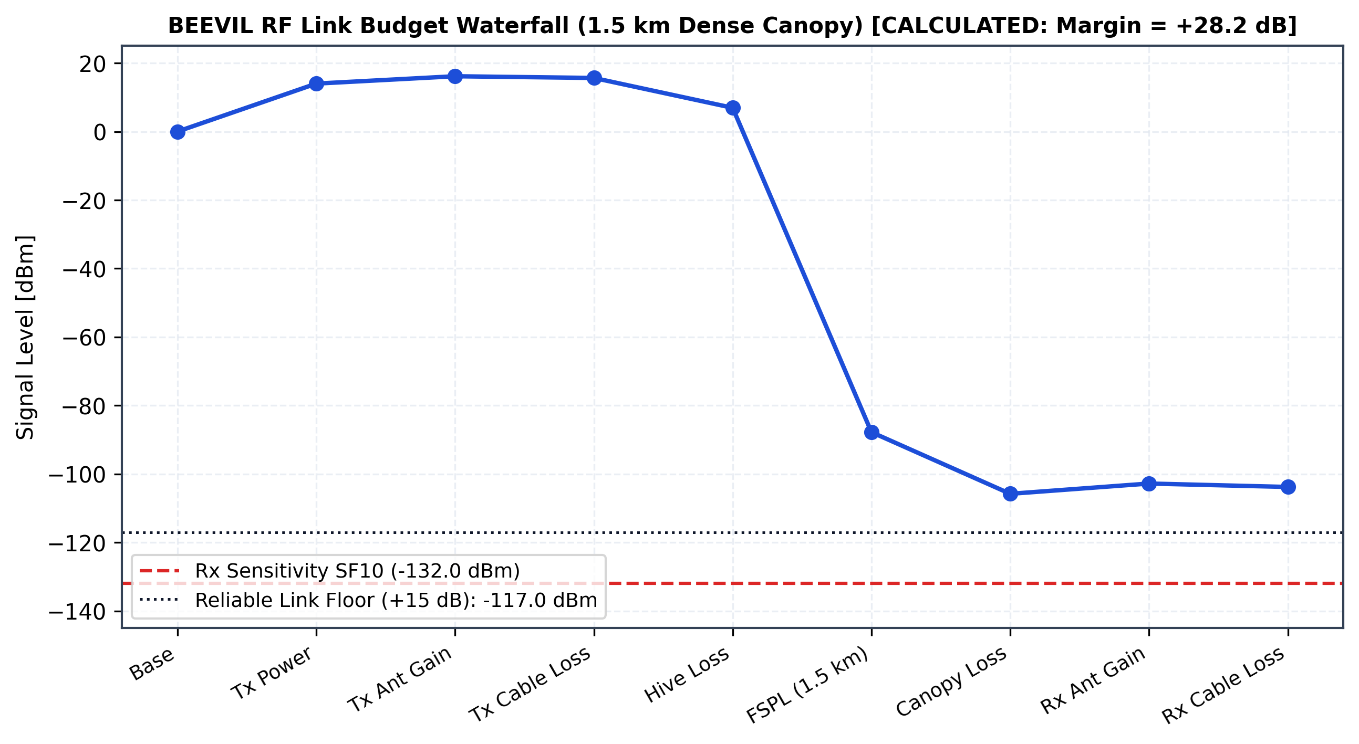
docs/media/results/rf_link_budget.png
