atharveeee-netizen/beevil-knievel/docs/media/results/rf_range_sweep.png

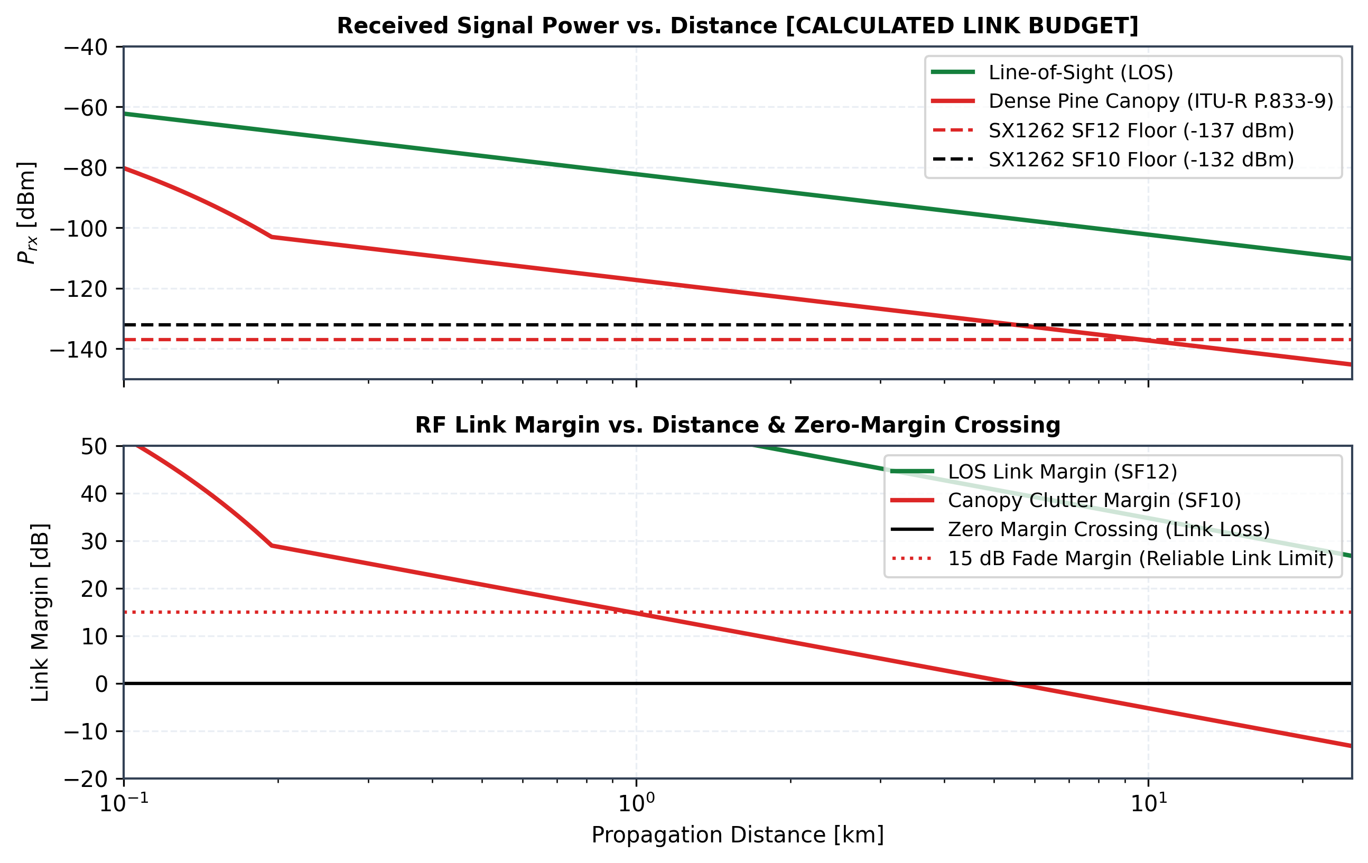
docs/media/results/rf_range_sweep.png
