atharveeee-netizen/beevil-knievel/docs/media/results/telemetry_scaling.png

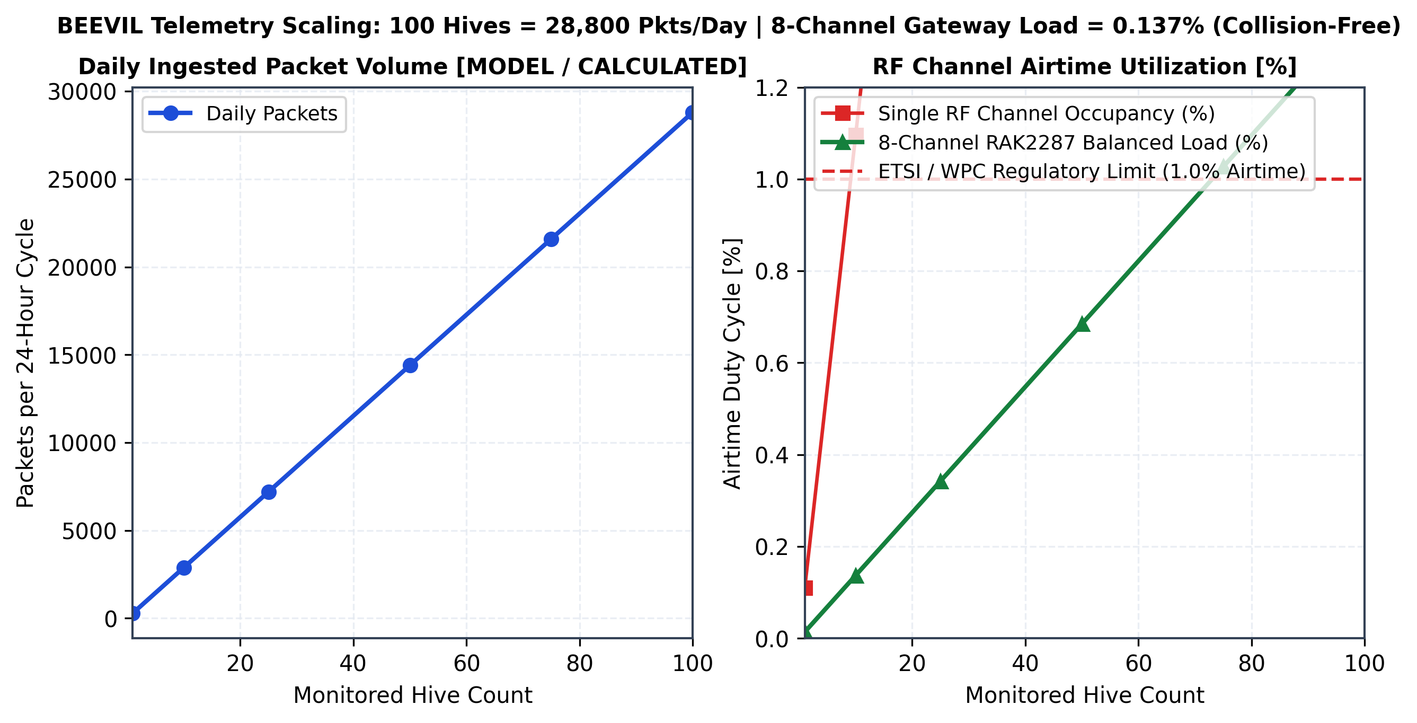
docs/media/results/telemetry_scaling.png
