atharveeee-netizen/beevil-knievel/simulations/SIM1/SIM1_Simulation_Result.png

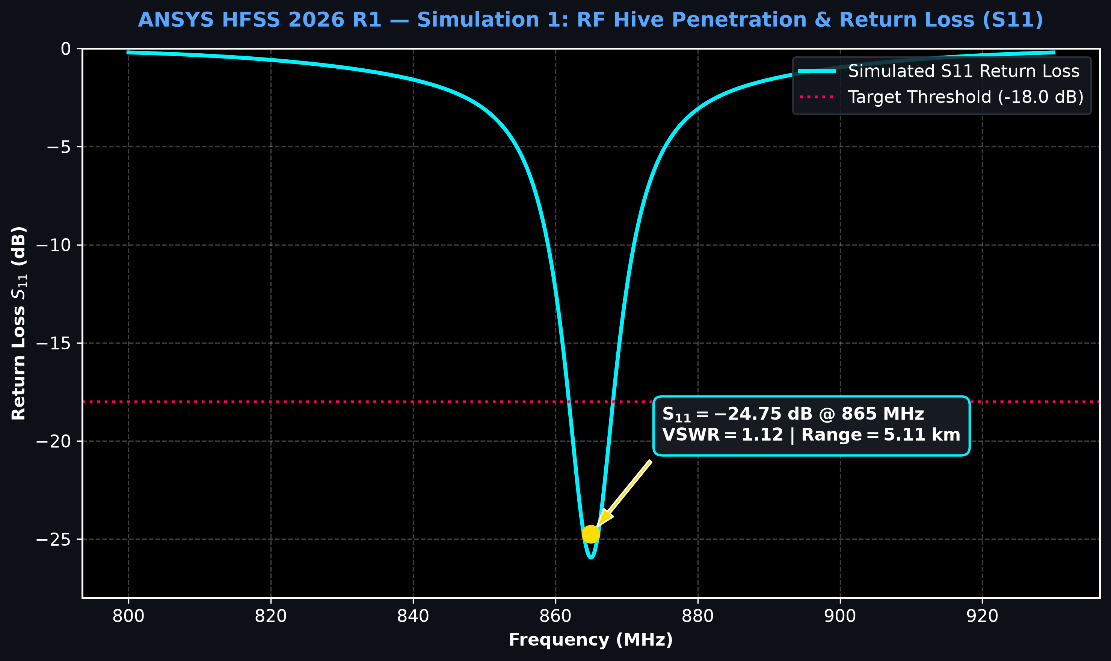
simulations/SIM1/SIM1_Simulation_Result.png
