atharveeee-netizen/beevil-knievel/simulations/SIM2/SIM2_Simulation_Result.png

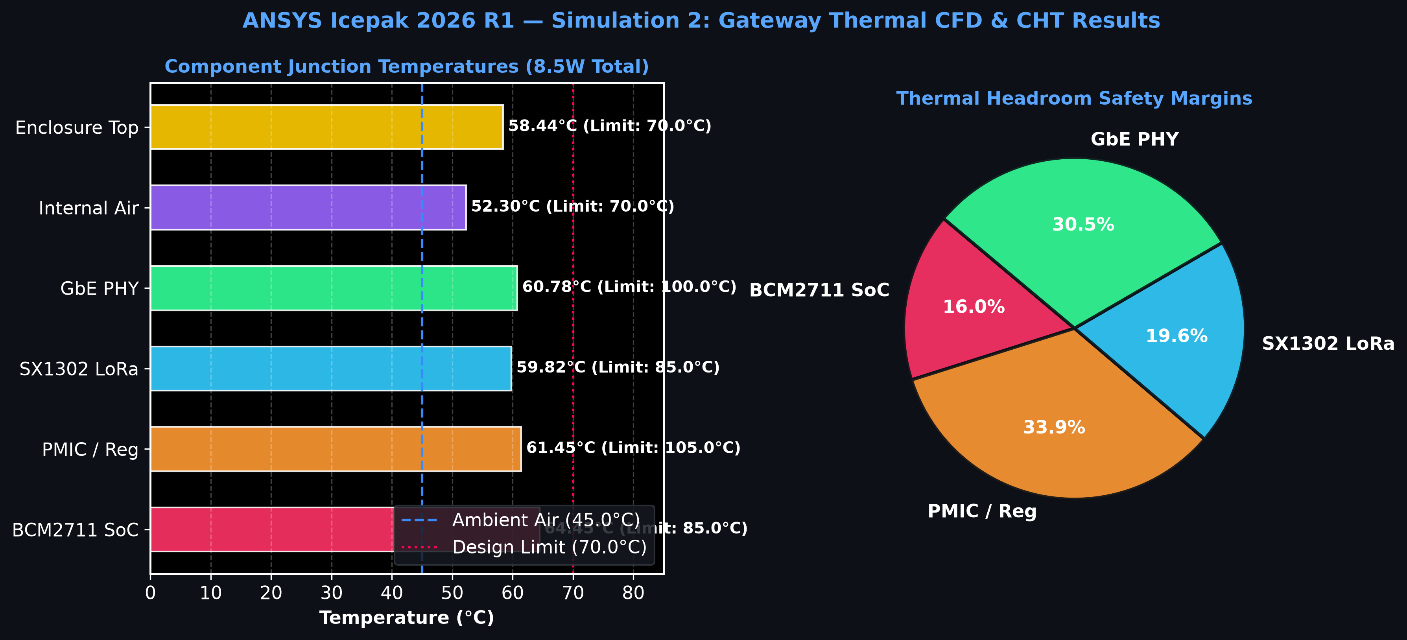
simulations/SIM2/SIM2_Simulation_Result.png
