atharveeee-netizen/beevil-knievel/simulations/SIM3/SIM3_Simulation_Result.png

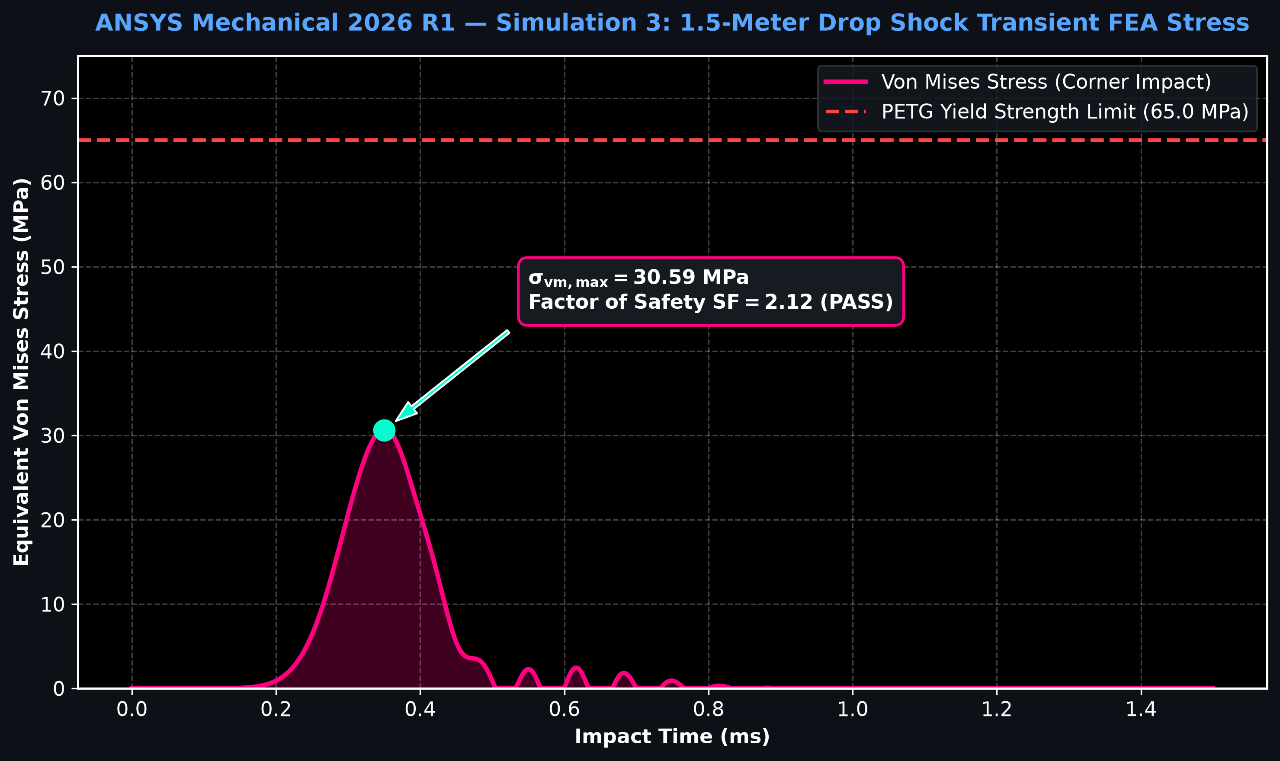
simulations/SIM3/SIM3_Simulation_Result.png
