atharveeee-netizen/beevil-knievel/simulations/SIM4/SIM4_Simulation_Result.png

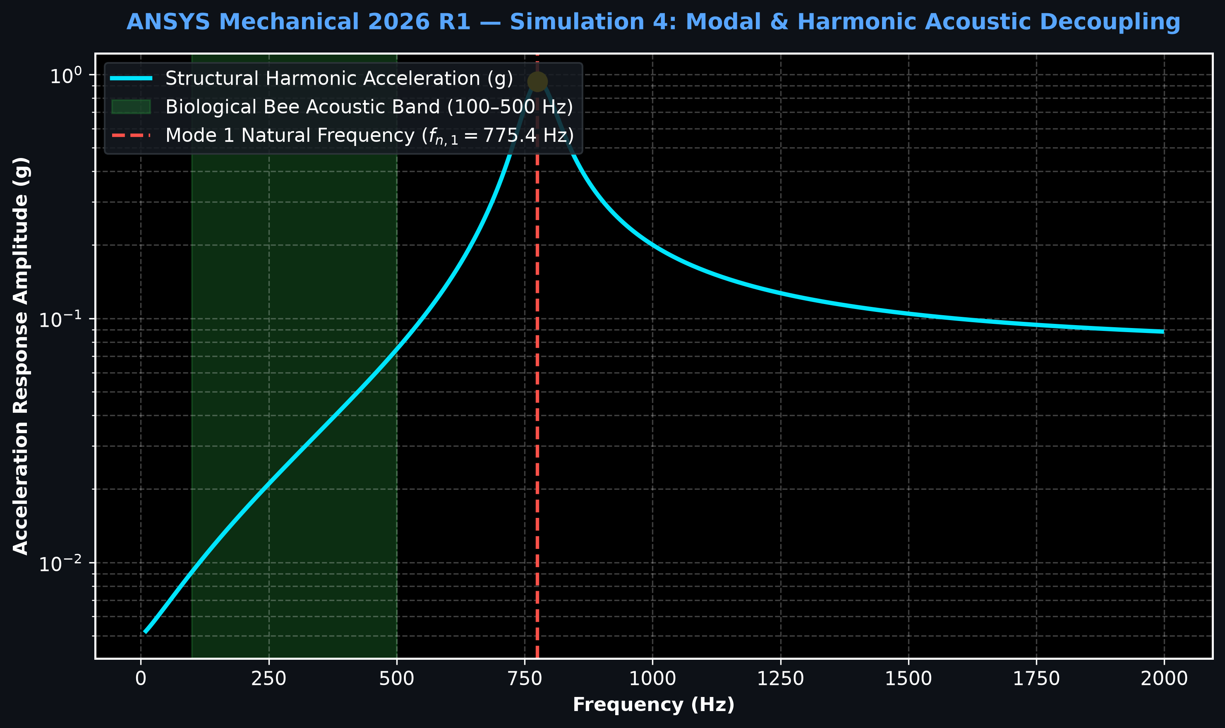
simulations/SIM4/SIM4_Simulation_Result.png
