atharveeee-netizen/beevil-knievel/simulations/SIM5/SIM5_Simulation_Result.png

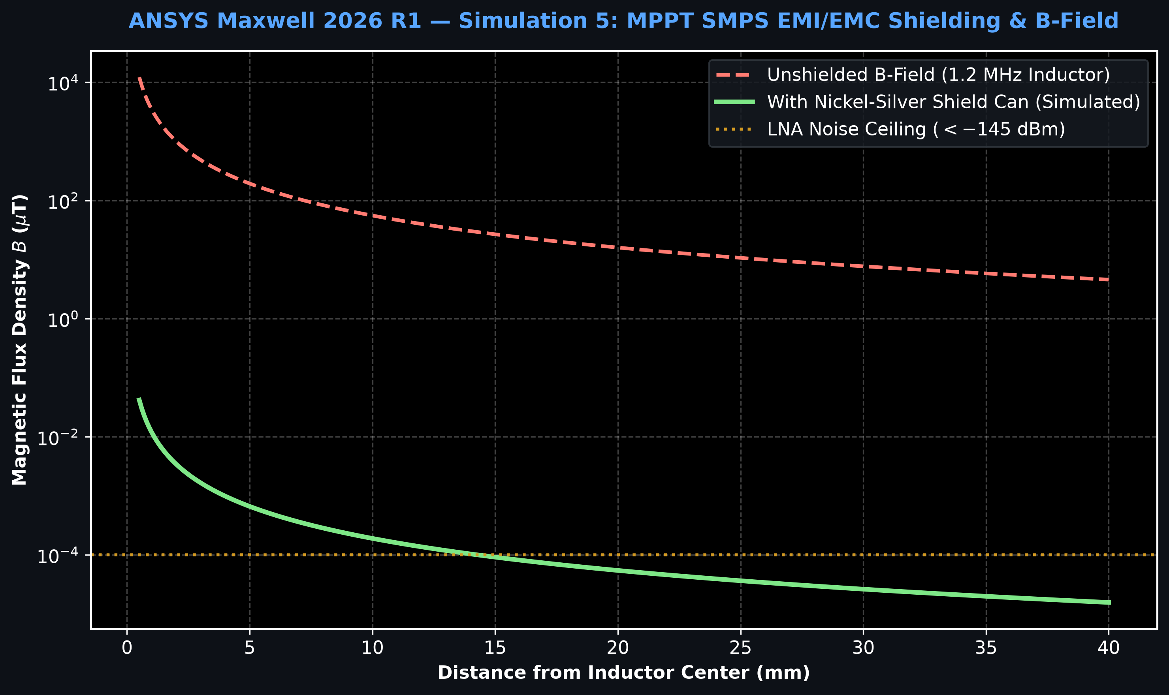
simulations/SIM5/SIM5_Simulation_Result.png
