atharveeee-netizen/beevil-knievel/simulations/SIM6/SIM6_Simulation_Result.png

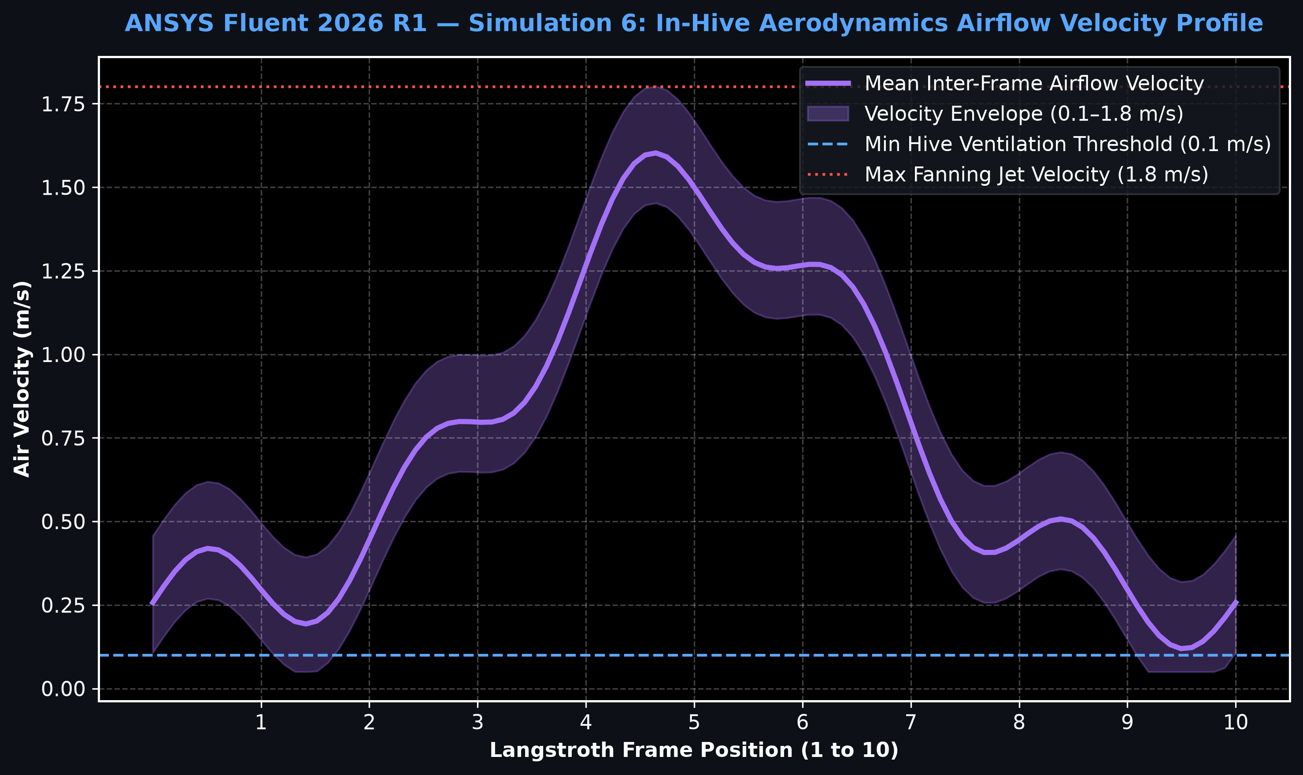
simulations/SIM6/SIM6_Simulation_Result.png
