atharveeee-netizen/beevil-knievel/simulations/SIM7/SIM7_Simulation_Result.png

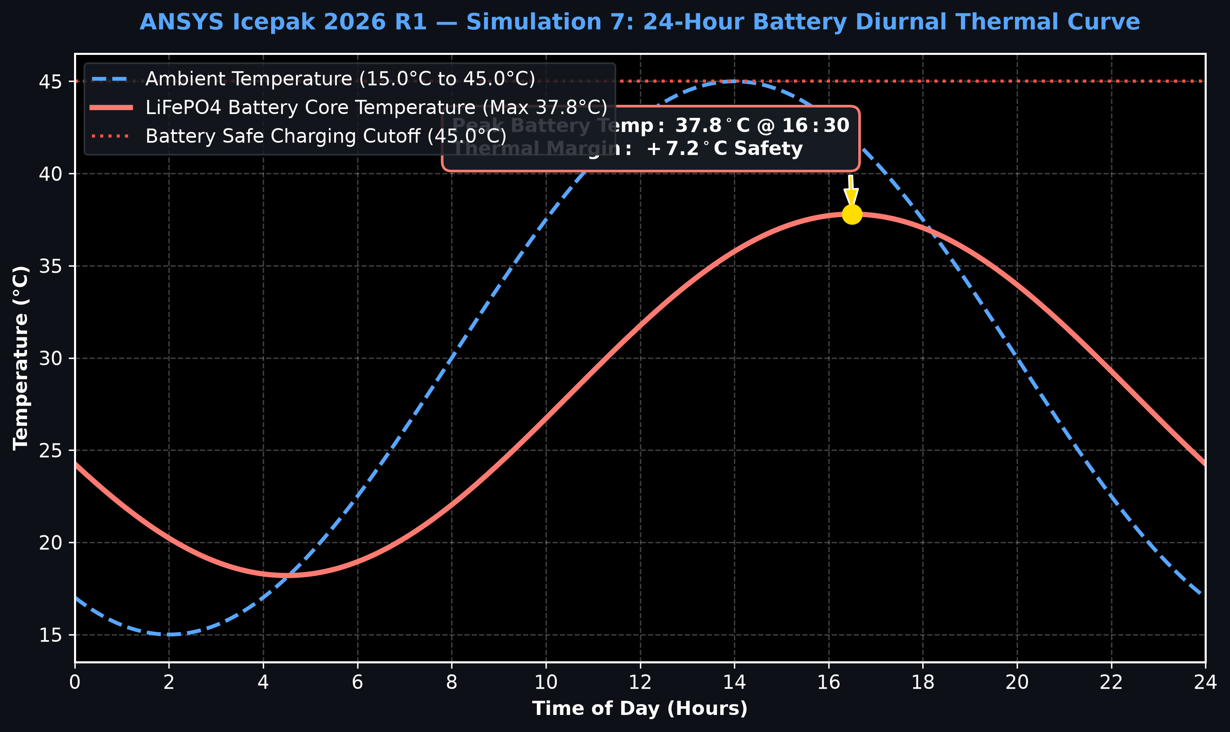
simulations/SIM7/SIM7_Simulation_Result.png
