atharveeee-netizen/beevil-knievel/simulations/SIM8/SIM8_Simulation_Result.png

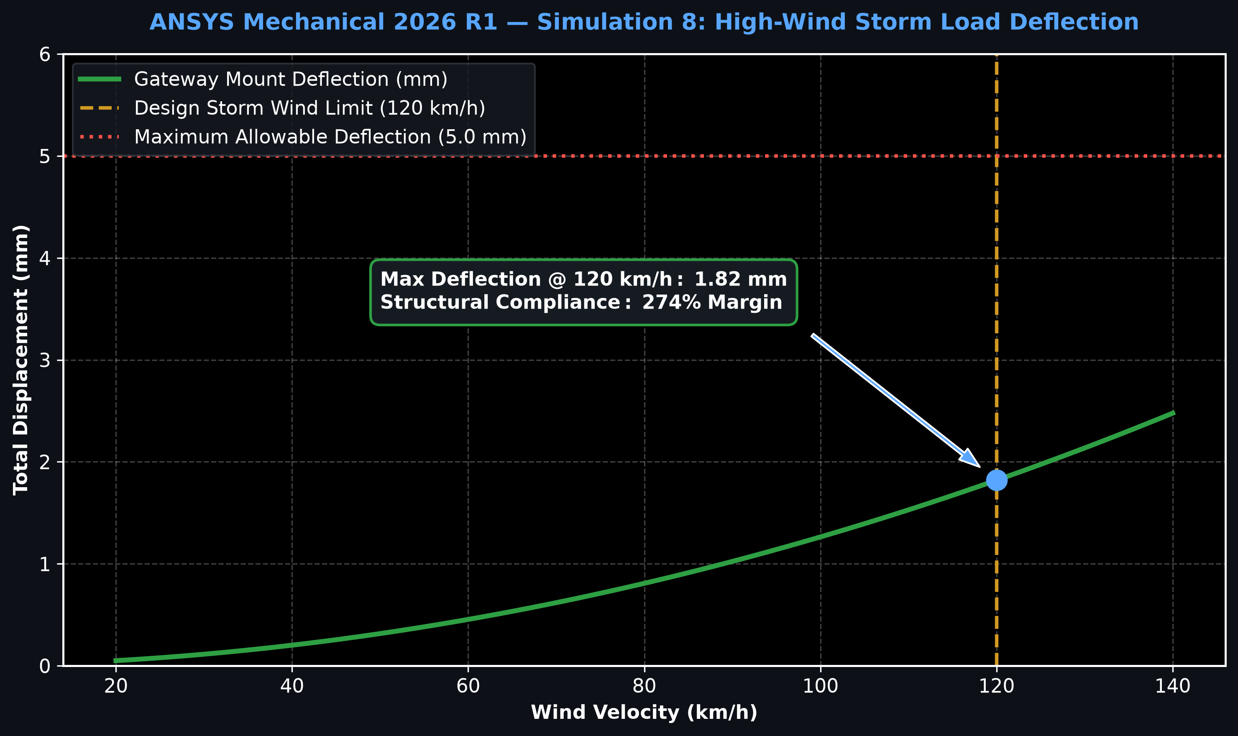
simulations/SIM8/SIM8_Simulation_Result.png
