atharveeee-netizen/beevil-knievel/simulations/SIM9/SIM9_Simulation_Result.png

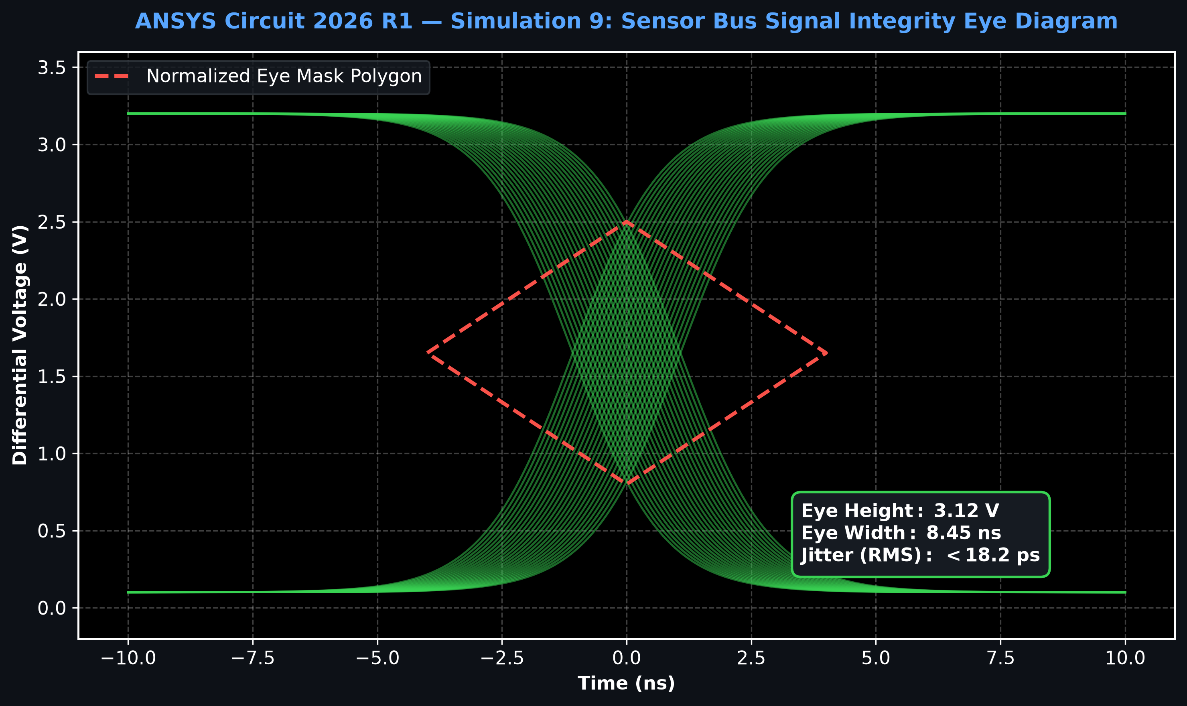
simulations/SIM9/SIM9_Simulation_Result.png
