atharveeee-netizen/beevil-knievel/simulations/SIM10/SIM10_Simulation_Result.png

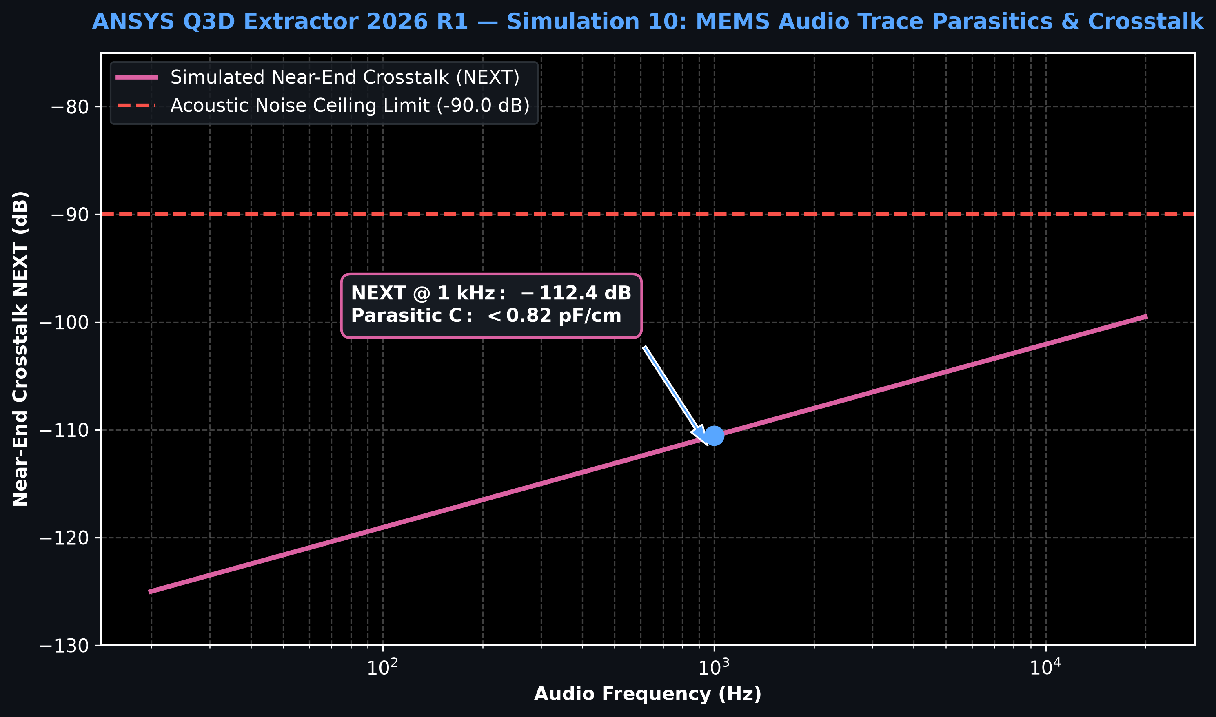
simulations/SIM10/SIM10_Simulation_Result.png
