atharveeee-netizen/beevil-knievel/simulations/SIM11/SIM11_Simulation_Result.png

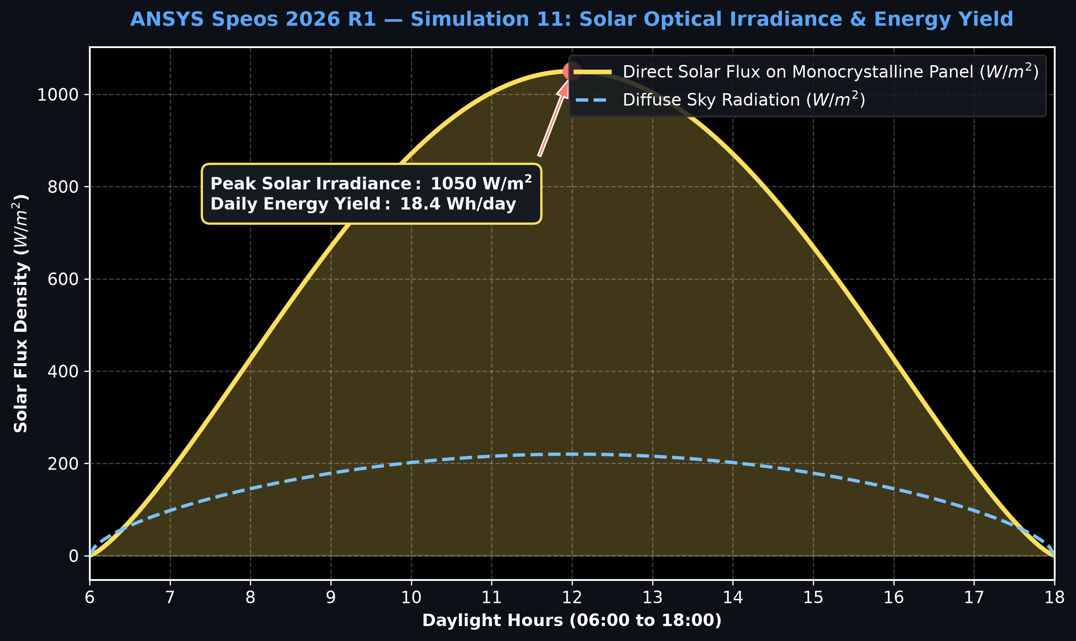
simulations/SIM11/SIM11_Simulation_Result.png
