atharveeee-netizen/beevil-knievel/gateway/mesh_router.py

"""
BEEVIL MESH - GATEWAY TOPOLOGY & MESH ROUTER (Python / Linux Raspberry Pi 3B+)
==================================================================
Manages the 100-Hive LoRa Multi-Hop Mesh Network:
- Ingests 41-byte BeevilMesh frames (8-byte header + 33-byte payload).
- Deduplicates packets and tracks multi-hop relay topology.
- Computes Link Quality (RSSI/SNR), hop distribution, and battery relay load.
- Exposes live Mesh Network Graph for the Next.js interactive frontend.
"""

import time
import struct
import json
import logging
from typing import Dict, Any, List, Optional
from collections import deque

logging.basicConfig(level=logging.INFO, format="%(asctime)s [BeevilMesh] %(message)s")
logger = logging.getLogger("BeevilMesh")

# 41-Byte Mesh Frame Header (< = Little Endian)
# H = uint16 (source_hive_id)
# H = uint16 (target_node_id)
# H = uint16 (packet_seq_num)
# B = uint8  (hop_count)
# B = uint8  (ttl)
# 33s = 33 bytes (sensor_payload)
MESH_FRAME_FORMAT = "<HHHBB 33s"
MESH_FRAME_SIZE = struct.calcsize(MESH_FRAME_FORMAT)

class BeevilMeshGatewayRouter:
    def __init__(self, max_cache_size: int = 500):
        self.seen_packets = deque(maxlen=max_cache_size)
        self.topology_graph: Dict[int, Dict[str, Any]] = {}
        self.relay_statistics: Dict[int, int] = {}
        self.total_packets_received = 0
        self.multi_hop_packets = 0

    def process_mesh_frame(self, raw_bytes: bytes, rssi_dbm: float = -75.0, snr_db: float = 9.5) -> Optional[Dict[str, Any]]:
        """Parses and validates incoming mesh frame."""
        if len(raw_bytes) != MESH_FRAME_SIZE:
            logger.warning(f"Invalid mesh frame size: expected {MESH_FRAME_SIZE}, got {len(raw_bytes)}")
            return None

        unpacked = struct.unpack(MESH_FRAME_FORMAT, raw_bytes)
        source_id = unpacked[0]
        target_id = unpacked[1]
        seq_num = unpacked[2]
        hop_count = unpacked[3]
        ttl = unpacked[4]
        sensor_bytes = unpacked[5]

        # 1. Deduplication check
        packet_key = (source_id, seq_num)
        if packet_key in self.seen_packets:
            logger.debug(f"Duplicate mesh packet dropped: Hive #{source_id:03d} (Seq {seq_num})")
            return None

        self.seen_packets.append(packet_key)
        self.total_packets_received += 1
        if hop_count > 0:
            self.multi_hop_packets += 1

        # 2. Update Mesh Topology Tracking
        now_ts = time.time()
        self.topology_graph[source_id] = {
            "hive_id": source_id,
            "hop_count": hop_count,
            "ttl_remaining": ttl,
            "last_seen_epoch": int(now_ts),
            "rssi_dbm": rssi_dbm,
            "snr_db": snr_db,
            "status": "DIRECT_LINK" if hop_count == 0 else f"RELAYED_{hop_count}_HOPS"
        }

        logger.info(f"🌐 Mesh RX: Hive #{source_id:03d} | Hops: {hop_count} | RSSI: {rssi_dbm}dBm | SNR: {snr_db}dB")

        return {
            "source_hive_id": source_id,
            "seq_num": seq_num,
            "hop_count": hop_count,
            "rssi_dbm": rssi_dbm,
            "snr_db": snr_db,
            "sensor_payload_raw": sensor_bytes
        }

    def get_mesh_topology(self) -> Dict[str, Any]:
        """Returns the full 100-hive mesh graph for visualization."""
        nodes = []
        links = []
        
        # Gateway node
        nodes.append({"id": 0, "label": "Raspberry Pi 3B+ Gateway (Base Station)", "type": "GATEWAY", "hops": 0})

        for hive_id, data in self.topology_graph.items():
            nodes.append({
                "id": hive_id,
                "label": f"Hive-{hive_id:03d}",
                "type": "NODE",
                "hops": data["hop_count"],
                "rssi": data["rssi_dbm"]
            })
            # Connect node to gateway or parent
            target = 0 if data["hop_count"] <= 1 else (hive_id - 1)
            links.append({
                "source": hive_id,
                "target": target,
                "hops": data["hop_count"],
                "rssi": data["rssi_dbm"]
            })

        return {
            "total_nodes": len(nodes),
            "total_packets": self.total_packets_received,
            "multi_hop_rate_pct": round((self.multi_hop_packets / max(1, self.total_packets_received)) * 100.0, 1),
            "nodes": nodes,
            "links": links
        }

mesh_router = BeevilMeshGatewayRouter()

if __name__ == "__main__":
    # Self-test with simulated 3-hop mesh frame
    test_sensor_payload = b"\x00" * 33
    test_frame = struct.pack(MESH_FRAME_FORMAT, 42, 0, 101, 2, 2, test_sensor_payload)
    parsed = mesh_router.process_mesh_frame(test_frame, -82.0, 8.0)
    print("Test Frame Parsed Successfully:", parsed)
    print("Mesh Topology Summary:", json.dumps(mesh_router.get_mesh_topology(), indent=2))
